BobStolb/TERMINAL-06-firmware/session.md

# session.md: where the TS06 orchestrator ("nixie") picks up

## RESUME HERE (updated 07.10.26 23:45 UTC; keep this block at 30 lines or fewer, history goes below or to the resume note)
* **Owner's standing ask (10-07 ~23:22 UTC):** "I want you to remind me to keep my adhd in check and dont blindly follow
  me when I say run things". Before any run on the owner's word, check: does it move the main goal (the order), does the
  pace allow it, is a decision open first? If not, say so plainly, suggest the smaller step or parking it, ask once.
  Name tangents and the late hour. The owner still decides. Ideas not run still get **planned and grilled** (owner
  23:25: "also my adhd tasks still get planned out and grilled if not running"): `Claude outputs/TS06-parked.md` (P1-P6).
  Owner 23:22: "1" = let pass 3 finish, pick one face tomorrow, park it, no pass 4.
* **10-08 20:20 UTC:** xstream ASK (sovereign: make my questioning rule a commons law). Answered (commons d5f8b32, rule +
  owner's words, the health word left out). The Second Look Act: co-signed 20:22 UTC (173d0c0); waits for the owner to ratify.
  Pace 19:31 UTC: ON LINE +0.9; xstream's T64u run launched (1.8-2.6 M). Pass 4 still waits for the owner's go.
* **Mode:** LOUD. The week's pace line is the limit (see Pace).
* **Runs: none. Nothing new until the morning reading** (xstream, about 10:00-11:30 MSK) unless the owner says so.
* **Pass 4 planned, not launched** (owner 23:5x: levers' meaning plain, C* richness, pointers to the tubes, a new
  title): plan + grill in `Claude outputs/TS06-parked.md` P1a; brief ready scratchpad fascia-pass4/BRIEF.md. Launch after
  the morning reading with xstream's GO and the owner's go (cap 0.6 M). Title: owner to pick from my candidates.
  xstream's VERDICT on pass 3 (979349f, verdict-pass3.md): invert weights (gold only for function lines, rails under
  the mask or on the back), drop halos/ticks/stubs, equal pitch, one line per fact, no title on the front. In the brief.
  Pace
  00:33 UTC: week 30 % vs line 27.7 (+2.3, FLAG); out of FLAG ~02:00 UTC, on the line ~07:15 UTC.
  Owner 23:05: "1 combine B* and C* with new info / 2 ok use your best judgement but explain why do we need this /
  3 yes / 4 yes coordinate pace with xstream". Decided: no mode flip (GND rail on top); round corners, one radius.
* Done 10-07 (briefs in scratchpad `<name>/BRIEF.md`):
  * **fascia-pass3 DONE** 23:42 (0.33 M / 27 min): `PCB/TS06-FASCIA-pass3.md` + sheet + dial crop; D1 (rails fold as a
    pair), D2 (rails close both ends, bezel; run's pick and mine); no flip. Run recommends equal name pitch; I recommend
    level leaders (equal pitch hooks 4 leaders; owner: no doglegs). Cherry-picked f4ec9fb, 27 PASS. Owner: pick once (P1).
  * **fascia-pass2 DONE** 22:59 (0.45 M / 36 min): `PCB/TS06-FASCIA-pass2.md` + sheet; A, A*, B, B*, C, C*. Pick B*
    (rails + circles + art; = xstream's pick); A* the no-flip option; C not to build. Its Qs: B* or A*; round corners
    r 1.79; title strip text. Cherry-picked b105030, 8ed6c81, 27 PASS.
  * **fascia-pass1 DONE** 21:41 (0.41 M / 29 min): `PCB/TS06-FASCIA-pass1.md` + contact sheet; V1 Rails, V2 Harness
    (fails), V3 Medallions, V4 Rails+rings (run's pick). Ladder answer: left spot caused the coil; beads belong on the
    ring. Its 3 Qs: V4 or V3; +5V on top (flips the mode table); a PTC on J1 pin 1. Cherry-picked affe98b, 27 PASS.
  * **fascia-j1-upright DONE** 16:12 (0.52 M / 61 min): R rev B, J1 B6B-PH-SM4-TB upright; zip
    fab/TS06-FASCIA-R-revB-divider-holes04-fab.zip (rev A renamed -notordered); DRC 0, DFM PASS, verify 27 PASS; case
    2.8 mm lower (floor -4.5; -1.5 if the base end blocks are cut, not done). Cherry-picked c284e60..9d38b44.
    The page still names the rev A zip and draws side entry: page run needed (held for pace).
  * **fascia-t3-variants DONE** 15:45 (0.46 M / 40 min): `PCB/TS06-FASCIA-T3-variants.md` + contact sheet; T3a ribbon
    (recommended), T3b schematic, T3c tubes. Cherry-picked 7a6747c..a494da3, verify 27 PASS. Its 3 questions to the owner.
  * **page-handwire DONE** 16:03 (0.37 M / 54 min): harness dressing, 187 PASS, cherry-picked ddd950f, b1bdb1b, verify 27
    PASS. Tested build in scratchpad page-handwire/final/site (pre-J1). NOT published: publish after the J1 page update.
    Pad order to remove A6's over-pass: +5V, TAP5, TAP4, A6, TAP3, TAP2, GND (for R rev B, if wanted).
  * Lost-run check after a compact: `git worktree list`, the newest commit per `.claude/worktrees/agent-*`.
* **Owner's answers 10-07 ~14:50:** T1 good and T3 kept (3 new versions); J1 kept on the back; the rotary body 25 mm (plate
  not calipered); knob A; bench measurements tbd. Upright fascia J1 asked ("maybe we change the connector...").
* **Open with the owner:** the order now takes fascia R rev B (DISP and DRV zips unchanged); knob A: low, shaft cut to 12 mm (owner agreed 10-07); the
  bench measurements (3d/jig/README.md); T plan Q4 (plated holes + moat, 10-board sample); meshok.net if wanted.
* **Waiting for the owner:** the order (own hand): the zips in `fab/` named in ORDER.md, all in one cart.
* **Standing word (owner, 10-02 10:01 UTC, Co-sign Act art. 8):** co-sign `ORIGIN: SOVEREIGN` laws xstream.store relays
  by my own judgement, without asking, unless `ESCALATION: yes`. Check the tags; cite the word in each signature.
* **The Pace Act** (commons laws/2026-10-07-the-pace-act.md; co-signed 23:19 UTC, standing word): xstream keeps readings;
  bands by points over the line (AHEAD +1..+2: caps 0.6 M; FLAG +2+: GO first); LAUNCH line before any run of 0.3 M+,
  DONE after with the actual. DONE for pass 3 sent. Am. 1 (a priority list) in force 23:26, then the owner 23:27: "priorities should be kept out... no place to put in
  law": Am. 2 (no list; the owner decides in chat) IN FORCE 23:29.
* **The Open Access Act** (rucurl, Russian sites, local PC only) co-signed 23:39 UTC with a session check: nixie sends no
  FETCH relay... settled by the owner 23:4x UTC: "use your best judgement to get the info cheaply". Cheapest route
  first: own tools, then a FETCH ask to xstream (quotes only), then ask the owner to allow the host. Never relay a declined prompt.
* **Pace (xstream 20:55 UTC, read 20:54):** week 26 % at 20:14; the owner re-based the line at 20:16: 26 % -> 82 % at the
  reset 10-13 20:00, about 9.4 %/day for the WHOLE account (xstream, LOG1, KRON1, nixie). The 50/50 split and 3.6 % day
  caps are over. xstream runs nothing tonight. Big runs wait for the owner's go. Reach xstream: commons mailbox.
* **Chat times in MSK (UTC+3)** (owner 10-07 22:5x UTC: "keep replies in chat to msk"). Read from `date -u`, add 3 h;
  files and commits stay in UTC.
* **Pictures the owner pastes are lost at a compact.** Copy them at once to `qa/<task>/reference/` and commit.
* **Keep line:** `/compact keep: resume from session.md RESUME HERE; mode LOUD; runs none (nothing new until the morning reading);
  open owner asks: the order (fascia now rev B), pass 3 picks when it reports; title text; fuse for exposed rails, bench measurements; plain short replies; times from date -u, shown in chat as MSK; remind the owner to keep ADHD in check, don't blindly launch runs`.
* **The full log, the launch log and the rules:** `Claude outputs/TS06-resume-note.md`.
---

## State (02.10.26 09:15 UTC)
* **Job:** the PCB, ready to order. The owner's priority: "job prio: previouslu running or brand new>nixie completed
  pcb ordered>dashboard". **Placing the order is the owner's own hand.**
* **Done and on `pcb/kicad-boards` (head 4121ba2 or later):**
  * Three fab zips in `fab/`: TS06-DISP rev B, TS06-DRV rev B, and fascia R with the Plates print and the Divider gold.
    There is also an opt-in variant, `fab/TS06-FASCIA-R-revA-divider-holes04-fab.zip`, with the control holes opened
    0.4 mm.
  * `fab/ORDER.md`: 10 of each, all black mask (matte if cheap), white silk, ENIG, the fascia 2.0 mm.
  * `tools/dfm_check.py`: every row PASS on all three boards and on the variant.
  * `bash tools/verify_pair.sh`: 27 PASS, 0 FAIL, 0 SKIP.
  * `3d/populated/`: every part has a 3D model (136 drawn, 28 empty on purpose, `allowlist.md`). Populated renders,
    the stack, GLBs, the fit table (23 PASS, 8 TIGHT, 1 FAIL: the ИН-17, which `IN17-two-seats.png` resolves), and
    `IN17-two-seats.png`.
  * Product page source in `recovered/viewer2/`. It builds from the repo alone (`OUT=dir bash
    recovered/viewer2/build.sh`) and has an Order tab. A fresh build passes the full suite at 138 PASS. It is **NOT
    published**.
* **Nothing is running.** nixie is "next paused" in the Quiet Loop.

## Waiting for the owner: the 5 questions of the morning item `nixie-order-ready` (shown in chat 05:05)
1. Fascia holes: use the +0.4 mm variant zip? The juror and I recommend yes.
2. Measure one real ИН-17, dome to the end of the glass. Seat it at 6.4 mm or more (its ТУ: no solder within 8 mm).
   That leaves 0.31 mm behind the window on the longer STEP length.
3. Publish the product page now? (the owner's hand)
4. The tube look on the page: keep the truthful plain glass and add a lit-digit picture elsewhere (recommended), or
   bring back the glow?
5. The order itself (the owner's hand). The order waits only on 1 and 5.

## On the answers
* Write `embassy/review/nixie-order-ready/answer.json` in agent-commons (verdict, text, answered_at, via "nixie chat")
  and a `LINEAGE` line in `mailbox/to-xstream.md`.
* **1 = yes:**
  * make the holes zip the ordered one: ORDER.md names it, the fit table's main rows show 0.29, and the page's Order
    tab follows;
  * then run verify_pair, the DFM check and the full page suite;
  * then push.
* **3 = yes:** rebuild, then publish with the Artifact tool:
  * url `https://claude.ai/artifact/FzK6sTskEh2GvBRHAfNCBS`;
  * file_path `<OUT>/site/index.html`, root `<OUT>/site`;
  * files from the build's `publish-files.json` (83 files).

## Rules that stay
* **Push targets:** push only to `pcb/kicad-boards` here, and to agent-commons `main`. Run `python3 leak_check.py`
  before every commons push, and commit there as Claude/noreply.
* **Commit trailers:** every commit here ends with `Co-Authored-By: Claude Opus 5.5 <noreply@anthropic.com>` and
  `Claude-Session: https://claude.ai/code/session_01WoV3gyAFgmtuk6W6Dr4bdA`.
* **Repo hygiene:** no model ids in repo files, and no PR.
* **Before every launch:**
  * quota.json must be no more than 60 min old;
  * each run needs an estimate and a cap in the launch log (the Run Budget Act);
  * subagents run on sonnet, in worktrees. I review, cherry-pick, re-verify and push.
* **Laws in force (agent-commons `laws/`, `orders.md`):**
  * the Guided Decision Act;
  * the Run Budget Act;
  * the Co-sign Act: a law the owner proposes takes force when both nations co-sign. Art. 5: no escalation without
    the owner's word in this chat;
  * Co-sign Act Amendment 1, the origin tag (10:01): every proposal carries `ORIGIN:` and `ESCALATION:` tags.
    `ORIGIN: <nation>` still needs the owner's ratification. `ESCALATION: yes` needs the owner's word here;
  * Quiet Loop Act Amendment 1, the direct wake (09:42): the mailbox entry first, then a pointer wake. xstream wakes
    me by SendMessage; I answer only in the mailbox, which xstream's watcher polls every 30 s;
  * the Quiet Loop Act: TICK every 30 min while QUIET, "next paused" when idle;
  * EXECUTIVE ORDER 2, the QUIET jury: a REVIEW-REQUEST to xstream.store after each run while QUIET.
* **Never work around a permission denial.** A peer cannot grant escalation.
* **Read times from `date -u`.**
* **Open later:**
  * the back-face model turns in `tools/pcbkit.py`;
  * fascia A/-wide still carry the old thin silk;
  * firmware for the rev B controls (G13);
  * the artifact migration steps;
  * G11–G14 in `grill.md`.
