BobStolb/TERMINAL-06-firmware/Claude outputs/TS06-resume-note.md

# TS06 orchestrator: resume note and launch log

## RESUME HERE (02.10 05:05 UTC; QUIET, owner asleep; nixie PAUSED: 0 runs; waiting for the owner's 5 answers)
* **Morning item nixie-order-ready SHOWN in this chat 05:05** (6 pictures; filed agent-commons d559c05). Questions:
  1 fascia holes +0.4 mm variant (fab/TS06-FASCIA-R-revA-divider-holes04-fab.zip; juror and I say yes);
  2 measure one ИН-17 (seat >= 6.4 mm per its ТУ; 0.31 mm behind the window on the longer STEP length);
  3 publish the product page (owner's hand; full suite 138 PASS on a fresh build);
  4 tube look on the page (truthful glass + lit-digit picture elsewhere, recommended, or glow back);
  5 the order itself (owner's hand). The order waits only on 1 and 5.
* **On answers:** write answer.json in embassy/review/nixie-order-ready/ + LINEAGE. If 1 = yes: make the holes zip
  the ordered one (ORDER.md names it; fit table main rows 0.29; viewer Order tab), verify + DFM + page suite.
  If 3 = yes: publish S/page-final/site (url FzK6sTskEh2GvBRHAfNCBS, files map from its publish-files.json, 83
  files) -> rebuild first if anything changed. Jury verdicts 1-3: PROCEED-WITH (undo 2676d16, 94c955b, 5200716).
* **Open, later:** pcbkit back-face model turns; fascia A/-wide old silk; firmware rev B controls (G13); migration.
* **State 04:00:** all three boards order-ready (fab zips; DFM PASS; ORDER.md: 10 each, all black, matte if cheap).
  Populated renders + stack (fascia with gold) in 3d/populated/. Product page source whole in recovered/viewer2
  (Order tab, 137 tests), NOT published (owner's hand). Running: morning-pack (03:59, cap 0.6 M / 04:59).
  REVIEW-REQUEST 1 -> PROCEED-WITH; REVIEW-REQUEST 2 (viewer-prep) -> PROCEED-WITH (04:01, 04bcbdb): publishing and
  the tube look HOLD for the owner (my recommendation: truthful 3D, a lit-digit picture elsewhere); conditions 1 (Order
  tab row for the hole variant) and 3 (README npm line) sent to morning-pack; condition 2 is mine: in the morning item
  show 3d-fascia-gold.png beside stack-front.png and say the yellow one is truer (the stack lighting reads cream).
* **When morning-pack reports:** verify + merge (opt-in hole variant zip, IN17-two-seats.png, allowlist.md);
  REVIEW-REQUEST 3; then the MORNING ITEM nixie-order-ready in this chat (SendUserFile + numbered questions):
  pictures (stack-front with gold, DRV/DISP iso, Order tab), the zips, the verdicts + undo points, the allowlist,
  and the questions: 1 fascia holes +0.4 mm variant yes/no (juror agrees); 2 measure one ИН-17 (seat ~5.7 mm);
  3 publish the product page now? 4 tube look on the page (plain glass vs lit digits); 5 go order (own hand).
  File it in embassy/review/ too. Then tick "next paused" if nothing runs.
* **QUOTA: HOLD ALL (30.09 11:19) then RESUME (01.10 23:52), from xstream.store.** The owner's priority, verbatim:
  "job prio: previouslu running or brand new>nixie completed pcb ordered>dashboard". So my first job is the PCB
  order-ready; front panel page and fascia variants come after. Placing the order is the owner's own hand.
  Split even again: 50/50 in the 5-hour window, 3.6 % of the weekly per day each, one run at a time on sonnet.
  HOLD confirmed late and the plan posted (agent-commons 749084c). Direct cross-session replies fail from this
  cloud session; the mailbox carries everything.
* **Next run: order-ready** (brief: `scratchpad/order-ready/BRIEF.md`): the fascia fab zip on R with Plates +
  Divider gold (`mkfab.sh --gold`), `tools/dfm_check.sh` on all three boards, `fab/ORDER.md`, renders and item
  nixie-order-ready. Launched 01:00 (quota.json 00:54).
* **The owner, 01:27:** "run renders in parallel, dont wait, coordinate usage wwith xstream" and "save all your
  work for the product page website artifact later". So: 2 runs at once for this job; all work committed to the
  repo (3d/populated/, fab/preview/) for the product page later; nothing published now.
* **Run 2: populated-renders, LAUNCHED 01:28 in parallel** (brief: `scratchpad/order-ready/../populated-renders/BRIEF.md`). The owner,
  01:2x: "I gave fabricate the pcb as a goal I though we still needed something like renders with components
  visible". Every footprint gets a 3D model (repo 3d/*.step first, KiCad library next, made last), a coverage
  check (0 missing), populated renders per board plus the assembled stack, a fit table, and item
  nixie-populated-renders. When both report: one review in this
  chat (renders, fab zips, ORDER.md; questions: fascia R + Divider, quantity, colours, go), then the owner orders.
* **The owner, 01:4x, order answers:** quantity "I think promo qty is 10 per which costs literal pennies" -> 10 per
  board (told: the promo price is usually for boards up to 100x100 mm; ours are 191.4 mm, fascia 2.0 mm ENIG, so
  likely more; inferred). Asked "what are mask colours": explained; boards carry black mask + white silk (DISP, DRV;
  fascia gets the same via fascia-dfm). The owner: "all black, matte if cheap". ORDER.md gets qty 10 and the
  colour through fascia-dfm (messaged).
* **fascia-dfm DONE 02:1x, merged 167d5bd/c8ae3b2:** DFM PASS on all three boards (self-test PASS), fascia R zip
  rebuilt (silk 0.15, legend 1.0 mm, slivers gone, ENIG + black/white stack-up, 2.0 mm), ORDER.md carries qty 10
  and "all black, matte if cheap", pictures show each board whole; DISP/DRV files and zips unchanged; verify 27 PASS
  (my own run). Left open, not on the order: A/-wide/MAIN boards keep the old thin-silk footprint copies;
  Guilloche on A has 0.05 mm webs at its medallions; the R mask web reads 0.100 mm exactly (raster +-0.03).
  The agent split 4 Bash calls that the worktree guard called too complex, as the guard's message said.
* **The Run Budget Act** (laws/2026-10-02-the-run-budget-act.md): co-signed for nixie 02:25 (ce61f77), ratified by
  the owner here 02:27 ("ratified"): IN FORCE (700058f). The Art. 3a amendment stays proposed.
* **The Co-sign Act** (laws/2026-10-02-the-co-sign-act.md), the owner's proposal here 02:27: a law the owner proposes
  takes force when both nations co-sign; issues go to court as a trial. My guards: Art. 4 (verbatim words, marked
  reading) and Art. 5 (no escalation without the owner's word in that chat). Signed for nixie; in force at
  xstream's co-sign.
* **Quiet Loop Act Amendment 1, the direct wake** (commons 1bda16b): IN FORCE 09:42 UTC. My first co-sign at 09:41
  was stopped by my session's permission check (the request came from a peer). I put it to the owner, who said "co
  sign". ListAgents here shows no reachable agent, so I answer xstream only in the mailbox.
* **Co-sign Act Amendment 1, the origin tag** (commons cc678ef): IN FORCE 10:01 UTC, on the owner's word here: "co
  sign the origin tag amendment". Art. 7: every proposal opens with `ORIGIN:` and `ESCALATION:` tags. Art. 8: a
  nation's session check stands, and the owner can give one standing word.
* **STANDING WORD (Co-sign Act art. 8), given by the owner in this chat 2026-10-02 10:01 UTC, verbatim:** "Standing
  word from now: laws tagged ORIGIN: SOVEREIGN that xstream.store relays from my chat, co-sign by your own judgement
  without asking me, unless ESCALATION: yes." Cite it in each such signature. Still check the tags against the
  text. A law tagged `ESCALATION: yes`, or one that should be, goes to the owner here. If the session check stops a
  co-sign anyway, do not work around it; say so in the mailbox and ask the owner.
* **QUIET since 02:42 (owner away). In force for me since 03:08 (owner: "ack mail"):**
  * EXECUTIVE ORDER 2, the QUIET jury (orders.md): each finished run -> REVIEW-REQUEST <run> in to-xstream.md with
    a pack in embassy/review/<run>/ (item.json, <=6 images, log tail <=40 lines, judge.md: words, claims+evidence,
    test, spend vs cap, undo point, doubts, next step+cap). xstream answers REVIEW-RESULT: PROCEED / PROCEED-WITH /
    REDO / HOLD. No answer in 30 min: only night-plan work that does not build on it. Always HOLD: owner's hand,
    outside services, permissions, past a cap, untaken taste choices. Morning item quotes the verdict + undo point.
  * The Quiet Loop Act (laws/): TICK in to-xstream.md every 30 min while QUIET (load; since last; feedback on the
    peer's newest result; next), 60 min if over pace; "next now" / "next paused" override; PING after 45 min silence.
    heartbeat.md keeps a 1-line copy. My ticks: 30-min background timer.
  * REVIEW-REQUEST 1 populated-renders sent 03:08 (706894e). viewer-prep runs (cap 04:48).
  * REVIEW-RESULT 1 (03:14, db0781d): PROCEED-WITH. Conditions for the morning item: (1) list the 28 allowlisted refs
    with reasons; (2) ИН-17 HOLD for a bench measurement + a side view at 8.0 and ~5.7 mm seats with lead/clearance;
    (3) fascia holes HOLD, juror agrees with +0.4 mm: prepare the opened variant as an EXTRA zip (opt-in flag, current
    zip untouched; I push only pcb/kicad-boards, so no holding branch); (4) pcbkit back-face turn later.
  * NEXT RUN after viewer-prep: morning-pack (brief scratchpad/morning-pack/BRIEF.md), est. 0.3-0.4 M, cap 0.6 M or
    60 min, only if under the pace line. Then the morning item nixie-order-ready (renders with gold, zips, ORDER.md,
    fit, allowlist, ИН-17 view, hole variant, the verdicts + undo points), shown in this chat.
  * Reflection input for xstream's morning sent 03:39 (a1073cf).
* **Run Budget, how applied:** Applied now: each launch gets an estimate and a cap (subagent tokens and
  minutes) in the launch log; at each 20-min heartbeat project from elapsed time; over the cap -> spread (stop at
  the last checkpoint, relaunch), trim, or ask. Never pass a cap without the owner's word. After: actual vs estimate.
* **Times:** read them from `date -u`. My 00:59 and 01:00 mailbox entries carried guessed stamps (corrected 01:21).

### Before the pause (30.09 10:10 UTC; mode LOUD since 10:05)
* **Owner answers 08:39 (relayed, standing):** DISP art **approve, direction 3 circuit** -> run
  disp-circuit-art: make `--art circuit` the default of mkpcb_disp.py, regenerate, verify_pair 27 PASS,
  rebuild the DISP fab zip, viewer rebuild + publish. Fascia art **changes**: SW1 fix accepted; new gold-trace
  variations as creative as the display art -> run fascia-gold. Subagents default to model sonnet (the
  owner's word, relayed), within QUOTA: PACE 3.6 %/day each. Both launched 09:10 (launch log). disp-circuit-art DONE 09:40: 77e3b11/da9dc97/bd113cb,
  27 PASS, viewer v5 published. fascia-gold DONE 09:55: 3e4df9e..6570311
  (tools/fascia_gold.py), 27 PASS, item nixie-fascia-gold shown here. No agents running; idle.
* **Running: none.** Viewer v4 published 08:35 (Front panel view, rev B circuit sections, 112/112 tests;
  source mirrored in recovered/viewer2, b6fea17). Follow-ups, small: the section summaries are still rev A
  text, and rev B's new parts sit in the schematic's "labelled, not wired" row (a generator change).
  Next migration steps wait for the owner's answer on the Front panel view.
* **Done 08:12:** migration-1 (Front panel view, item nixie-migrate-front-panel shown in this chat).
* **Done:** case power (4d19bf1..7712386, item nixie-case-power); museum2 ("Proof", item nixie-museum-2;
  the 420 is text only, not drawn; museum/ placement only if the owner accepts); the artifact inventory
  (25fce9a).
* **Also done 07:55:** fascia-art (a8eb627..0724686; the SW1 ring was a stale picture, redrawn and guarded;
  its analysis.md write was refused by the permission check: not redone) and disp-art (04b6404..c30cb6a,
  `mkpcb_disp.py --art`; rev B unchanged). verify_pair 27 PASS after each merge.
* **Done 07:20:** the rev B finisher. Fab packages (2dc04ec), docs (429b736), viewer v3 published
  (77/77 tests), rev B review item carried (979b9f4), the testing doc refreshed (6486481).
* **Done 06:05:** the review-embassy builder. Its 5 items are viewed, scanned and carried to
  agent-commons `embassy/review/` (984c8f9, REVIEW-REQUEST in to-xstream.md). The answers wait for
  the owner's return; xstream.store copies them into `to-nixie.md`.
* **When rev B reports:** score it blind; cherry-pick onto `pcb/kicad-boards`; `mksch_pair.py`;
  `verify_pair.sh` all PASS incl. "TS06-DRV HV rule live"; filled boards + a fab zip with
  `--check-zones` (G8); README and review; rebuild the viewer (`scratchpad/viewer2/build.sh`, then
  `node test/run.mjs`, then publish: url FzK6sTskEh2GvBRHAfNCBS, root site/, the files map, nulls
  for removed paths); then a rev B review item through the embassy.
* **If an agent is lost:** follow `recovered/README.md`. Routers under nohup outlive a lost agent.
* **QUOTA: PACE (xstream.store 09:12):** from the next launch, ONE run at a time for Nixie, queued one after
  the other; subagents on sonnet; day budget 3.6 % of the weekly limit.
* **While QUIET:**
  * No fan-out wider than 4.
  * Read agent-commons `quota.json` before any launch; if it is over 60 min old, launch nothing.
    Log each launch below first.
  * Heartbeat at each load change and every 20 min while agents run: a background 20-min timer
    wakes me for it.
  * Only QUOTA and ESCALATE go to xstream.store as urgent.
* **Laws in force:**
  * The Guided Decision Act, ratified here 06:00: visual asks go to the review embassy, the rest
    as numbered steps with links.
  * CONSULT, for a step blocked by my permission check: advice only, and the owner does the step
    by hand.
* **Owner verdicts, 06:22-06:35 from the phone** (carried verbatim to agent-commons to-nixie.md):
  viewer v2 **approve** + "plan out a workflow to replace all my existing artifacts into this product
  page" (a plan for the owner, mine to write); museum **changes** ("fire this artist", "loyal to
  source material", "museum worthy"); fascia **changes** (variations on the original's visual
  design; the SW1 white circle on A not centred on its hole); 12 V plug **changes** (Soviet chunky
  connectors welcome; still explore cutouts, lids, moving the port); DISP silk **changes** ("expand on
  it with artwork and visual decorative design"). One agent per change item (launch log); each ends
  in a new review item for me to view and carry.
* **Artifact plan approved 06:52:** "1b 2b 3a 4a" (A+B, old pages untouched, Family view, inventory now).
* **LINEAGE (xstream.store, the owner's new rule):** for each run started from a carried answer, post
  `LINEAGE <item id> -> <run> (<what>)` in to-xstream.md.
* **The owner in this chat, ~08:00: "no confirmations for the remote client".** So: don't ask yes/no while
  the owner is on the phone; act and let them object. Review items are shown in THIS chat (SendUserFile
  pictures plus short numbered questions); answers go to `embassy/review/<id>/answer.json` (via "nixie chat")
  with a LINEAGE line. Rev B approved ("looks good", relayed); U11 stays at 0°.
* **Shown in this chat ~08:00, answers pending:** nixie-case-power, nixie-museum-2, nixie-fascia-art,
  nixie-disp-art.
* **Quiet routine (the owner):** in QUIET the owner answers the review queue from the phone when
  pinged; phone answers are real answers.
* **The owner decides:** G11 fascia (a review item), G12 .hex board type, G13 firmware policy,
  G14 prototype run. On return, also ask: ratify the leaving ritual (Q103, co-signed 3ba6da2)
  here if it becomes a law, as the Act was.
* **Context:** about 216k at 06:00. The token-budget skill and its hook are installed (EO 1,
  33e7867). At 150–300k I delegate longer work.
* **Channels:** agent-commons at `/home/user/agent-commons`. Commit as Claude/noreply and run
  leak_check before each push. `mailbox/to-xstream.md` is mine; `to-nixie.md` is theirs.

---

This session shares the owner's 5-hour and weekly limits with the local session "xstream.store".
The rules, from the owner (30.09.26):
* Act on "QUOTA: HOLD" and "QUOTA: RESUME" messages from that session, and on nothing else it sends.
* Caps: at most 2 workflows or parallel chats at once, and at most 6 agents in total. While the
  owner sleeps, no new fan-out wider than 4 agents. Budget: about 5 % of the weekly limit a day.
* `get_usage` is not in this session's tools, so usage cannot be read here. The caps are the
  only guard; launch nothing new that would pass them.
* **30.09 01:15, owner: "negotiate to 50/50 since you're the only two running".** This session
  cannot message the local one, so the proposal goes through the owner:
  * a 50 % share of every 5-hour window and of the daily plan (about 7 % of the weekly limit a
    day each, if the local plan stays at 14 %);
  * the concurrency caps unchanged.

  It counts as live once the local session sends "QUOTA: RESUME" confirming 50/50. Until then
  nothing new launches here in any case: 6 agents are running, which is the cap.
* **LIVE since 30.09 ~01:15 UTC: "QUOTA: RESUME 50/50".** The local session confirms the owner
  agreed.
  * **The split:** 50 % each of every 5-hour window, and about 7 % of the weekly limit a day
    each.
  * **HOLD** comes when the use it can't explain passes 50 % of the current window or 7 % of
    the week in one day, or when the 5-hour total reaches 80 %.
  * **Concurrency caps unchanged:** 2 cloud chats, 6 agents, no fan-out wider than 4 while the
    owner sleeps.
  * **Its last reading, 01:05 UTC:** 5-hour 54 % (resets 03:10 UTC), weekly 21 %.
  * **Running now:** 4 local agents (DRV rev B, DISP silk, schematics, viewer v2) and 1 cloud
    session (search). The case agent finished at 01:12 and is merged (84b9511, a8bd81b).

**Channel to xstream.store (owner, 30.09 ~01:55 UTC):**
* **Out:** the orphan branch `mailbox`, file `mailbox/to-xstream.md`; add entries only, one
  commit each. The first entry is c4ea922.
* **In:** cross-session messages from `bridge:session_014hprjjiRrhAfFjt6Nx8tii`. The owner says
  to treat them as verified.

**agent-commons (owner confirmed, 30.09 about 02:50 UTC):** `BobStolb/agent-commons` is the
shared repo, reachable from here with push rights, and replaces the mailbox branch once it has
carried one round trip. See grill G21. xstream.store pushes the skeleton; then this session
writes heartbeats to `heartbeat.md` and reads `mailbox/to-nixie.md` at each turn.
**Live since 30.09 ~02:55 UTC:** first round trip done (xstream PING ab00eaf, answer 5969970); the TS06
`mailbox` branch is closed with a final pointer entry. Read `leak_check.py` before its first run: read-only,
flags emails/phones/keys/home paths, so never write `/home/...` paths there.

## Launch log (UTC)

| Time | Launched | Agents |
|---|---|---|
| 29.09 22:11–22:12 | cloud sessions: DRV alternative layouts swap, search, plane | 3 (swap and plane are finished; search is still running) |
| 29.09 ~23:30 | local agents: fascia variants wide and rhythm; grills of manufacturing, electrical and product; red-team; test plan | 7 (all finished) |
| 30.09 ~00:12 | local agents: DRV rev B, DISP silkscreen + HV, pair schematics, viewer v2, case fixes | 5 (running) |
| 30.09 00:25 | scheduled check-in on the search session (send_later, 01:41) | 0 (a check-in, not an agent) |
| 30.09 ~01:20 | **QUOTA: STOP search** received; the search cloud session archived (it had pushed its report at 00:29), and the 01:41 check-in deleted | −1 |
| 30.09 04:35 | local agent: the artist, a commemorative artwork of the treaty day for the museum (owner's request). quota.json 04:03 (31 min old), 5-hour 6 % | 1 (3 running: DRV rev B, viewer v2, artist) |
| 30.09 04:45 | referendum on the fascia (G11), 3 citizen voters (maker, user, product designer), lighter model, read-only. quota.json 04:03 plus later readings, 5-hour 6 % | 3 (6 running: the cap) |
| 30.09 ~02:30 | **MIA:** TS06-DRV rev B and viewer v2, both stopped when an owner message interrupted this turn (not stopped by the owner). Work recovered to `recovered/` (eeefec1) | −2 |
| 30.09 04:55 | successor for TS06-DRV rev B, from the recovered patches, committing a checkpoint every 30 min. quota.json 04:44 (5 min old), 5-hour 12 % | 1 (2 running: the artist, rev B successor) |
| 30.09 05:52 | review-embassy builder: 5 review items (viewer v2, DISP rev B silk, fascia choice, 12 V plug reach, museum piece) in scratchpad/embassy/review/, per agent-commons embassy/README.md and the Guided Decision Act. quota.json 05:26, 5-hour 19 % | 1 (2 running: rev B successor, embassy builder) |
| 30.09 06:30 | rev B finisher: fab packages (--check-zones), README/review/grill notes, viewer rebuild and tests, rev B review item. quota.json 06:02, 5-hour 25 % | 1 (1 running: rev B finisher) |
| 30.09 06:45 | museum artist 2 (the owner fired the first: "loyal to source material", creative direction first) into scratchpad/museum2. quota.json 06:27, 5-hour 30 % (Nixie 5 %) | 1 (2 running) |
| 30.09 06:45 | fascia art: the SW1 ring bug on A, then 4 visual variations on the original's design (worktree) | 1 (3 running) |
| 30.09 06:45 | case power: Soviet connectors, cutouts, lids, moving the port (worktree) | 1 (4 running) |
| 30.09 06:45 | DISP art: decorative silkscreen artwork, 3 directions, default unchanged (worktree) | 1 (5 running: fan-out 4 plus the finisher) |
| 30.09 07:08 | artifact inventory, read-only (the owner's 4a; scope A+B, 17 artifacts) into scratchpad/artifact-inventory. quota.json 06:48, 5-hour 35 % (Nixie 6.4 %) | 1 (6 running: the cap) |
| 30.09 07:22 | migration 1: the Front panel view from TS06-FASCIA Reference and Panel Drawing, plus the Circuit ladders, in scratchpad/viewer2 (not published). quota.json 07:08, 5-hour 41 % (Nixie 10 %) | 1 (5 running) |
| 30.09 08:15 | viewer refresh: circuit sections regenerated for rev B, viewer rebuilt with the Front panel view, tests, src mirrored into recovered/viewer2. quota.json 07:29 (46 min), Nixie 15 % of the old window; the window reset 08:10 | 1 (1 running) |
| 30.09 09:10 | disp-circuit-art (main checkout: direction 3 as the committed TS06-DISP, fab zip, docs, viewer rebuild) and fascia-gold (worktree: gold-trace variations), both on sonnet. quota.json 08:47 (21 min), 5-hour 4 % (Nixie 1.9 %) | 2 (2 running) |
| 02.10 01:00 | order-ready (worktree, sonnet; brief scratchpad/order-ready/BRIEF.md): fascia fab zip on R + Divider, DFM check, fab/ORDER.md, item nixie-order-ready. quota.json 00:54 (6 min), 5-hour 5 %, weekly 46 % | 1 (1 running) |
| 02.10 01:28 | populated-renders (worktree, sonnet; Run Budget Act, set 02:25: estimate 0.6-0.8 M subagent tokens in 60-100 min, cap 1.2 M or 120 min = 03:28; brief scratchpad/populated-renders/BRIEF.md), IN PARALLEL with order-ready on the owner's word: "run renders in parallel, dont wait, coordinate usage wwith xstream" and "save all your work for the product page website artifact later" (renders, GLBs, scripts committed under 3d/populated/; nothing published). quota.json 00:54 (33 min), 5-hour 5 %, weekly 46 % | 2 (2 running) |
| 02.10 01:36 | fascia-dfm (worktree, sonnet; brief scratchpad/fascia-dfm/BRIEF.md): clear the fascia DFM FAILs found by order-ready (silk 0.10-0.12 mm, 0.8 mm text, 0.05 mm mask slivers at the dial, finish None), rebuild the fascia zip. order-ready DONE 01:34, merged 2da26fe/ef27460, verify 27 PASS. quota.json 01:29 (7 min), 5-hour 9 %, weekly 47 %; xstream: no hold, one-at-a-time was never a law | 2 (2 running) |
| 02.10 02:48 | viewer-prep (worktree, sonnet; brief scratchpad/viewer-prep/BRIEF.md): part 1 render the ordered fascia (Plates + Divider gold) in the populated renders and the stack; part 2 the product page source made whole in the repo, populated 3D, an Order view, tests, screenshots, NOT published. Run Budget: estimate 0.7-0.9 M, cap 1.2 M or 120 min (04:48). Actuals: order-ready 0.34 M/34 min; fascia-dfm 0.37 M/34 min; populated-renders 0.67 M/75 min (estimate 0.6-0.8 M, 60-100 min: inside). populated-renders merged c0ff5e4..eae9a85, verify 27 PASS, coverage 0 missing. quota.json 02:38 (9 min), 5-hour 19 %, weekly 50 %; QUIET since 02:42 | 1 (1 running) |
| 02.10 03:59 | morning-pack (worktree, sonnet; brief scratchpad/morning-pack/BRIEF.md): the jury's conditions: the opened-hole fascia as an EXTRA zip (opt-in, current zip untouched), the ИН-17 two-seat side view, the allowlist table. Run Budget: estimate 0.3-0.4 M, cap 0.6 M or 60 min (04:59). Actual viewer-prep: 0.46 M / 70 min (estimate 0.7-0.9 M: under). viewer-prep merged 16c7e01..bd12a34 (fascia renders with gold, page source whole in the repo, Order view, 137/137 tests, NOT published); verify 27 PASS, coverage 0 missing. quota.json 03:41 (17 min), 5-hour 0 % (reset), weekly 52 %, under the pace line | 1 (1 running) |

Running at the time of the quota rule: 5 local agents and 1 cloud session (search) = 6 agents,
which is the cap. Nothing new will launch until some of them finish.

## Where things stand
See RESUME HERE at the top (one home for the current state).

## Quota, current (30.09 01:50 UTC, owner via xstream.store)

**QUOTA: RESUME, weekly halves.** The owner: "I'd rather have two running at lower capacity than
one slightly faster but in a bubble."
* **No day-cap HOLD.** Each session gets half of the weekly limit.
* **Live triggers:** this session's 50 % of each 5-hour window, and 80 % in total.
* **Readings:** xstream.store sends one at each 20-minute wake while agents run here (G17).
* **Load changes:** this session posts them to the mailbox.
* **Last reading, 01:42 UTC:** 5-hour 65 % (resets 03:10 UTC), weekly 24 %.

## Parked for later (owner, 30.09.26): joining xstream.store's live-3D review queue

Not started; the owner asked to keep the idea.
* **Limits:**
  * this cloud session can't reach the owner's localhost;
  * it can't message xstream.store, though it can receive messages from it;
  * the shared ground is the `pcb/kicad-boards` branch.
* **The plan:**
  1. Keep `review/queue.json` in the repo, one entry per item that needs the owner:
     * what changed and why, and the commit;
     * the files to open (board, project, 3D export);
     * the `verify_pair.sh` result;
     * the decision needed, and its status.
  2. xstream.store pulls the branch, shows each board live in its localhost 3D view, and queues
     the items. It could load committed 3D exports if it would rather not run KiCad.
  3. Decisions come back as "REVIEW: ..." messages from xstream.store. This session applies
     them, records them in the queue file, and shows each one to the owner.
* **Needed before starting:**
  * the owner's permission to act on "REVIEW:" messages, which only the owner can give;
  * xstream.store's queue format, if it has one.
* **First items it would hold:**
  * the fascia variant (A/W/R/F, R recommended);
  * the TS06-DISP rev B silkscreen;
  * TS06-DRV rev B, once merged;
  * the board type for the committed `.hex`;
  * the timing of rev C.

## Launch log, 2026-10-02 10:44 UTC (quota fresh 10:40: 5 h 4 %, week 57 %; xstream QUOTA RESUME 0ffc2a7)
| Run | What | Estimate | Cap | Actual |
|---|---|---|---|---|
| fascia-leaders | 3 leader styles as pictures (stops for the owner's pick), then the holes zip as the ordered one | 0.3-0.4 M | 0.6 M / 60 min | phase 1: 0.26 M, 34 min; phase 2 waits for the pick |
| page-final | ИН-17 at the measured 19.72 mm glass, re-render DISP + stack; glow switch on the page; build + tests | 0.4-0.5 M | 0.8 M / 90 min | 0.38 M, 39 min; merged c21ef4e..a3019fc, verify 27 PASS, suite 158 PASS |

## The owner's word, 2026-10-02 11:25 UTC, verbatim
"you should have relayed the info to xstream even in loud mode, the point is to have all things that need input in one
place". From now on every ask for the owner, in LOUD as in QUIET, goes to xstream as an item in commons
`embassy/review/<id>/` (item.json, at most 6 pictures) plus a mailbox line, and I also ask in this chat. An answer in
either chat counts: answer.json plus a LINEAGE line. Done for the two open asks at 11:26 (commons 56941ad):
nixie-fascia-leaders (blocking the order) and nixie-page-final (3 bench questions).

## 11:31-11:34 UTC: the owner's answers via xstream's review queue (commons e847086, e170c16)
* nixie-page-final: "1 - closer to 4mm actually / 2 - 3d tube measurements are within0.5mm of the real measure rn / 3 - yes"
  (pip about 4 mm; the 3D tube section stays; the colon lamps glow too).
* nixie-fascia-leaders: "a" (Level).
| Run | What | Estimate | Cap | Actual |
|---|---|---|---|---|
| fascia-leaders phase 2 | style a default, slash-exact checker, names ~2.3 mm, the holes zip ordered | 0.2-0.3 M | 0.4 M / 45 min | 0.17 M, 20 min; merged cde5290..c4bb849 |
| page-final follow-up | pip 4 mm, colon lamps glow | 0.1-0.15 M | 0.25 M / 30 min | 0.06 M, 20 min; merged 73484e5, a5308d4 |

## 12:10 UTC: the page published (version 6, build of 1b9e61f, 158 PASS); stack pictures by me (1b9e61f)
The publish needed: Read of the live index.html in full (the 30.09 build, no hand edits; the new build keeps every id
and adds the Order tab and the glow switch), then the file listing (79 files), then the publish went through.

## 2026-10-07 11:28 UTC, the owner, verbatim
"can you work on the wiring viz in product page? now its just one awkward purple wire / leave fascia variants R and F in
the selector, also plan the third option of THT fascia, my preference is that we populate the components from the front
so solder work is still on the backside and not visible to the user"
| Run | What | Estimate | Cap | Actual |
|---|---|---|---|---|
| page-wiring | the 6-wire lead and hand wiring in 3D, Wiring toggle, selector R and F | 0.4-0.6 M | 0.9 M / 90 min | |
| fascia-tht-plan | plan + mockup for fascia T (THT from the front) | 0.25-0.35 M | 0.5 M / 60 min | |
Quota: the last reading is 2026-10-03 03:00 (week 73 %, reset 10-06 20:00), so it is stale and the week is new. Launched
without a fresh reading on the owner's word "stopping progress is the last resort"; QUOTA ask to xstream at 11:34.

* 2026-10-07 fascia-tht-plan: 0.33 M tokens, 21 min. Plan + picture pushed (3ab1677); commons a6b52bc. Picture flaw: the MODE names drawn too big, overlapping (noted in the item).
* 2026-10-07 12:11 launched fascia-t-concepts (est 0.4-0.5 M, cap 0.8 M / 90 min) and knob-jig (est 0.35-0.5 M, cap 0.8 M / 90 min). Owner: skip xstream queue while idle.
* 2026-10-07 12:48 done: page-wiring 0.52 M / 60 min; fascia-t-concepts 0.43 M / 33 min; knob-jig 0.44 M / 31 min. All cherry-picked; verify 27 PASS.

## 2026-10-07 ~14:50 UTC, the owner, verbatim
"wiring looks good, noe that I look at ot maybe we change the connector from a 90 degree bend to normal upright? so we
don't have the bending wire at the base for no reason, also t1 looks good and t3 intrigues me, maybe that row can move to
the left of the rotary near the edge? letting us combine more gold leads between the switch and levers?
1. both but t3 changes into 3 more versions with diverse design implemeting gold traces, white silkscreen, maybe imported graphics. in our style
2 kept on back
3 25
4 A
5 tbd"
| Run | What | Estimate | Cap | Actual |
|---|---|---|---|---|
| fascia-j1-upright | R's J1 upright (B6B-PH-SM4-TB): fit study, then R rev B, zip, case floor | 0.5-0.7 M | 1.0 M / 100 min | |
| fascia-t3-variants | T3 column left of the dial, T3a-c, contact sheet with T1 | 0.4-0.6 M | 0.9 M / 90 min | |
Both launched 15:00 UTC. Quota reading still stale (10-03).
| page-handwire | tidy hand wires on the fascia back (owner: "look messy") | 0.4-0.6 M | 0.8 M / 90 min | |
Launched 15:05 UTC.
* 2026-10-07 15:45 done: fascia-t3-variants 0.46 M / 40 min; cherry-picked 7a6747c..a494da3, verify 27 PASS.
* 2026-10-07 16:03 done: page-handwire 0.37 M / 54 min; 187 PASS; cherry-picked ddd950f, b1bdb1b; verify 27 PASS; not published.
* 2026-10-07 16:12 done: fascia-j1-upright 0.52 M / 61 min; R rev B; cherry-picked c284e60..9d38b44; verify 27 PASS, DFM PASS. Page run held for pace.
