BobStolb/TERMINAL-06-firmware/Claude outputs/TS06-pair-review.md

# TS06-DISP + TS06-DRV: design review, and what it means for the case

A critical pass over the through-hole pair: what it gets right, what is weak, what was fixed
on the way, and what is still open before an order. The last part turns the stack's geometry
into suggestions for the case, which has not been started.

## Verdict

The pair meets the brief electrically:
* through-hole only;
* no vias on either board;
* a display board that carries nothing but the tubes;
* two boards that plug together with no harness.

Both boards pass KiCad 10's DRC with nothing unconnected. TS06-DRV has no errors; TS06-DISP
has two, the accepted overlap of the colon lamps' courtyards with the M10 tube, which waits on
a test fit (see `PCB/README.md`, "Checked"). An independent audit traced every anode and every
digit through both boards and the firmware.

**The pair now has schematics** (`PCB/TS06-*/TS06-*.kicad_sch`, from `tools/mksch_pair.py`), one sheet per section. They are checked against the boards net for net, and KiCad's ERC, run on this pair for the first time, reports 0 violations. Its first run found two real errors, both undriven power inputs. PWR_FLAGs now mark where 12 V and GND really arrive.

`tools/verify_pair.sh` runs every check in one command, including two that read the written
files with KiCad's own geometry: the mate of all 63 strip pins and 4 standoffs, and the pours
as KiCad fills them. **The committed boards store no zone fill:** refill before plotting Gerbers
(press B, or `kicad-cli pcb export gerbers --check-zones`). The display's LED return, BL_K,
exists only as a pour, so a Gerber plotted unfilled leaves all nine LEDs open.

**One finding blocked an order, and it was mechanical:** the two ИН-17 were placed 13 mm apart,
where their Ø20 stems need 20.5. It came from the tube coordinates every board so far had used.
**It is fixed.** The owner chose to widen the boards to 191.4 mm and keep the Gyver pitch.
Both boards were then re-placed, re-routed and re-verified (next section).

A second round of four independent reviews (30.09.26, next section) found no blocker for the
boards, and several things that DO need new copper on the driver board:
* an independent over-voltage clamp for the 185 V rail (E1);
* 0.8 mm between bare 185 V pads and other copper, per IPC-2221B (E3);
* footprints for the 0.5 W resistors actually on sale (F4);
* a real inductor, and a few protection parts.

These make up **TS06-DRV rev B**, which is now routed and merged (30.09.26, next section). The
display board needed only its silkscreen and a few clearances. The mechanical points from the
first round still stand:
* the stack height;
* the order in which the strips are soldered;
* a few tall parts;
* the case openings for the two connectors.

## TS06-DRV rev B, 30.09.26

Rev B puts the second grill's driver-board items into copper (rev A is 78105d6). The full list,
part by part, is in `PCB/README.md`, "TS06-DRV rev B: what changed":
* the independent over-voltage clamp (E1): VD5-VD7, R75, R76 and VT2 on PWM_G;
* 0.8 mm from every bare 185 V pad to all other copper, as a KiCad rule (E3);
* the USB back-feed diode VD3 (E5) and the input TVS VD4 (E8);
* the fascia inputs' 1 M pull-down on A6 and 1 k + 10 nF on D7 and D8, placed by hand between
  the strips and J1 (E11);
* 0.5 mm at the cathode pads, with oval-pad decoder sockets (E10);
* МЛТ-0,5 footprints (M4), a real L1 (M2), U13 on a male PLS-5 with its legend (M1), larger
  VT21 and J1 holes (M7);
* copper keep-outs round the standoff holes (M12, R1), silkscreen at the fab's floor (M8), the
  DNP attribute (R13);
* a route that reproduces: a fresh `--route` rebuilds the saved one byte for byte (R6).

**Where it stands:**
* `tools/verify_pair.sh`: **27 PASS, 0 FAIL, 0 SKIP**. That includes KiCad's DRC on TS06-DRV
  (0 errors, 0 unconnected), the live HV rule, ERC, the mate from the written files and the case
  model.
* The case model reads the new parts' heights: the case is **81.6 mm deep** (rev A 83.6).
* The fab packages are built from the committed boards, pours filled (`fab/`, `tools/mkfab.sh`).
  Nothing is ordered.

| Scored from the board files | Rev A | Rev B |
|---|---|---|
| Segments / vias | 1097 / **0** | 1164 / **0** |
| Signal copper / its floor | 5936 / 4479 mm = 1.33 | 5918 / 4533 mm = **1.31** |
| Straight (0°/90°) share | **86.1 %** | 83.3 % |
| DIP orientations | 3 | 4 |

**One change is not on the list: U11 now stands at 0°,** a fourth DIP orientation (finding 5).
It came with the placement recovered after the layout agent was lost. Everything passes with it.
Whether to turn it back to 180° is the owner's choice; that would mean routing the board again.

**What no check can show:** the clamp's trip voltage (225-270 V) is computed from the parts'
tolerances. It is measured only on the bench (`PCB/README.md`, "Open before fabrication").

## TS06-DISP silkscreen, 30.09.26

The display board's silk now carries art: **the circuit as ornament**, the owner's choice of
30.09.26 from three directions ("the best for display pcb is circuit as ornament"). It is the
board's own circuit drawn in white silk: the ИН-12 bus strands and the cathode order on the
front where the clock shows the board, every socket's pinout on the back. The copper did not
change. `tools/verify_pair.sh` still gives 27 PASS (77e3b11), KiCad's DRC still shows only the
two accepted colon courtyard errors, and the fab package is rebuilt (`fab/`, da9dc97).
`--art none` on `tools/mkpcb_disp.py` writes plain rev B.

## What holds up

* **A wrong cathode order at the bench is a firmware fix, not a new board.** Every cathode on
  both boards is driven by a К155ИД1 whose input code the firmware chooses: the ИН-12 bus and
  the ИН-17 pair through U2 and U17 on A0–A3, the two ИН-15 through U15 and U16 on the
  expander's port A. If gate 3 (ИН-17 lead order) or gate 4 (ИН-15 pinouts) comes back
  different from the maps the boards were drawn with, the fix is a lookup table. Only three
  things are physical: which pin of each tube is its anode, the RTC module's pin order
  (gate 6), and the ИН-17 pip (gate 5). The ИН-12's hole-to-function map is already closed
  from the inherited board's copper. Gate 2 (sustaining voltages) only sets the anode
  resistor values, which are through-hole parts and can be changed at any time.
* **High voltage stays in its own lanes.** Every 185 V net is its own net class (0.6 mm
  clearance, which KiCad's DRC enforces from the project file). Bare high-voltage pads are
  0.8 mm from every other pad (IPC-2221B A6). `checkcopper.py --hv` is clean on TS06-DISP.
* **The display board is drawn by hand, every line.** The ИН-12 bus is ten parallel zig-zags
  threaded through the sockets on the back face, the way Gyver's tube half does it. The
  ИН-17 and ИН-15 bundles wrap their tubes from above. Anodes and LEDs drop straight to the
  bottom strips. There is nothing there for a router to have made ugly.
* **Every change of face happens in a part that is in the circuit anyway.** A through-hole pad
  is the only place a net may change face, so the driver board is placed around its series
  resistors:
  * the four lines that share the corridor beside the Nano (the converter's PWM, the colon,
    the "m" LED, the S1 opto) end in four standing resistors at its exit;
  * the opto resistors of the minutes and S10 (the 470 R in series with each opto's LED)
    stand under the Nano;
  * the I²C pull-ups and the fascia's ladder filters stand in one column beside the hours'
    optos. A7, A6, SCL and SDA reach the column on the front face, threaded between the
    optos' pin rows, and leave it on the back face.

  No wire links and no zero-ohm jumpers.
* **On the driver board, the long buses are drawn too.** Port A of the expander runs up the
  left edge as one eight-line bus. The LED ribbon runs in lanes under the bottom strips. The
  U17 branch of A0–A3 drops down a corridor beside the Nano and enters U17 between its rows,
  the one approach that lands every line on its own pin without a crossing. The Nano's
  fan-out is drawn as well: every pin below the module except D7, D8 and D11, which are
  drawn only as far as the gap beside U2. The router fills in the rest: those three lines
  onwards, the I²C pair past its pull-ups, the rails and the wiring inside each cell.

## Findings, most serious first

### Fixed: the two ИН-17 did not fit 13 mm apart

TS06-DISP puts S10 and S1 at x 104.605 and 117.605: 13.0 mm between centres. It carried that
from TS06-MAIN, which took it from the FreeCAD assembly. The ИН-17's own record says it cannot
work: `knowledge/TERMINAL-06-measurements-IN17.md` Rev 5, closed from a factory outline drawing
on 09.09.26.
* The ИН-17 is a round **Ø20 stem** flattening to a 14 mm face.
* Concept Rev F spaced the pair **20.5** apart for exactly this reason: "a 3 mm face gap puts
  the stems 17 apart and they touch".

At 13.0:
* the two stems overlap by 7 mm;
* S10's stem overlaps M1's glass;
* S1's stem overlaps ИН-15Б's glass.

The case model's check (`3d/case-pair/checks.md`, row 9) found it; the repo's tube record
confirms it. No courtyard check could see it, because the ИН-17 footprint has no lead circle
yet (gate 5) and its courtyard is only the leads.

**What fixing it costs.** Spacing the seconds pair at 20.5 needs about 13 mm more of the row
between M1 and ИН-15Б. There are two ways to find it:

| | Keep the 176 mm boards | Widen the boards (Rev F's face is 204 mm) |
|---|---|---|
| How | Close the ИН-12 pairs from 23.4 to ~21 mm; close the ИН-15 pair to 20.5; use most of the right margin | Keep every other pitch; move the ИН-15 pair ~13 mm right; boards and case ~13 mm wider |
| Look | the tubes nearly touch; not Gyver's pitch | as drawn, with a wider clock |
| Work | both boards re-placed along x | both boards re-placed; the fascia is not tied to the tubes |

Either way, the display board's copper and XP12 move, and so do the driver board's XS12 and
the decoder rows under it, which means a re-route. The layout method here makes that
routine, but the look is a design decision, so it is left to the owner.

**Fixed on 29.09.26: the owner chose to widen the boards and keep the Gyver pitch.**
* **The display:** S10 and S1 now stand 20.5 apart, each stem 2.2 mm from the glass beside
  it. The ИН-15 pair moved 15.4 mm right, and both boards are 191.4 mm wide.
* **XP12:** still one strip, now 31 pins. Three spares take up the 7.62 mm the ИН-15 group
  moved beyond the ИН-17 group.
* **The driver board:** re-placed by blocks and re-routed. Round 15 had 0 nets sharing, and it
  has 0 vias and 0 DRC errors.
* **The case:** its check now reads 0.5 mm stem to stem, the margin Rev F chose, and the case
  is 204.4 mm wide, Rev F's face.

Gate 5, a real ИН-17 on calipers, should still confirm the Ø20 stem: one caliper reading gave
19.30 mm.

### 1. The 11 mm stack is a sum of two catalogue numbers: check it against the parts in hand

The boards are 11 mm apart because a standard PBS socket is 8.5 mm tall and a PLS header's
plastic body is 2.5 mm. Both vary between makers (PBS runs 7.0–8.5 mm). An 11 mm M3 standoff
exists but is uncommon: a 10 mm standoff plus a 1 mm washer does the same job.
**Before ordering, measure one PBS and one PLS from the batch you will buy, and set the
standoffs from that.** If they disagree with 11 mm, the strips either do not seat or they
bend the display board over its four standoffs.

The standoffs share that gap with the strips' plastic, and no courtyard check sees it: the
hole's footprint is on the front, the strip's on the back. The independent check found the
top-right standoff (display H4) with a hex spacer's corner 0.5 mm from XP12's end and a
7 mm washer 0.2 mm from it. **Fixed:** H4 moved 2 mm down on both boards, to display
(172.5, 7.5), now (187.9, 7.5) on the widened board. A 5.5 mm hex spacer clears the strip by 1.9 mm and a 7 mm washer by 1.6 mm.

### 2. Solder the strips while they are plugged together

Seven strip pairs carry 60 contacts across two boards. If each board's strips are
soldered on their own, a tenth of a millimetre of tilt on each makes the stack hard to mate
and puts the tube pins under load. The fix costs nothing and belongs in the assembly
instructions:

1. Fit all seven PLS strips into their PBS sockets.
2. Drop the sockets into TS06-DRV and the headers into TS06-DISP.
3. Screw the four standoffs in.
4. Solder both boards with the stack assembled.

The same order also sets the stack height from the real parts (finding 1).

### 3. Some solder joints show on the display's front face

The headers sit on TS06-DISP's back face, so their joints are on the front, among the
tubes. The bottom strips (XP21–XP25) are hidden if the fascia, or the case lip above it,
rises to world Y ≈ 38. **XP12 across the top and XP11 down the left edge are not hidden by anything but
the case.** The brow has to cover the top 4 mm of the display board, and the trench wall
the left 3 mm. The four standoff screws land on that face too. Three are in corners; only
H3, at the top of the colon column, is between tubes. Use black countersunk or low-head
screws.

### 4. 185 V is on the driver board's rear-facing side, and C7 stays charged

TS06-DRV's component face looks at the back of the case. It carries C7 (4.7 µF at 185 V,
about 0.08 J and 0.9 mC, above the usual touch-safe limits), the switch's TO-220 tab (the SW
node, up to about 190 V), the six optos, and every anode and ballast resistor. The bleeder
(R60 + R61, 940 kΩ) and the feedback divider (1.52 MΩ) take C7 down with a time constant of
about 2.7 s, so it is safe after about 15 s, not immediately.

**The rear of the case must be a closed panel held by screws.** Its vent slots should be
no wider than 2.5 mm, and it needs a high-voltage mark. The service note should read:
"unplug, wait 15 s".

### 5. Three chip orientations on one board (four in rev B)

On TS06-DRV, U15, U16, U17 and RN1 have pin 1 to the left. U3 and the six optos (U5–U10)
have it to the right. U2, U11 and U12 have it at the bottom. **Rev B stands U11 at 0°**, a
fourth orientation. It came from the recovered placement and is not on rev B's change list;
the owner decides whether to turn it back. Each orientation is what made the zero-via
routing possible, but at an assembly bench it is the most likely mistake: a DIP socket
soldered backwards is caught only when a chip is fitted, and a chip fitted backwards may
be destroyed.

**Mitigation:**

* Every socket's notch is on the silkscreen.
* The assembly sheet should list each socket's notch direction.
* Fit the sockets first and check them against the sheet before fitting any chip.

### 6. The tallest parts set the case's depth

| Part | Height above TS06-DRV | Can it lie down? |
|---|---|---|
| U13, DS3231 mini standing in a 5-way PBS | ≈ 21–22 mm | yes, with a right-angle header (≈ 12 mm) |
| VT21, IRF840 in TO-220, vertical | ≈ 19 mm | only if the board beside it is kept clear: the tab is the 185 V switch node and would need an insulating pad |
| C7, 4.7 µF 400 V, Ø10 radial | ≈ 16–20 mm | yes: lay it on its side (≈ 11 mm) |
| U1, Nano on PBS-15 sockets | ≈ 16.6 mm | no, it stays removable |
| L1, radial 220 µH | ≈ 16 mm (its footprint's height) | no |

The case model measures each part against the rear panel: U13 has 5.0 mm, C7 7.0, VT21
8.0, the Nano 10.4 and L1 11.0. U13 sets the depth. Laying down U13, C7 and VT21 makes the
case 78.2 mm deep instead of 83.6. After that, the Nano and L1 set it.

**Rev B:** U13 sits on a male PLS-5 (15 mm) and L1 is the axial Bourns part, lying (12 mm). The
case model reads their heights from the footprints: C7 now sets the depth with 5.0 mm, then
VT21 6.0, the Nano 8.4, U13 10.0 and L1 13.0. The case is **81.6 mm deep**. Laying down U13, C7
and VT21 still gives 78.2.
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
