BobStolb/TERMINAL-06-firmware/3d/case-pair/out/exploded.png

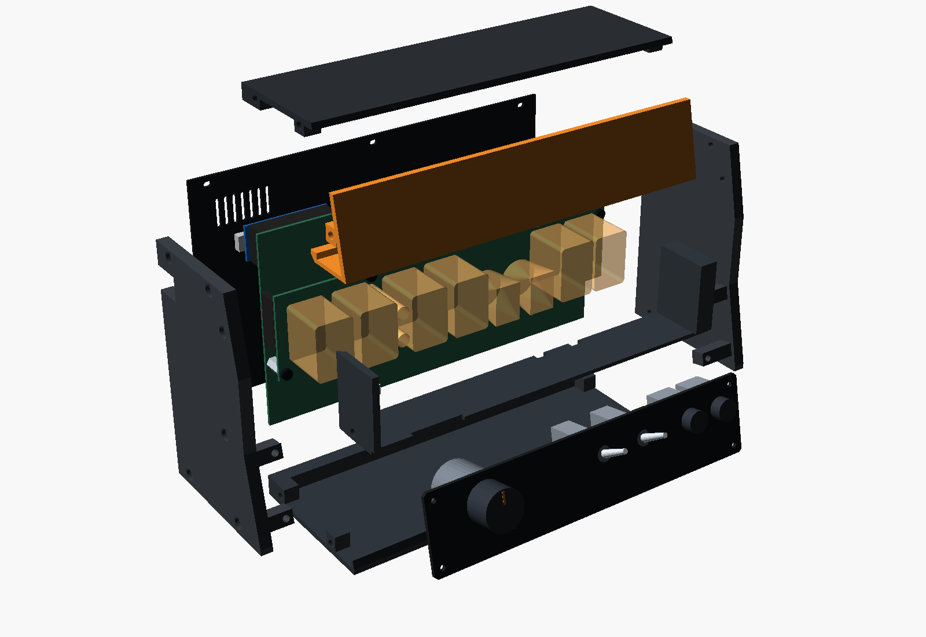
3d/case-pair/out/exploded.png
