BobStolb/TERMINAL-06-firmware/3d/case-pair/out/front.png

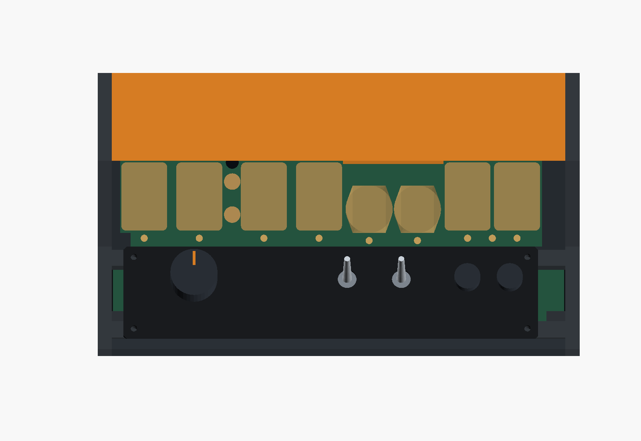
3d/case-pair/out/front.png
