BobStolb/TERMINAL-06-firmware/3d/case-pair/out/iso_rear.png

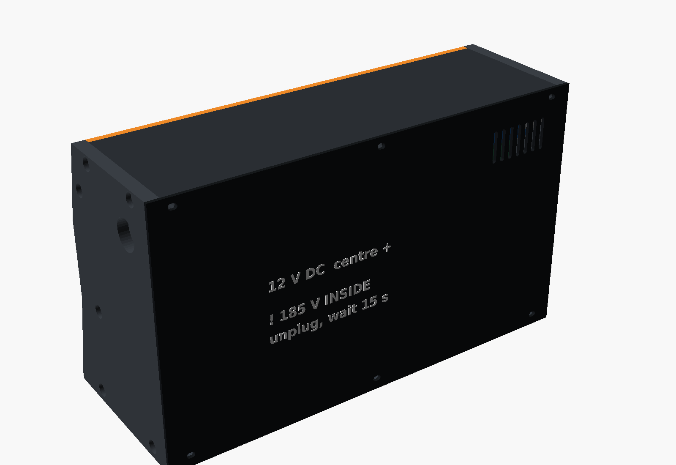
3d/case-pair/out/iso_rear.png
