BobStolb/TERMINAL-06-firmware/3d/case-pair/out/module.png

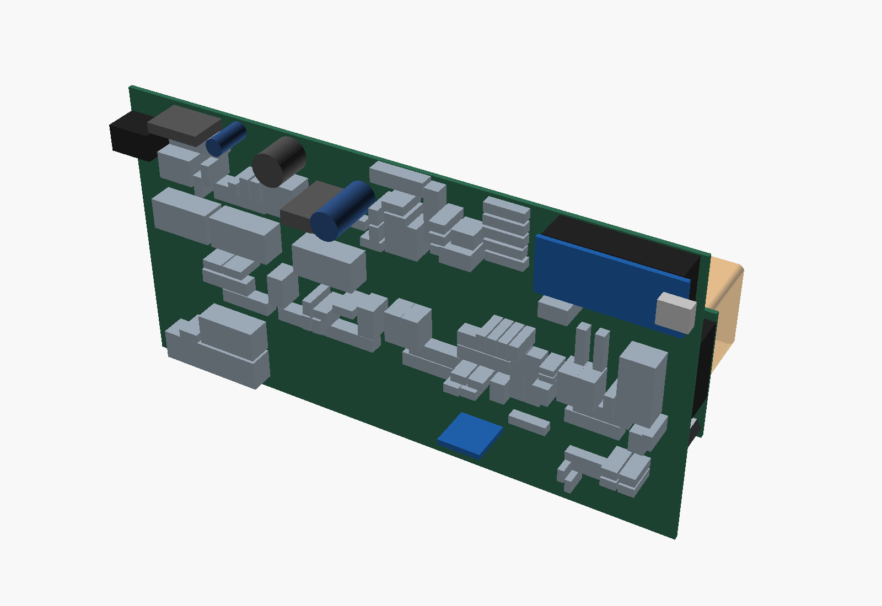
3d/case-pair/out/module.png
