BobStolb/TERMINAL-06-firmware/3d/case-pair/power-options/cheek-cutouts-section.png

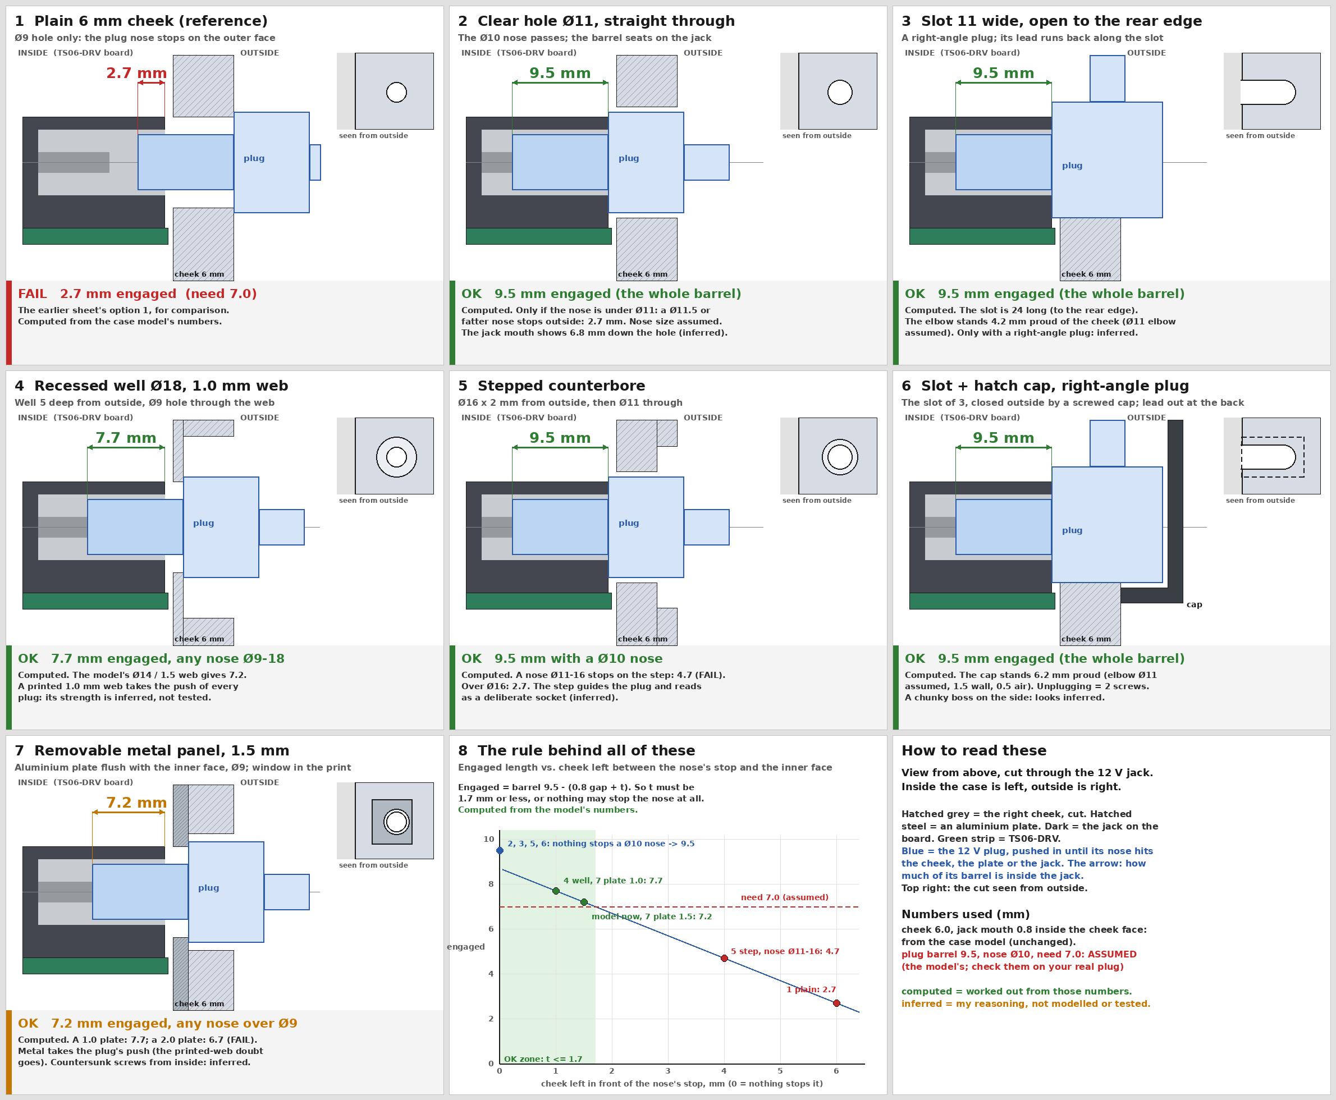
3d/case-pair/power-options/cheek-cutouts-section.png
