BobStolb/TERMINAL-06-firmware/3d/case-pair/power-options/drv-jack-corner.png

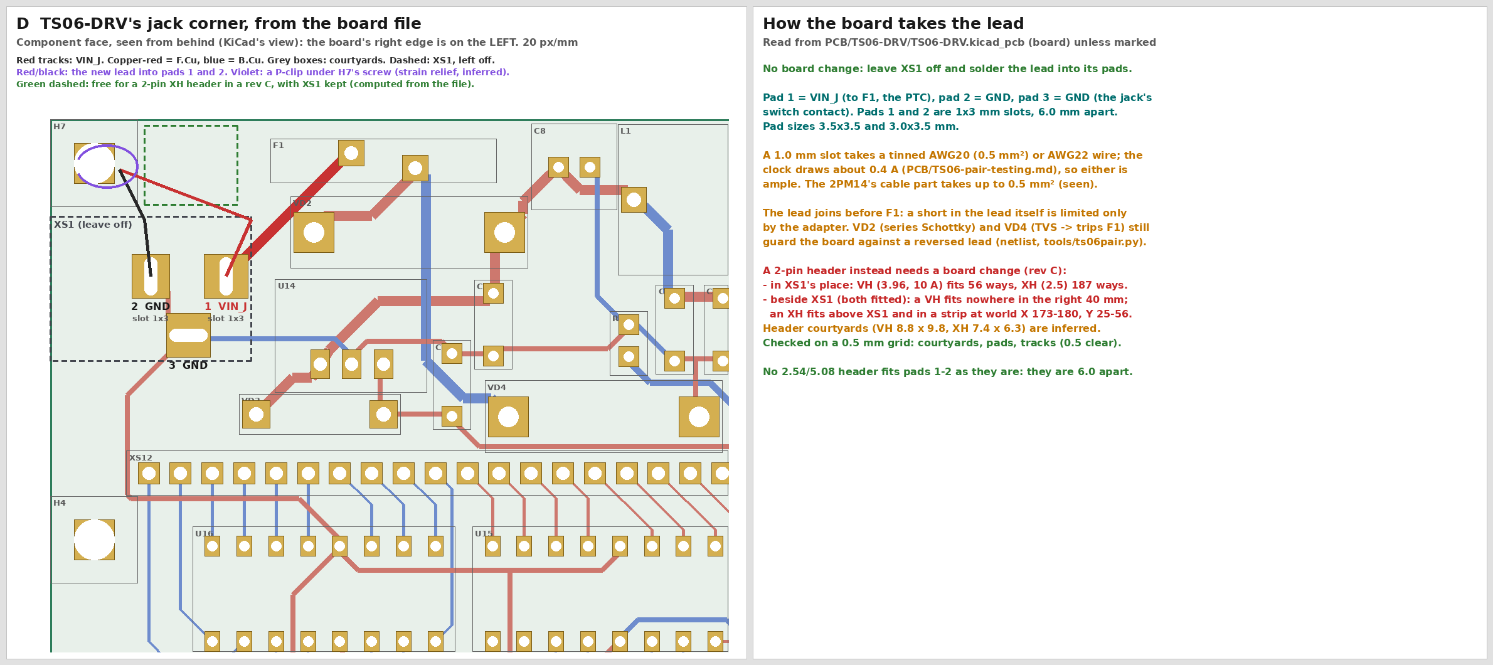
3d/case-pair/power-options/drv-jack-corner.png
