BobStolb/TERMINAL-06-firmware/3d/case-pair/power-options/move-port-rear.png

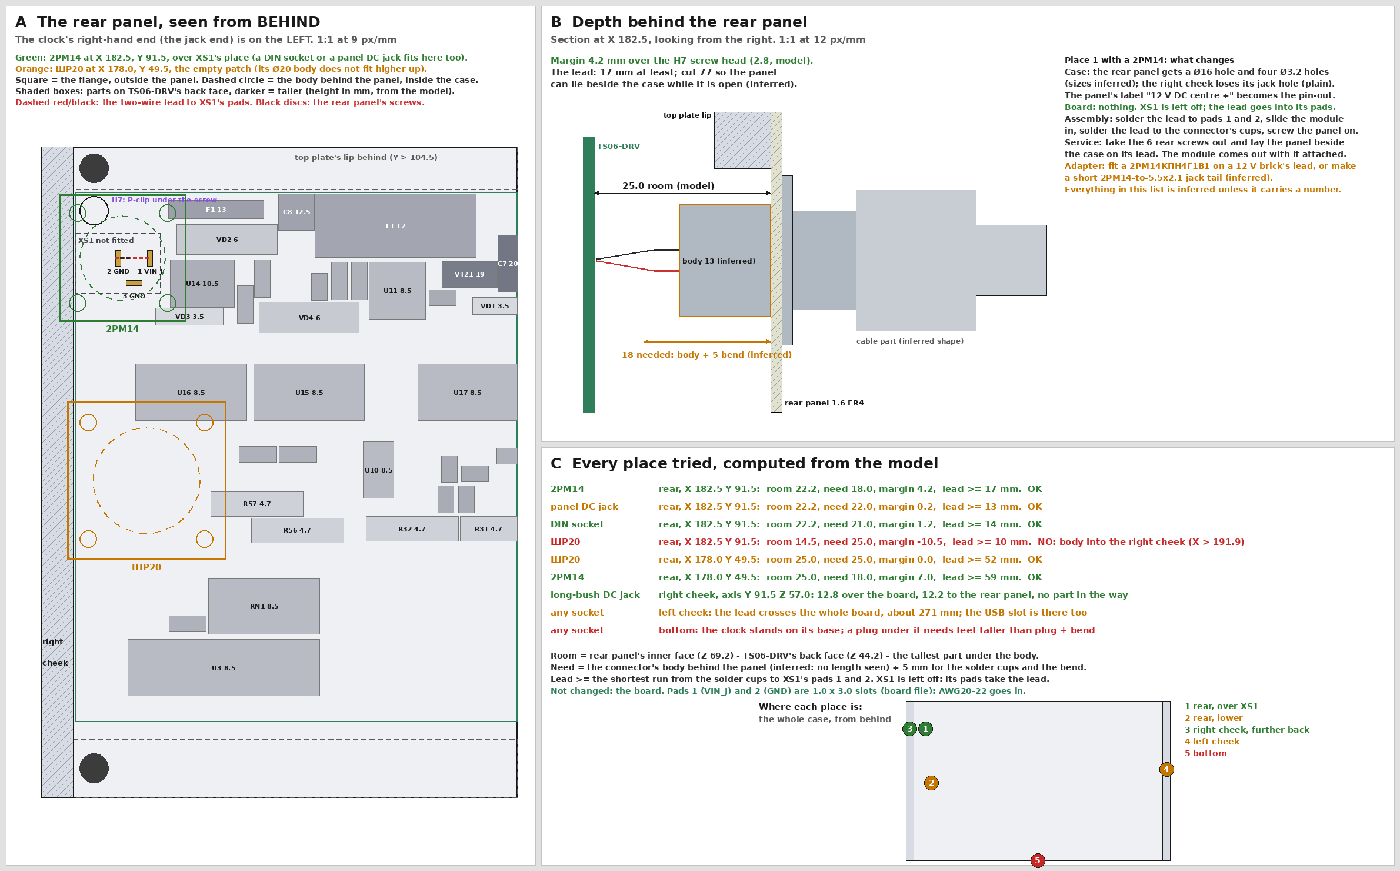
3d/case-pair/power-options/move-port-rear.png
