BobStolb/TERMINAL-06-firmware/3d/case-pair/power-options/render-2rm14-rear.png

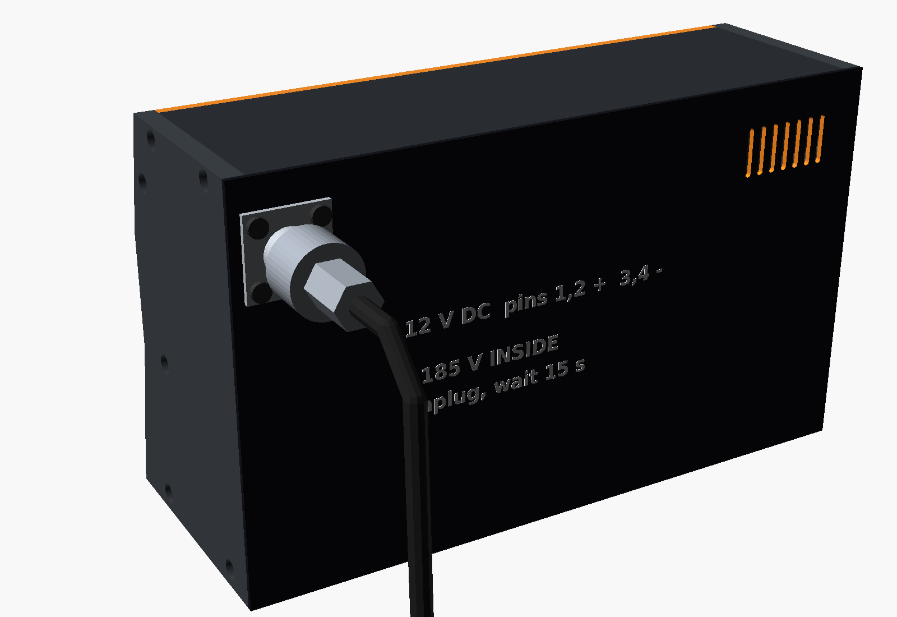
3d/case-pair/power-options/render-2rm14-rear.png
