BobStolb/TERMINAL-06-firmware/3d/case-pair/power-options/render-cheek-jack.png

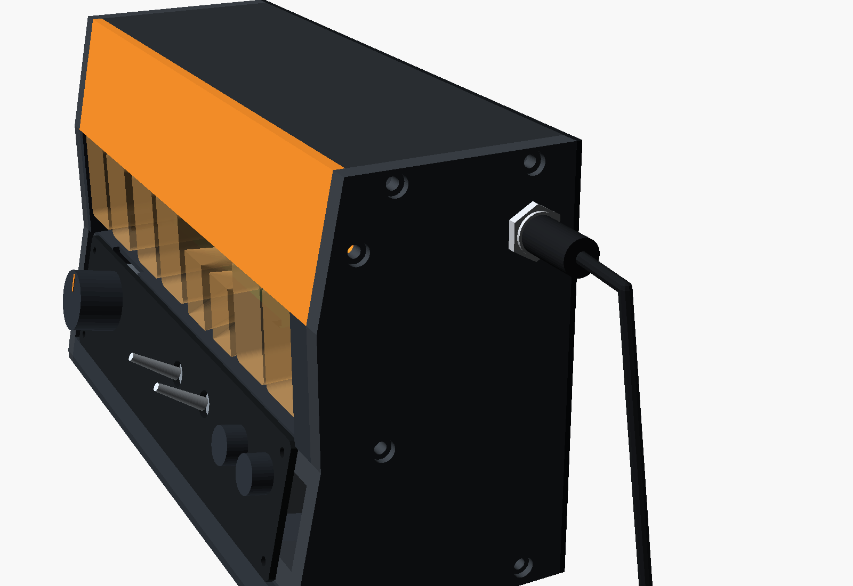
3d/case-pair/power-options/render-cheek-jack.png
