BobStolb/TERMINAL-06-firmware/3d/case-pair/power-options/soviet-connectors.png

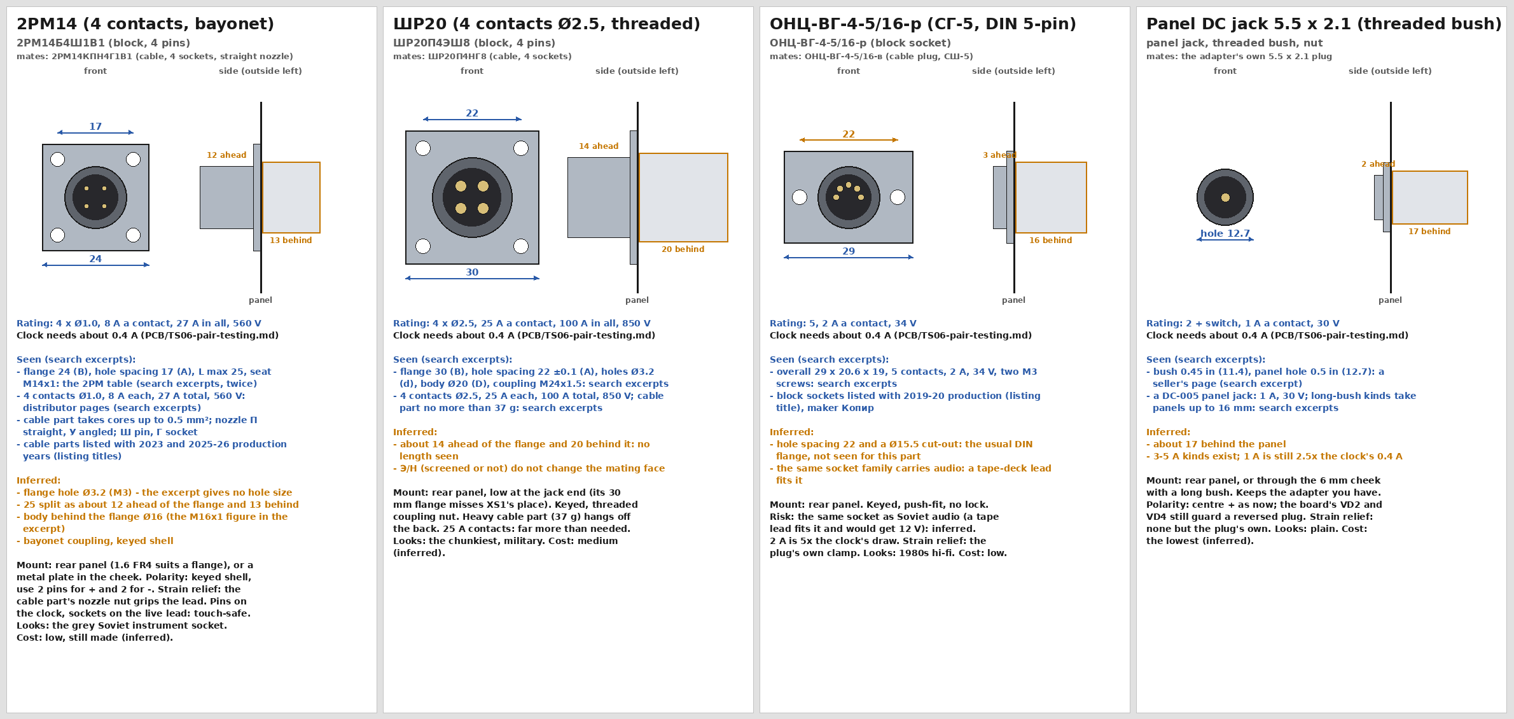
3d/case-pair/power-options/soviet-connectors.png
