BobStolb/TERMINAL-06-firmware/3d/case-pair/variant-D/slot_right_frame.png

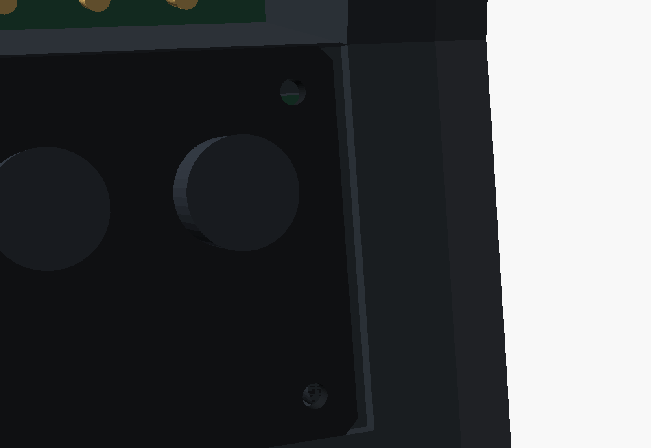
3d/case-pair/variant-D/slot_right_frame.png
