BobStolb/TERMINAL-06-firmware/3d/case-pair/variant-D/slot_right_noframe.png

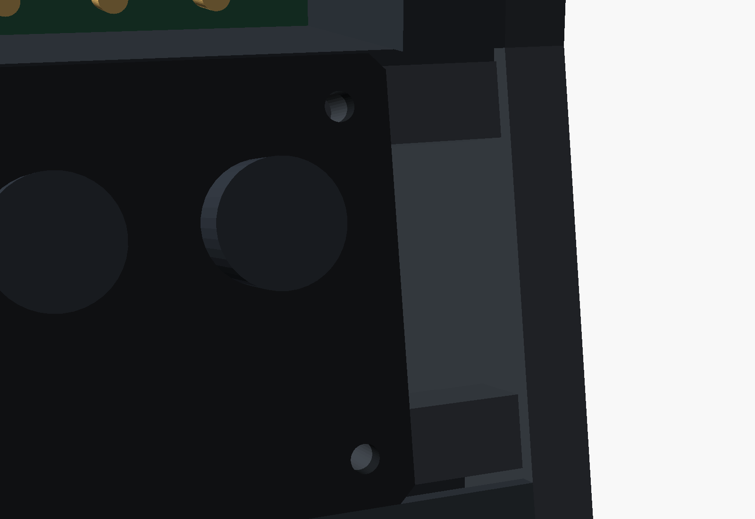
3d/case-pair/variant-D/slot_right_noframe.png
