BobStolb/TERMINAL-06-firmware/3d/knob/face_A-six-positions.png

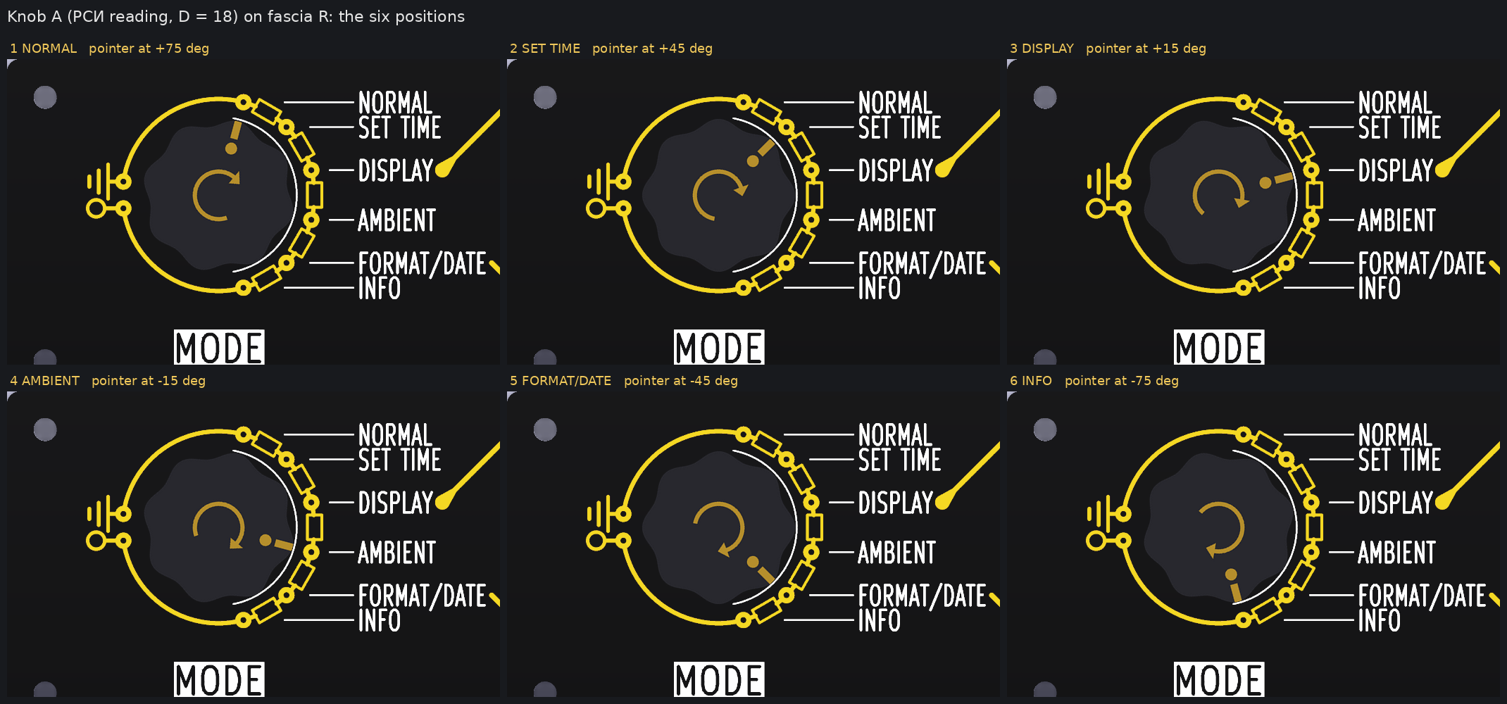
3d/knob/face_A-six-positions.png
