BobStolb/TERMINAL-06-firmware/3d/populated/before/TS06-DRV-iso.png

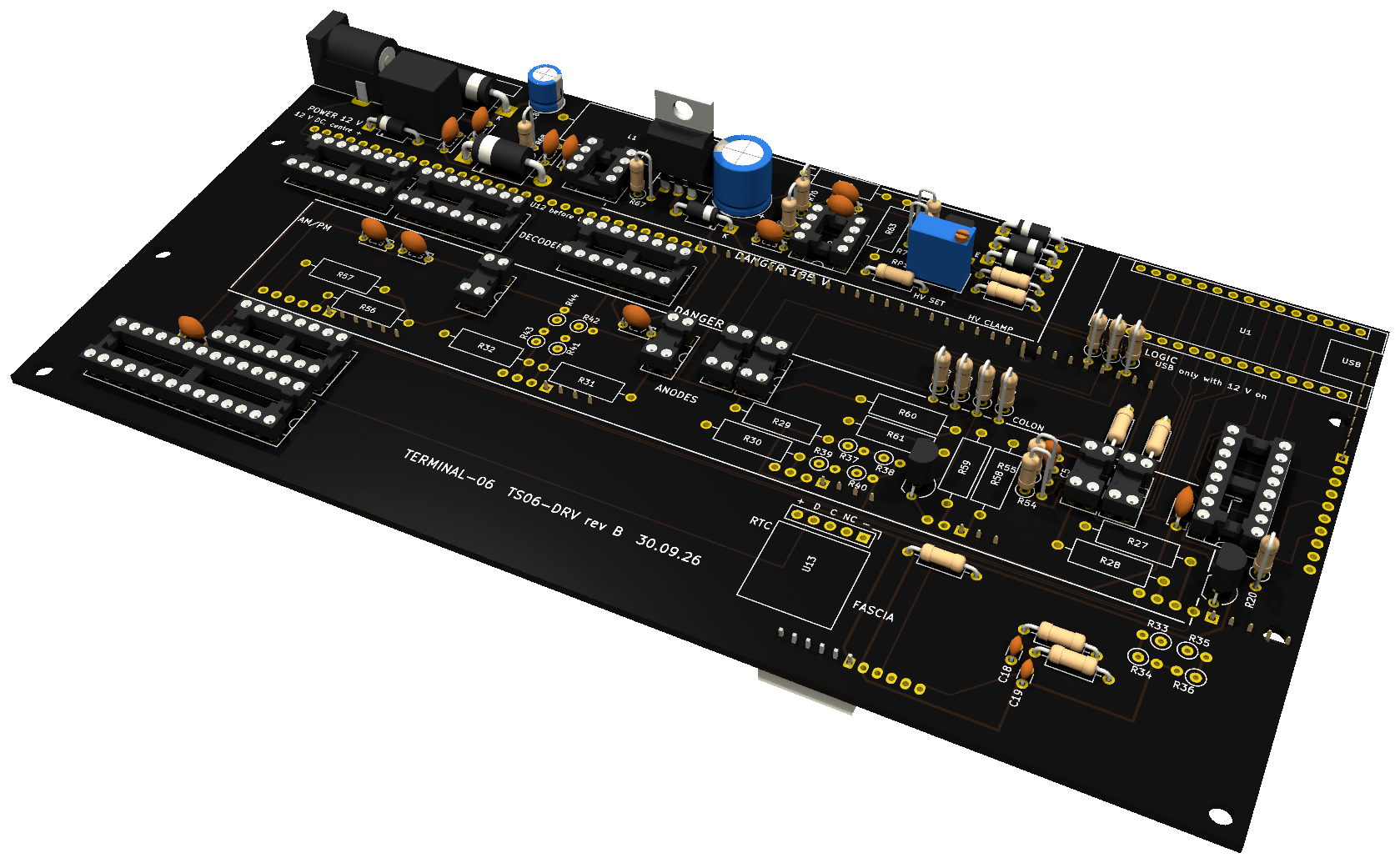
3d/populated/before/TS06-DRV-iso.png
