BobStolb/TERMINAL-06-firmware/3d/populated/before/TS06-FASCIA-rhythm-iso.png

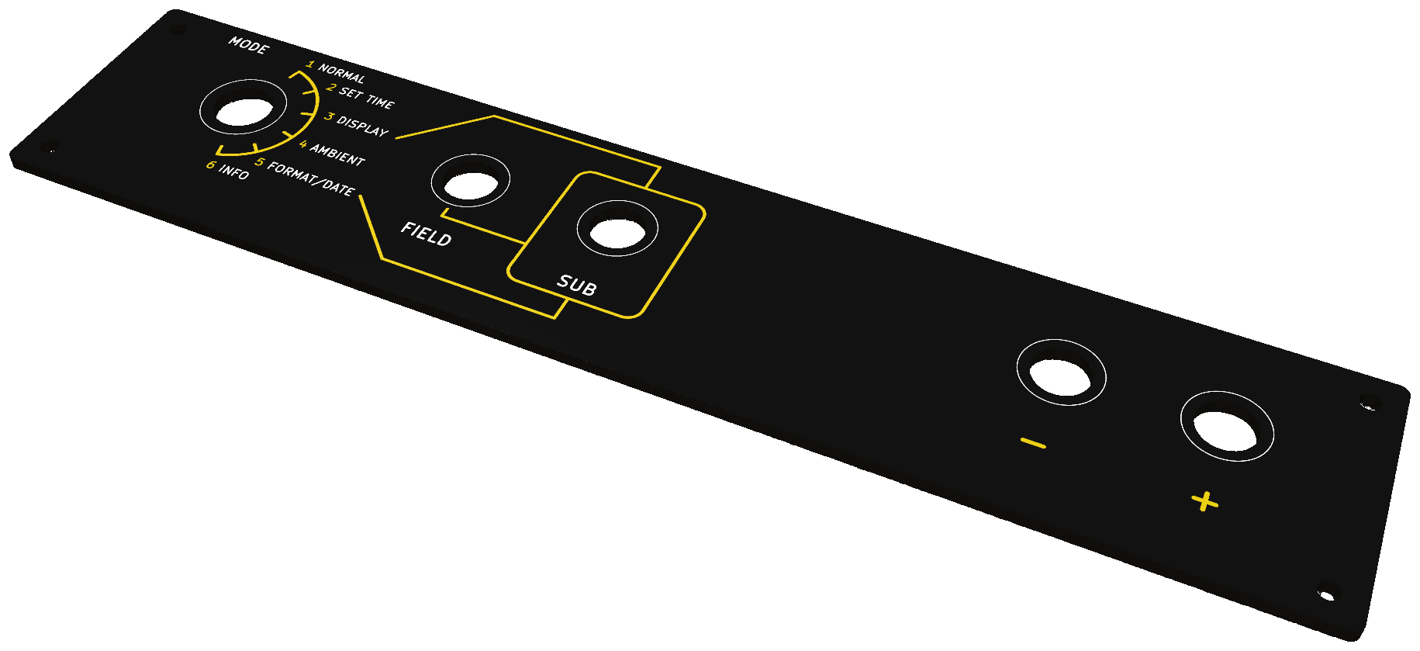
3d/populated/before/TS06-FASCIA-rhythm-iso.png
