BobStolb/TERMINAL-06-firmware/3d/populated/TS06-DISP-iso.png

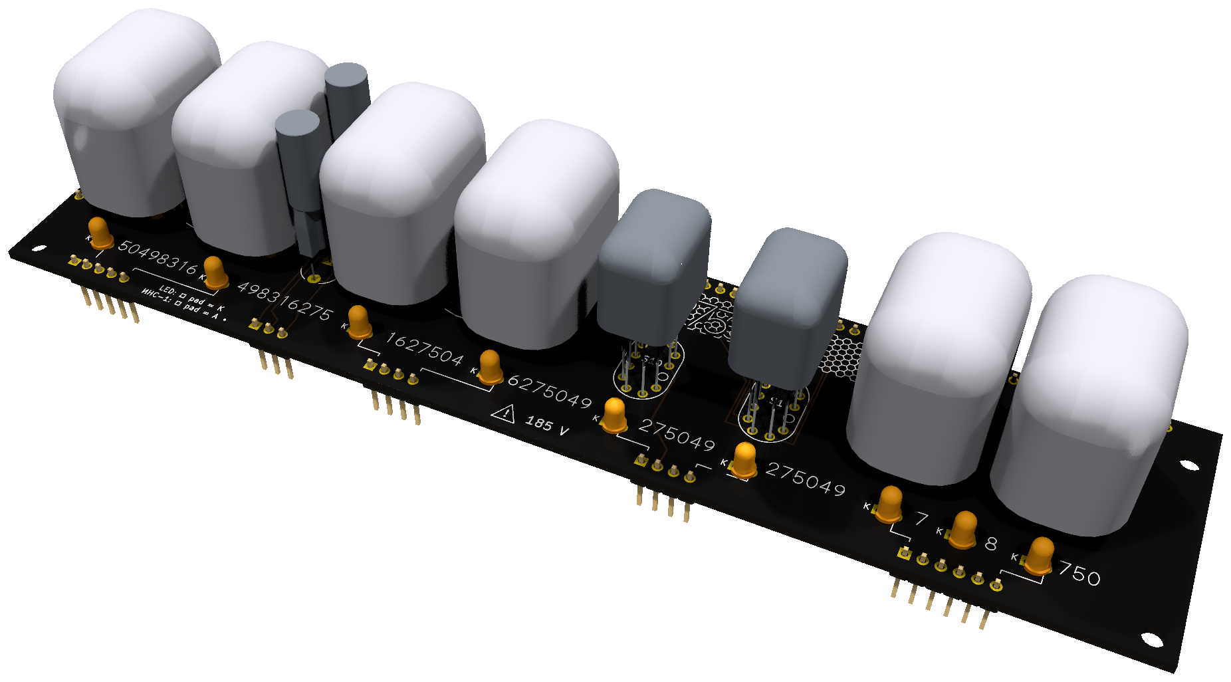
3d/populated/TS06-DISP-iso.png
