BobStolb/TERMINAL-06-firmware/3d/populated/TS06-DISP-top.png

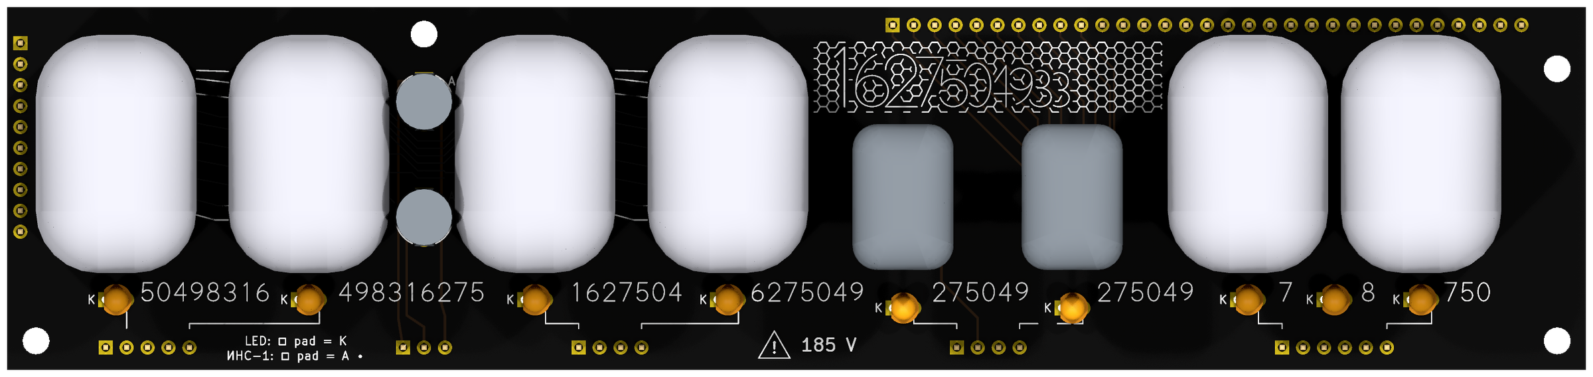
3d/populated/TS06-DISP-top.png
