BobStolb/TERMINAL-06-firmware/3d/populated/TS06-DRV-top.png

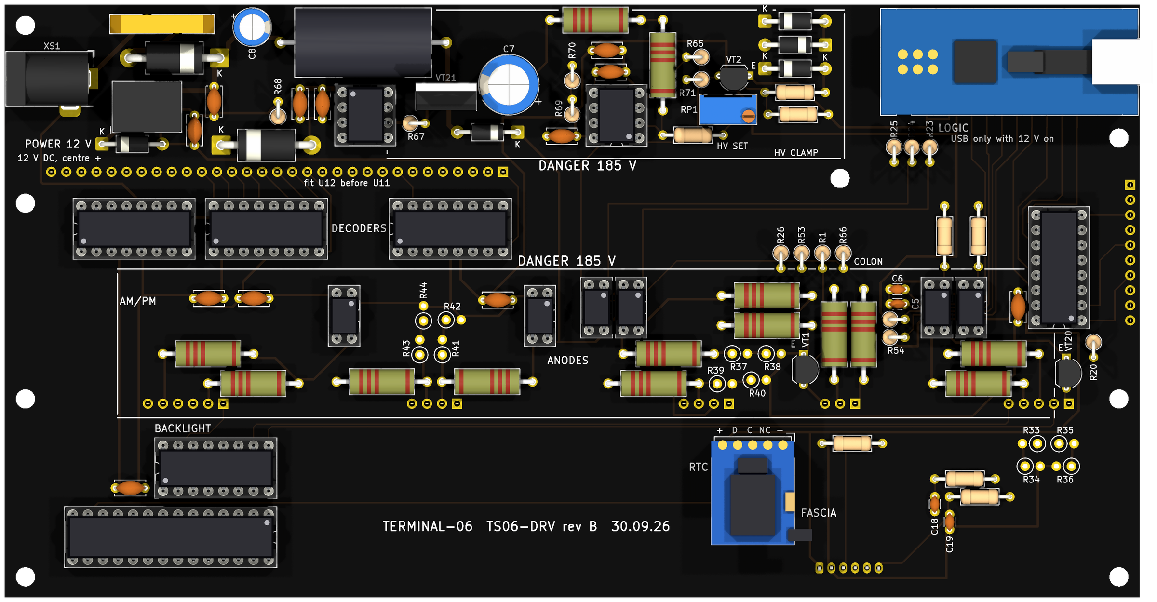
3d/populated/TS06-DRV-top.png
