BobStolb/TERMINAL-06-firmware/3d/populated/TS06-FASCIA-rhythm-top.png

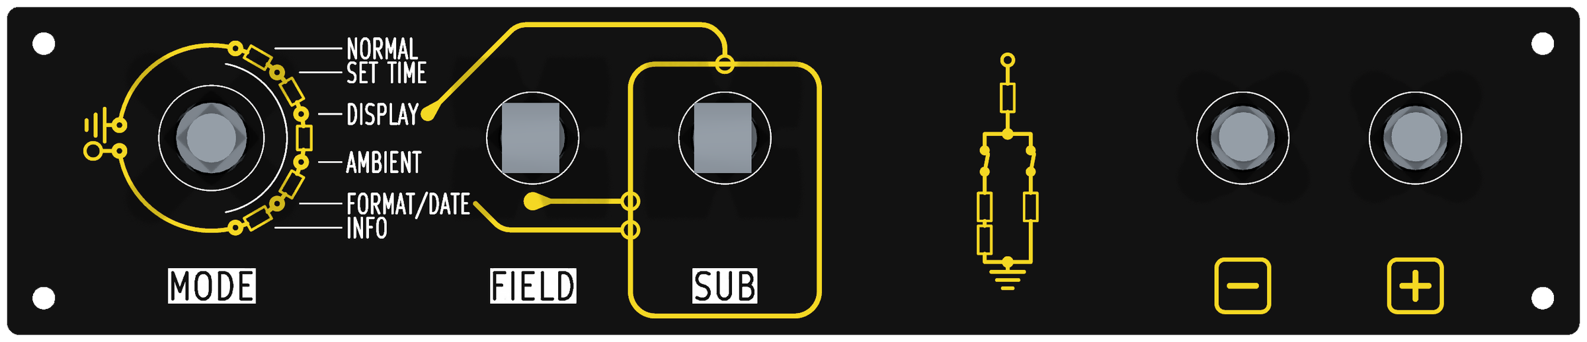
3d/populated/TS06-FASCIA-rhythm-top.png
