BobStolb/TERMINAL-06-firmware/3d/populated/TS06-stack-front.png

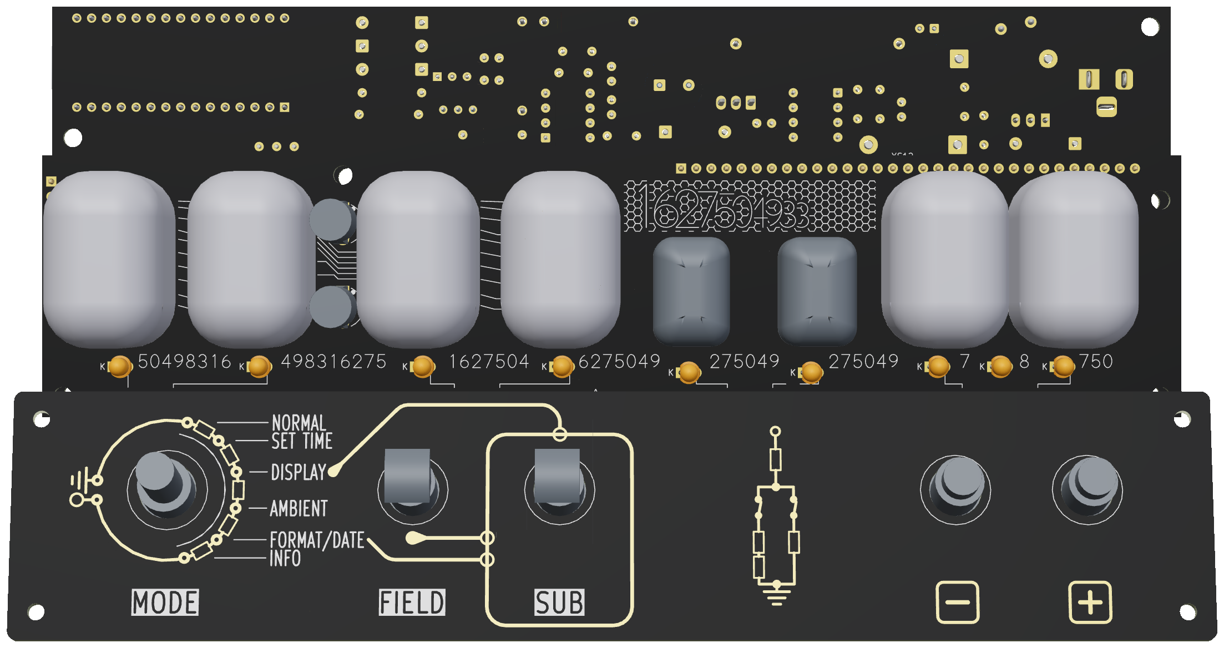
3d/populated/TS06-stack-front.png
