BobStolb/TERMINAL-06-firmware/Claude outputs/b-sill-34.png

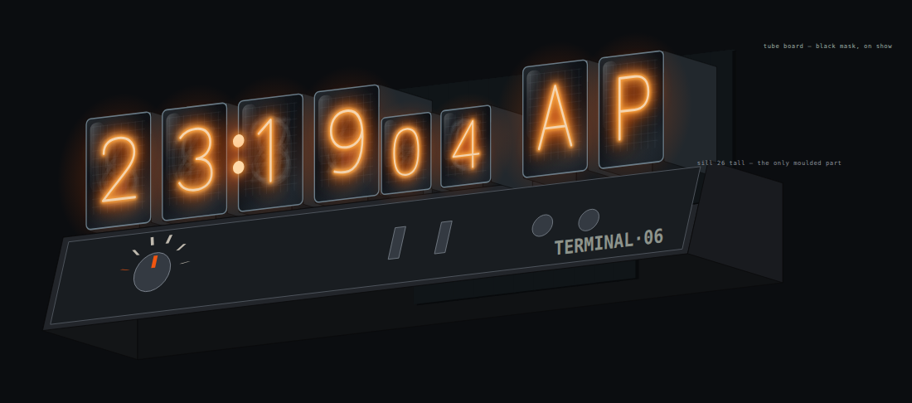
Claude outputs/b-sill-34.png
