BobStolb/TERMINAL-06-firmware/Claude outputs/b-sill-front.png

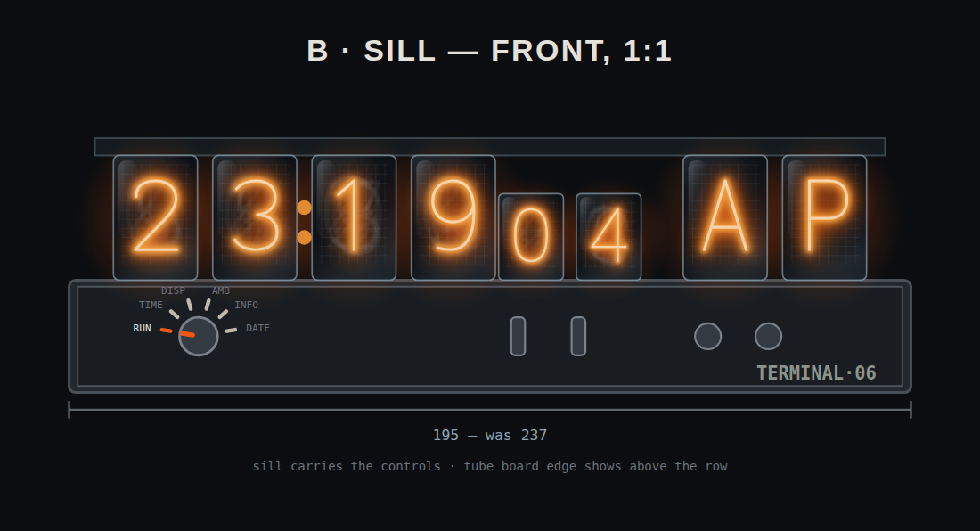
Claude outputs/b-sill-front.png
