BobStolb/TERMINAL-06-firmware/Claude outputs/c-cheek-34.png

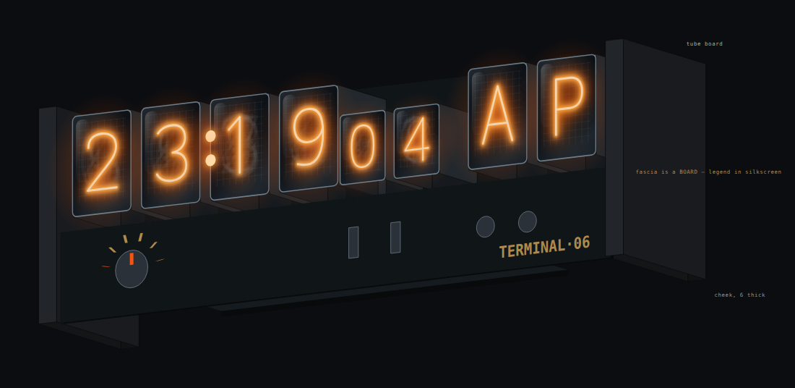
Claude outputs/c-cheek-34.png
