BobStolb/TERMINAL-06-firmware/Claude outputs/c-cheek-front.png

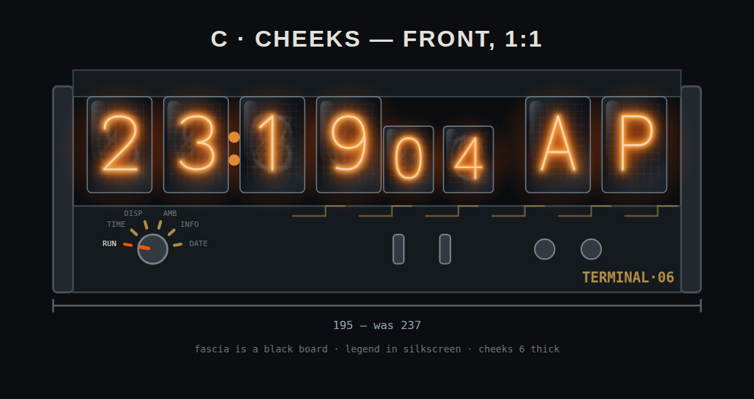
Claude outputs/c-cheek-front.png
