BobStolb/TERMINAL-06-firmware/Claude outputs/f-cheek.png

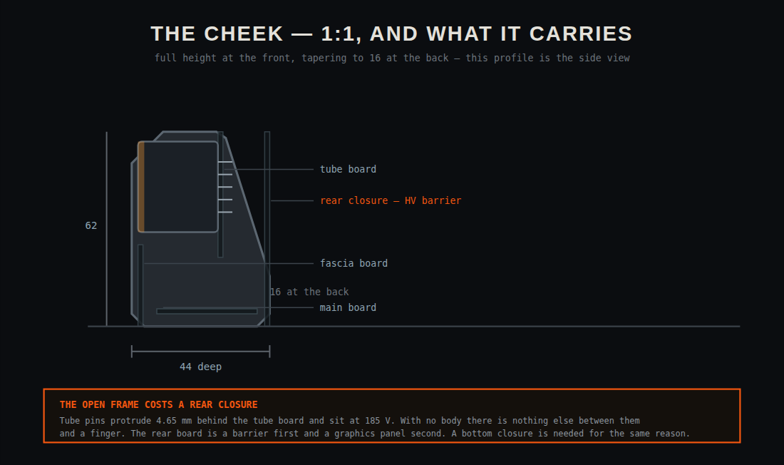
Claude outputs/f-cheek.png
