BobStolb/TERMINAL-06-firmware/Claude outputs/f-exploded.png

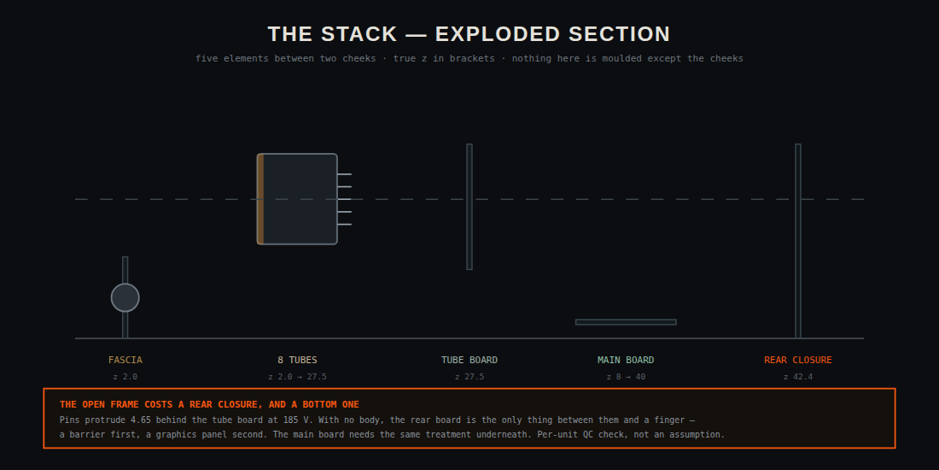
Claude outputs/f-exploded.png
