BobStolb/TERMINAL-06-firmware/Claude outputs/f-hero.png

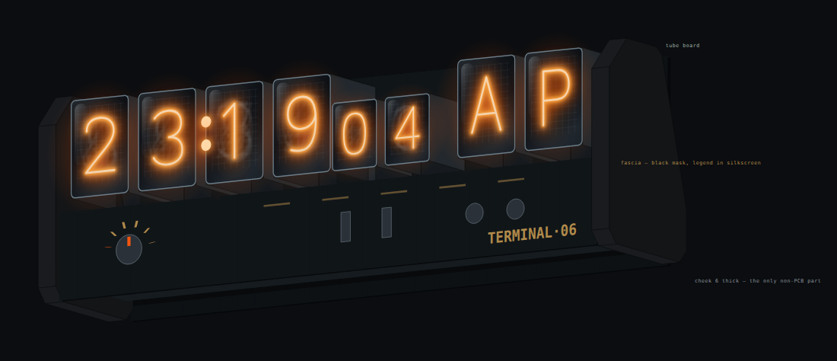
Claude outputs/f-hero.png
