BobStolb/TERMINAL-06-firmware/Claude outputs/m-massing.png

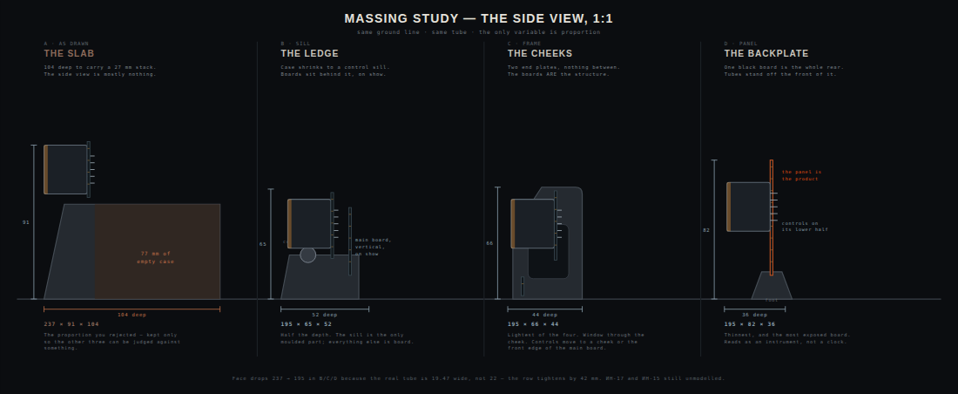
Claude outputs/m-massing.png
