BobStolb/TERMINAL-06-firmware/Claude outputs/n-mimi-night.png

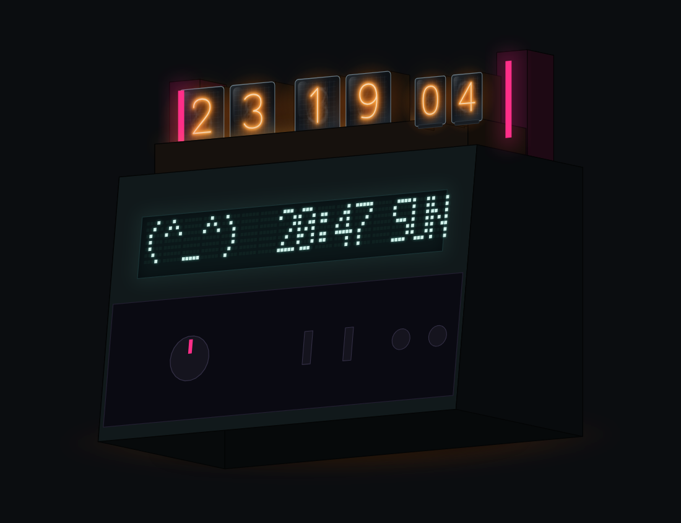
Claude outputs/n-mimi-night.png
