BobStolb/TERMINAL-06-firmware/Claude outputs/n-quadrant-night.png

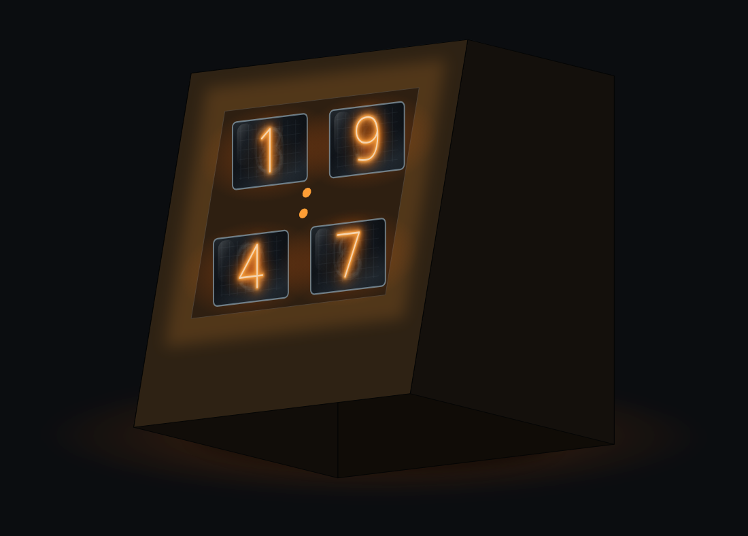
Claude outputs/n-quadrant-night.png
