BobStolb/TERMINAL-06-firmware/Claude outputs/n-scaler-night.png

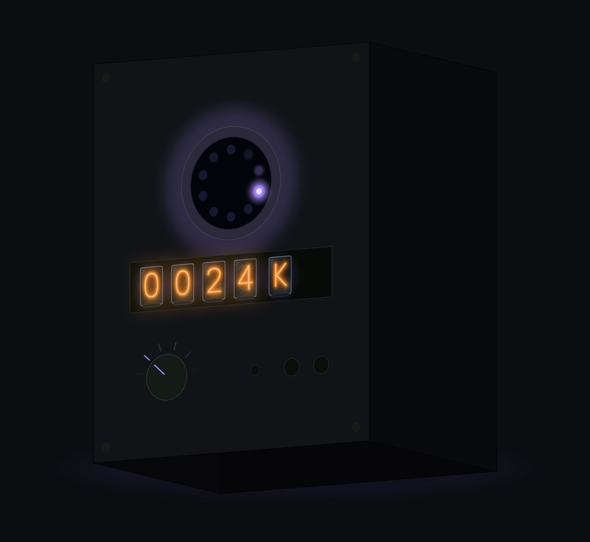
Claude outputs/n-scaler-night.png
