BobStolb/TERMINAL-06-firmware/Claude outputs/n-terminal-exploded.png

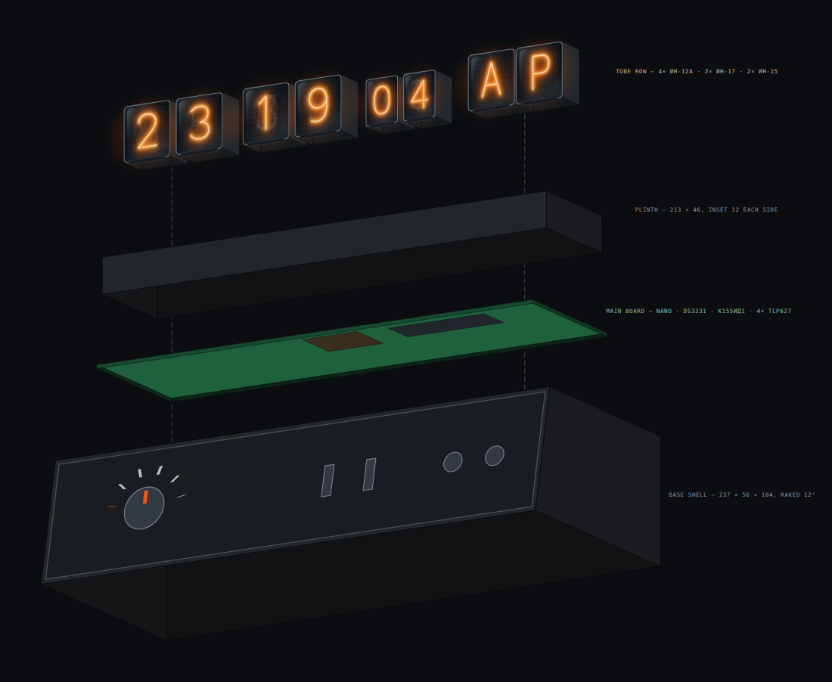
Claude outputs/n-terminal-exploded.png
