BobStolb/TERMINAL-06-firmware/Claude outputs/n-terminal-fascia.png

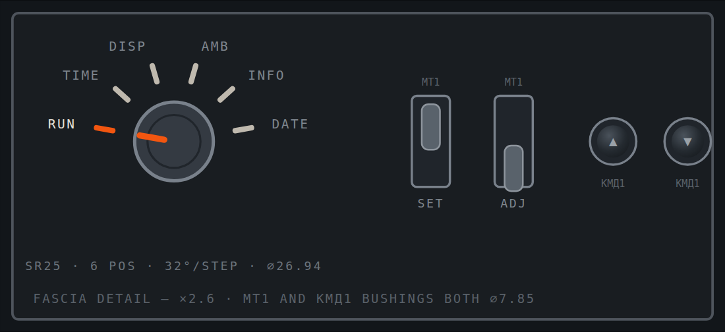
Claude outputs/n-terminal-fascia.png
