BobStolb/TERMINAL-06-firmware/Claude outputs/n-terminal-left.png

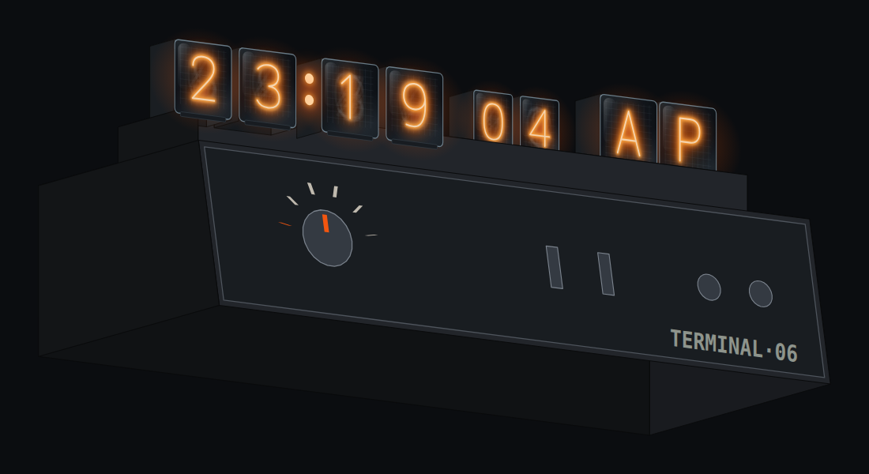
Claude outputs/n-terminal-left.png
