BobStolb/TERMINAL-06-firmware/Claude outputs/n-terminal-night.png

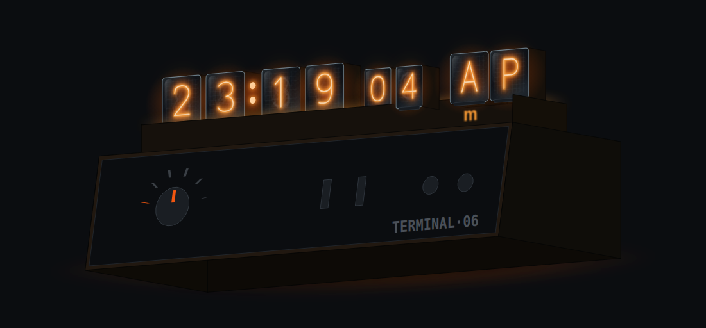
Claude outputs/n-terminal-night.png
