BobStolb/TERMINAL-06-firmware/Claude outputs/n-terminal-plan.png

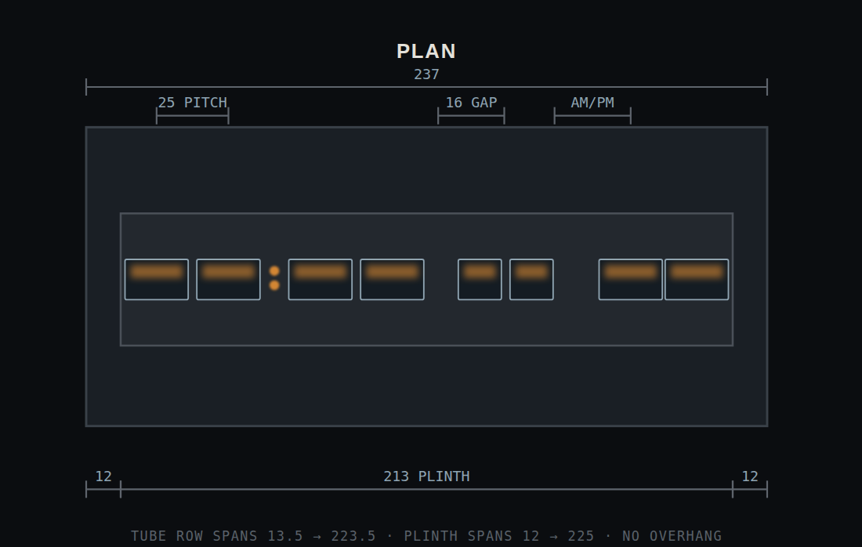
Claude outputs/n-terminal-plan.png
