BobStolb/TERMINAL-06-firmware/Claude outputs/n-terminal-profile.png

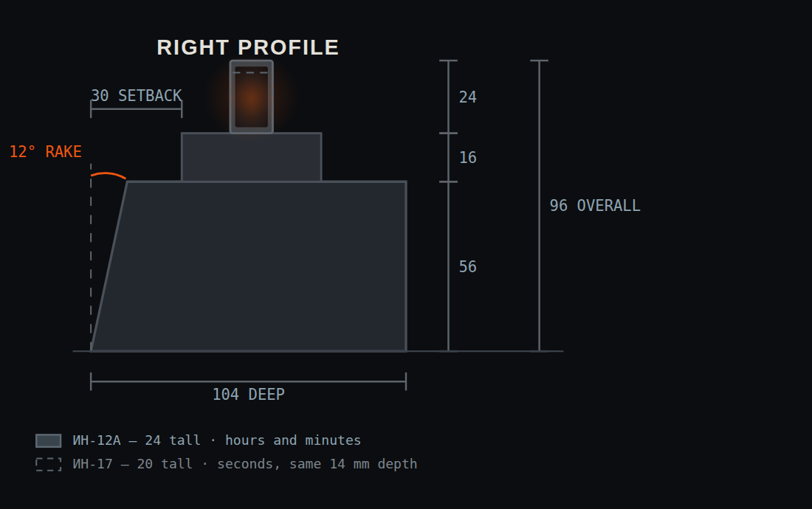
Claude outputs/n-terminal-profile.png
