BobStolb/TERMINAL-06-firmware/Claude outputs/n-terminal-rear34.png

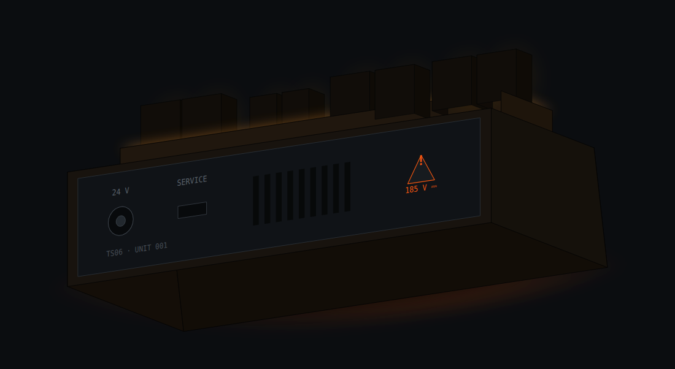
Claude outputs/n-terminal-rear34.png
