BobStolb/TERMINAL-06-firmware/Claude outputs/n-terminal-scale.png

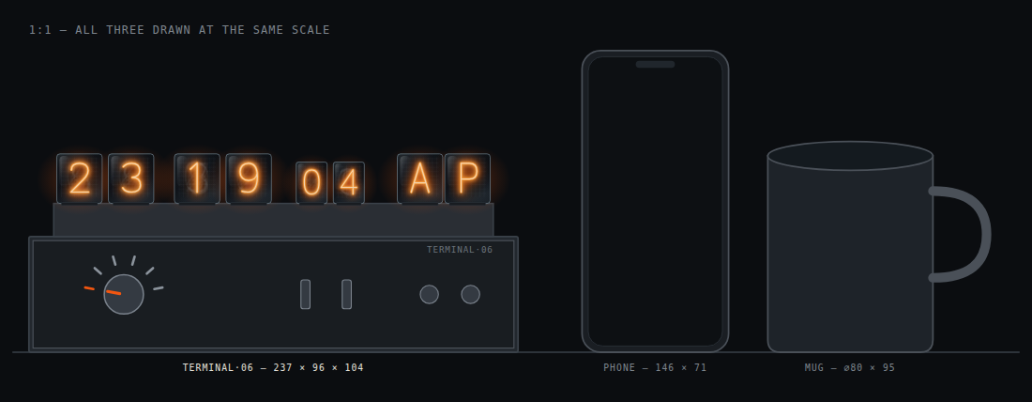
Claude outputs/n-terminal-scale.png
