BobStolb/TERMINAL-06-firmware/Claude outputs/r-in12-mounting.png

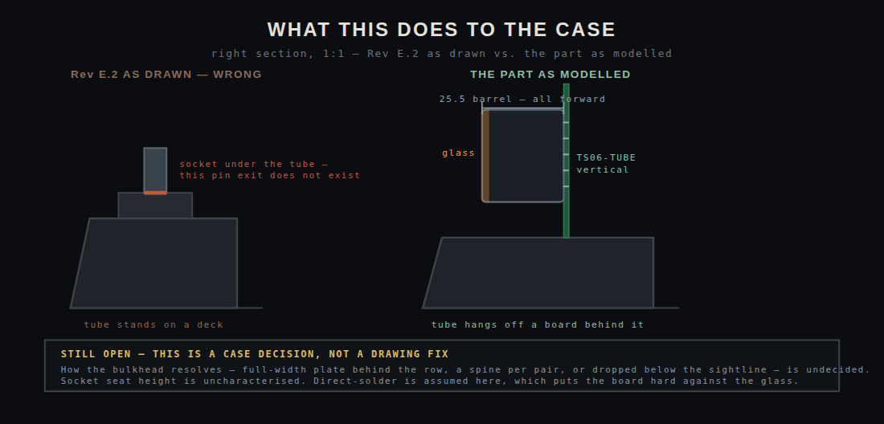
Claude outputs/r-in12-mounting.png
