BobStolb/TERMINAL-06-firmware/Claude outputs/routing-baseline/TS06-MAIN-vc1500.png

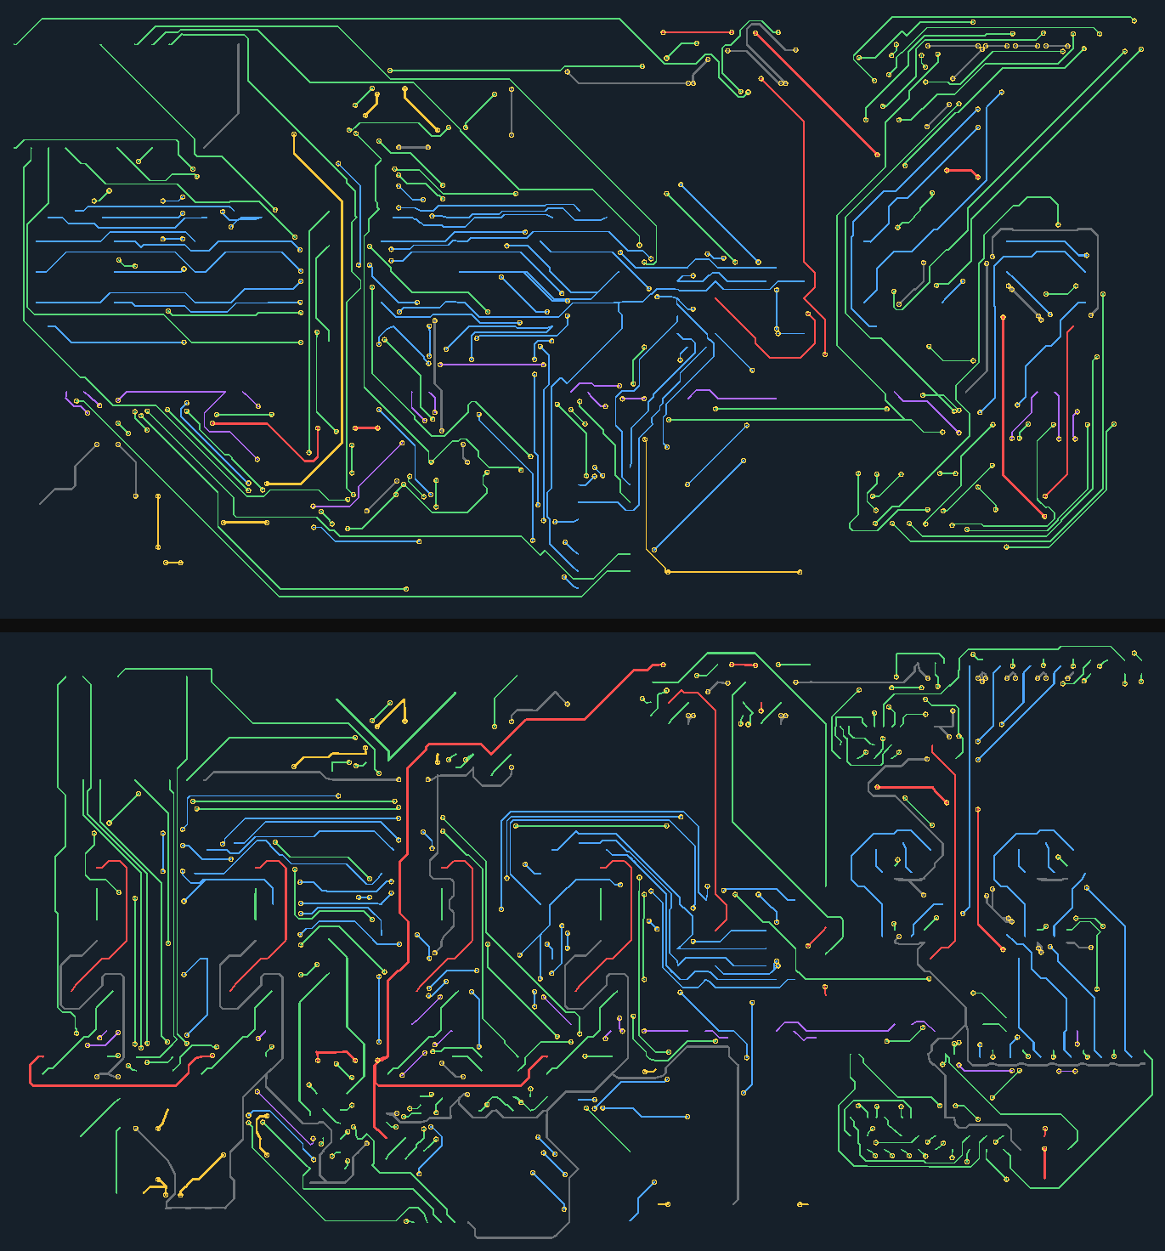
Claude outputs/routing-baseline/TS06-MAIN-vc1500.png
