BobStolb/TERMINAL-06-firmware/Claude outputs/v-rail.png

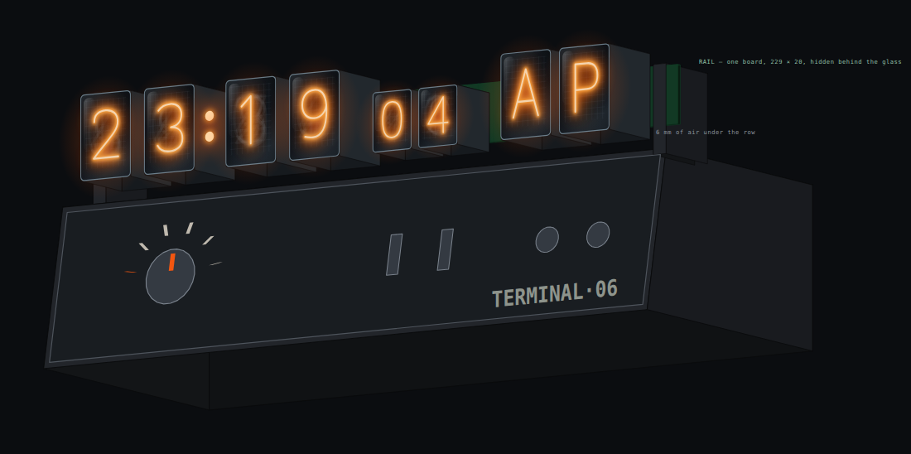
Claude outputs/v-rail.png
