BobStolb/TERMINAL-06-firmware/Claude outputs/v-section.png

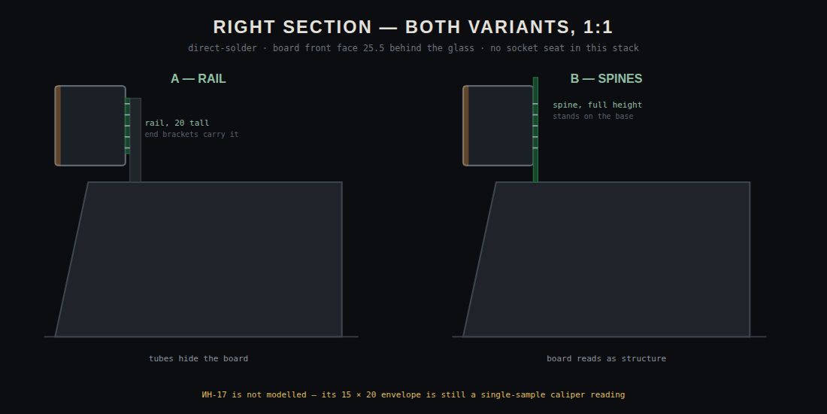
Claude outputs/v-section.png
