BobStolb/TERMINAL-06-firmware/Claude outputs/v-spines.png

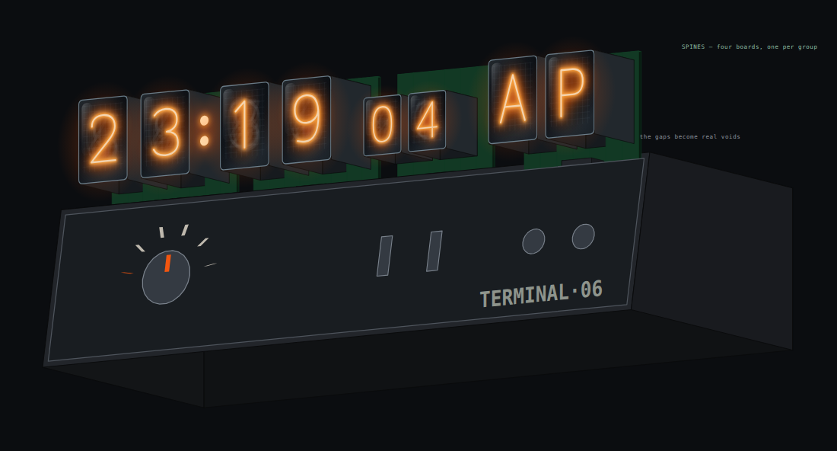
Claude outputs/v-spines.png
