BobStolb/TERMINAL-06-firmware/fab/preview/fascia-R-divider-top.png

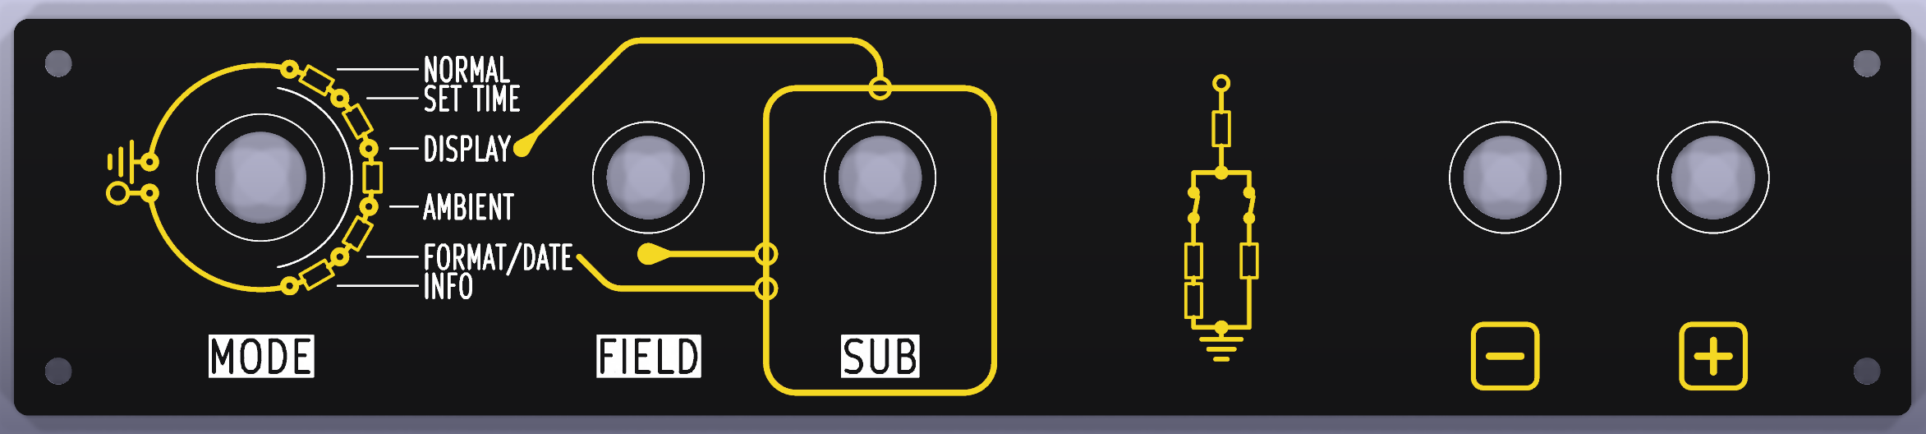
fab/preview/fascia-R-divider-top.png
