BobStolb/TERMINAL-06-firmware/fab/preview/three-boards-top.png

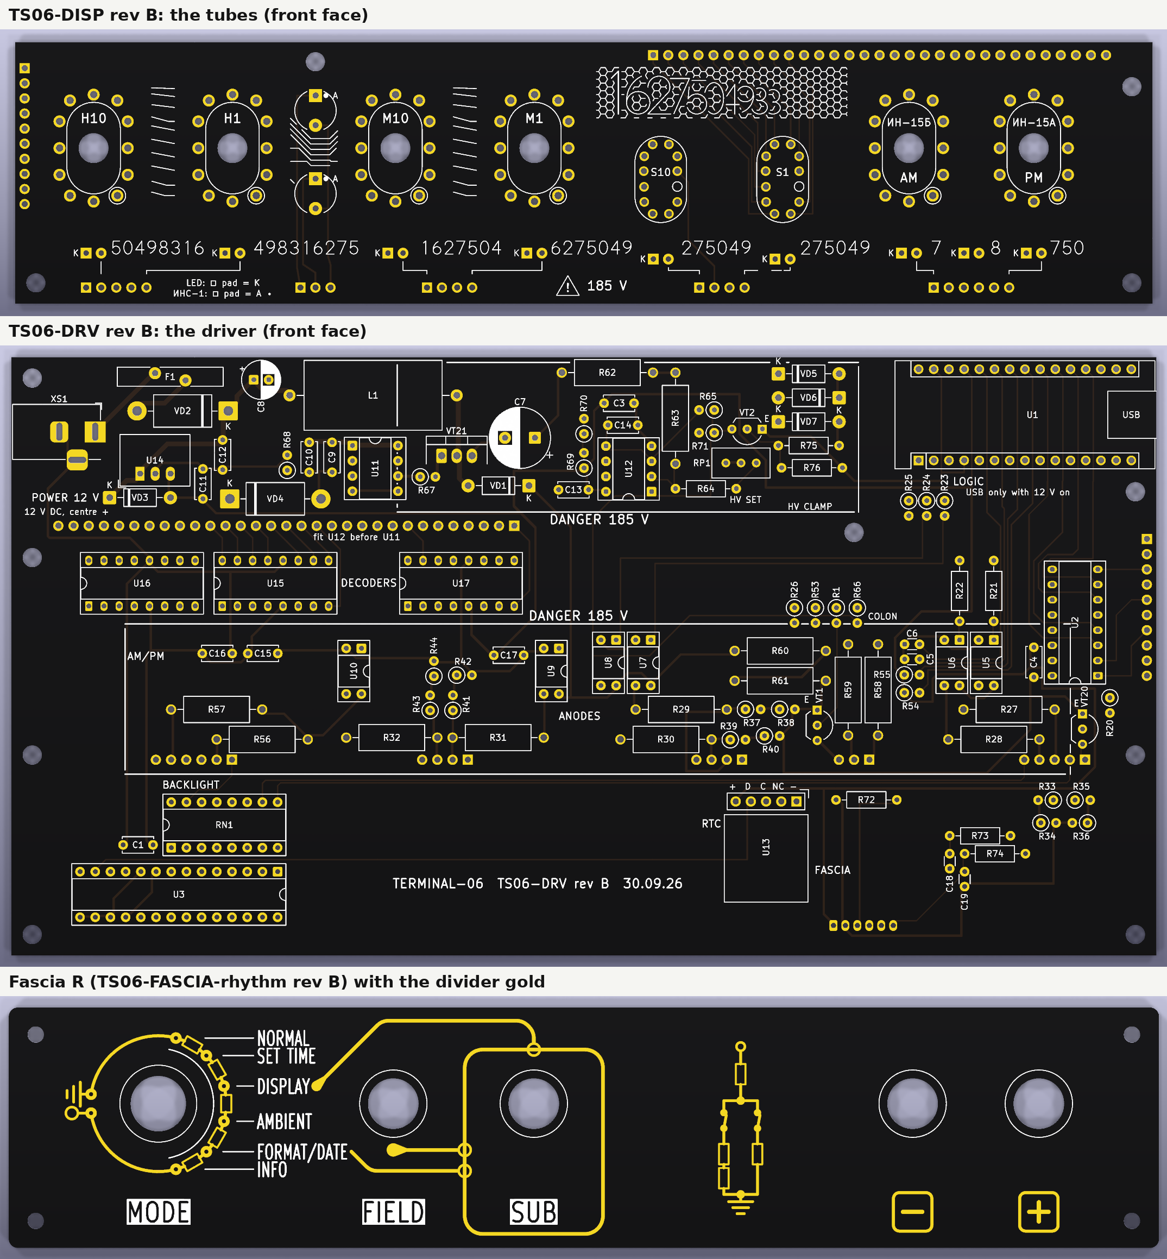
fab/preview/three-boards-top.png
