BobStolb/TERMINAL-06-firmware/knowledge/preview (1).webp

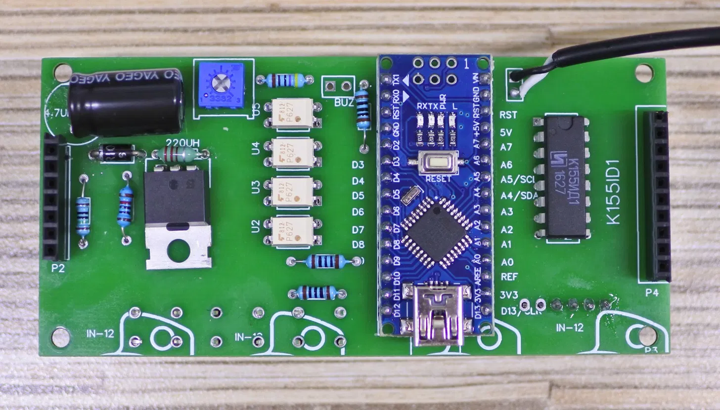
knowledge/preview (1).webp
