BobStolb/TERMINAL-06-firmware/knowledge/preview (2).webp

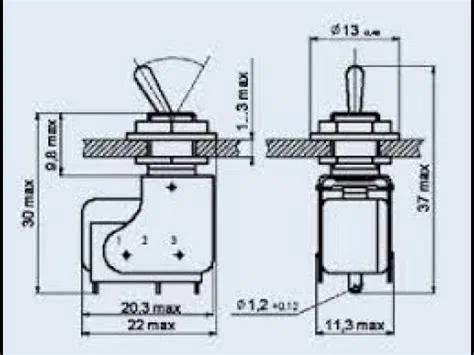
knowledge/preview (2).webp
