BobStolb/TERMINAL-06-firmware/knowledge/preview.webp

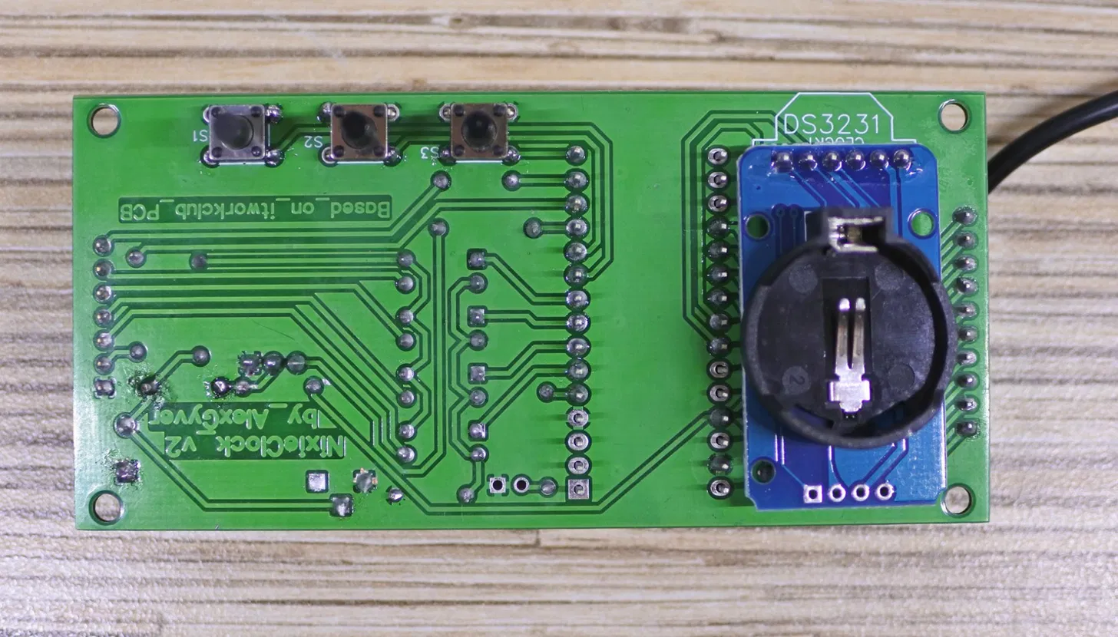
knowledge/preview.webp
