BobStolb/TERMINAL-06-firmware/knowledge/r-in12-reference.png

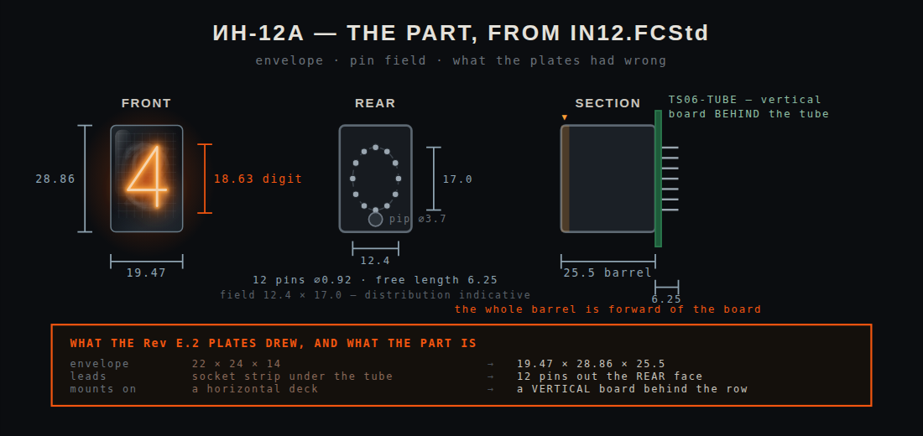
knowledge/r-in12-reference.png
