BobStolb/TERMINAL-06-firmware/knowledge/Без названия.png

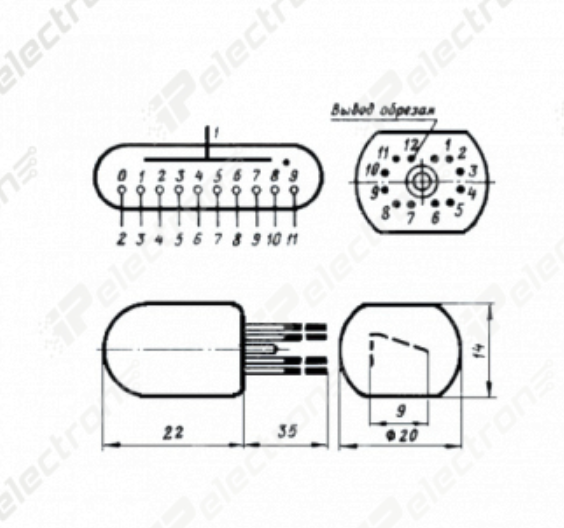
knowledge/Без названия.png
