BobStolb/TERMINAL-06-firmware/PCB/IN-12_norm/gyver_copper.png

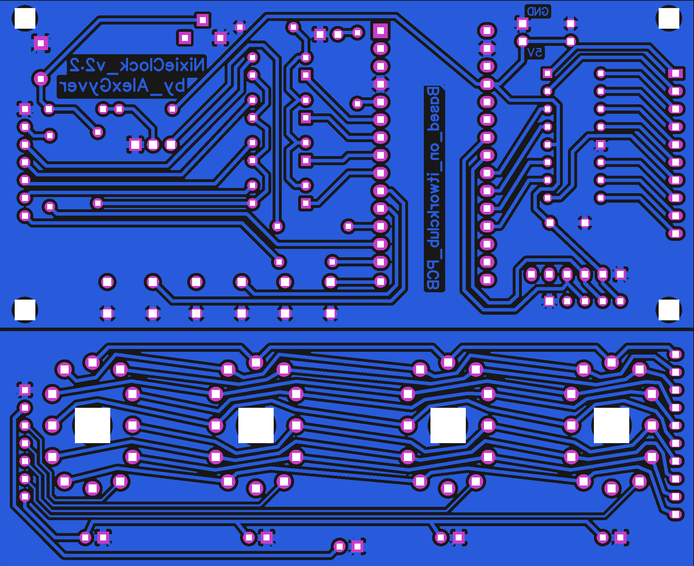
PCB/IN-12_norm/gyver_copper.png
