BobStolb/TERMINAL-06-firmware/PCB/TS06-DISP/copper.png

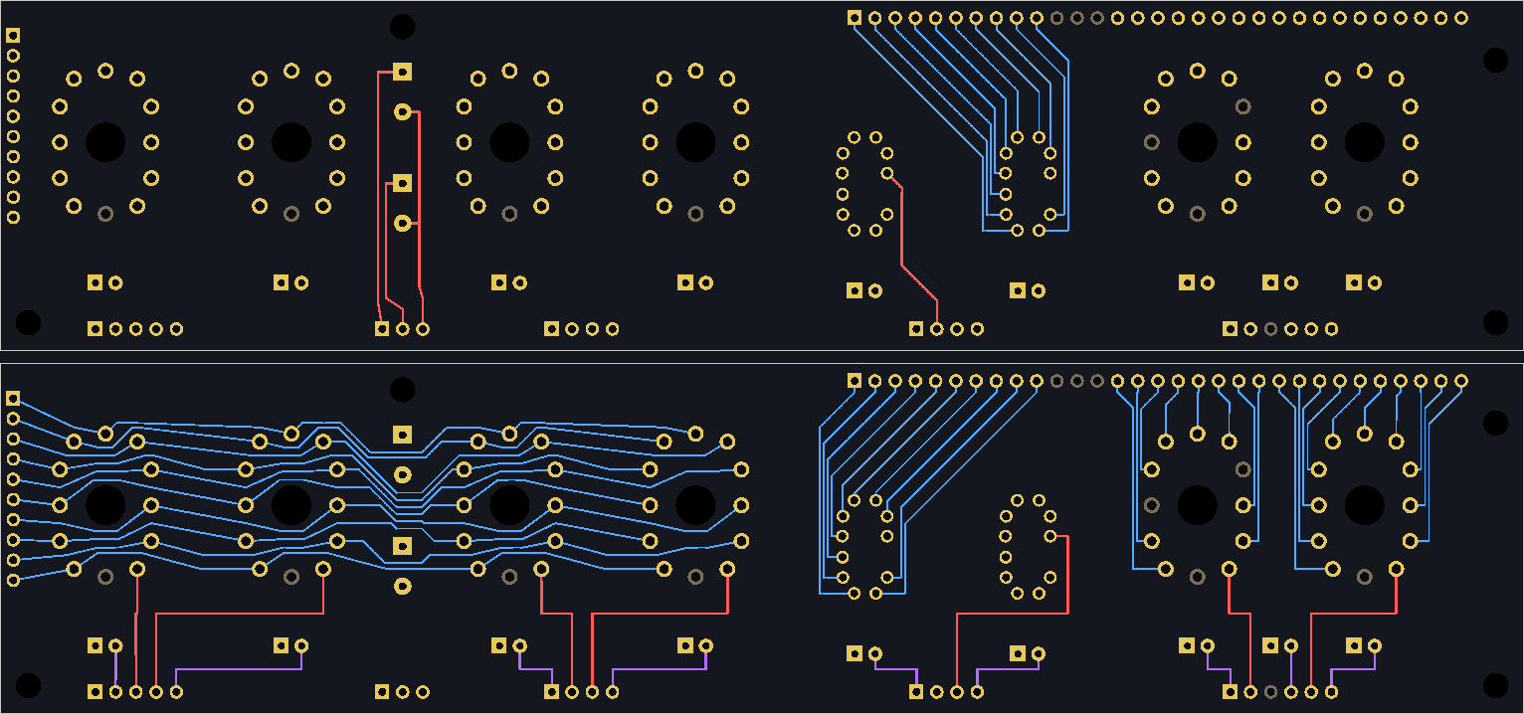
PCB/TS06-DISP/copper.png
