BobStolb/TERMINAL-06-firmware/PCB/TS06-DRV/copper.png

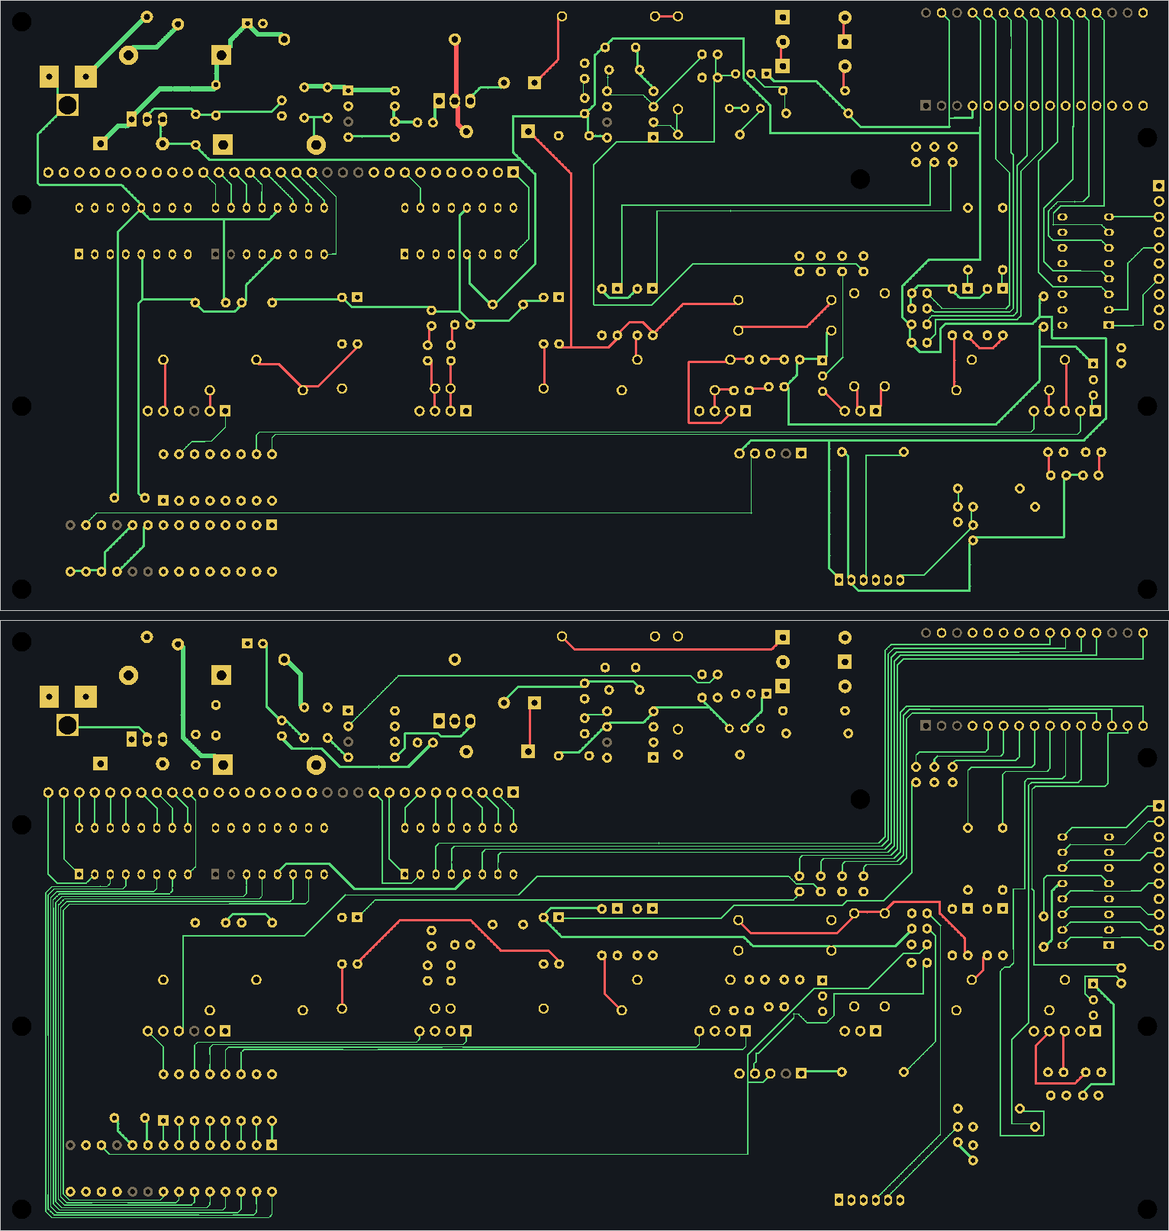
PCB/TS06-DRV/copper.png
