BobStolb/TERMINAL-06-firmware/PCB/TS06-FASCIA-rhythm/composite-0-centred.png

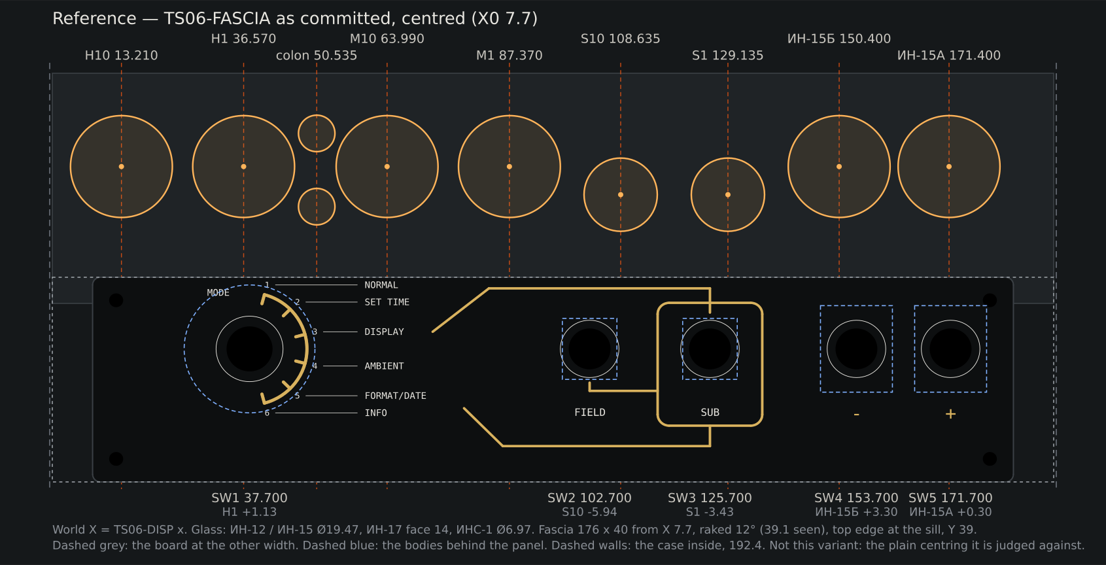
PCB/TS06-FASCIA-rhythm/composite-0-centred.png
