BobStolb/TERMINAL-06-firmware/PCB/TS06-FASCIA-rhythm/composite-A.png

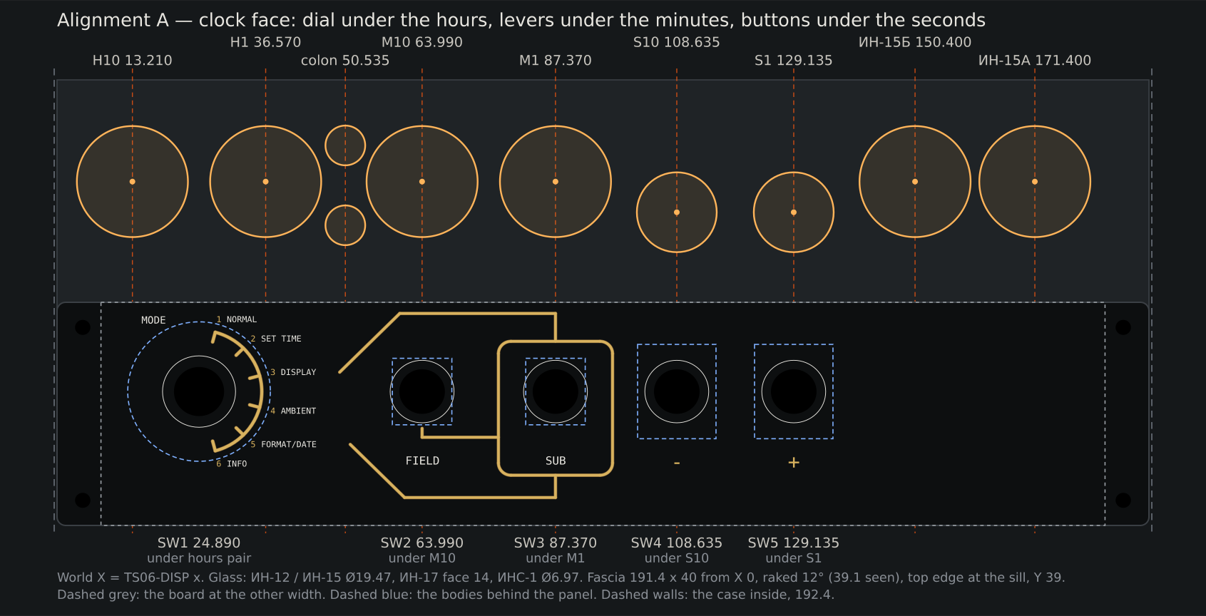
PCB/TS06-FASCIA-rhythm/composite-A.png
