BobStolb/TERMINAL-06-firmware/PCB/TS06-FASCIA-rhythm/composite-B.png

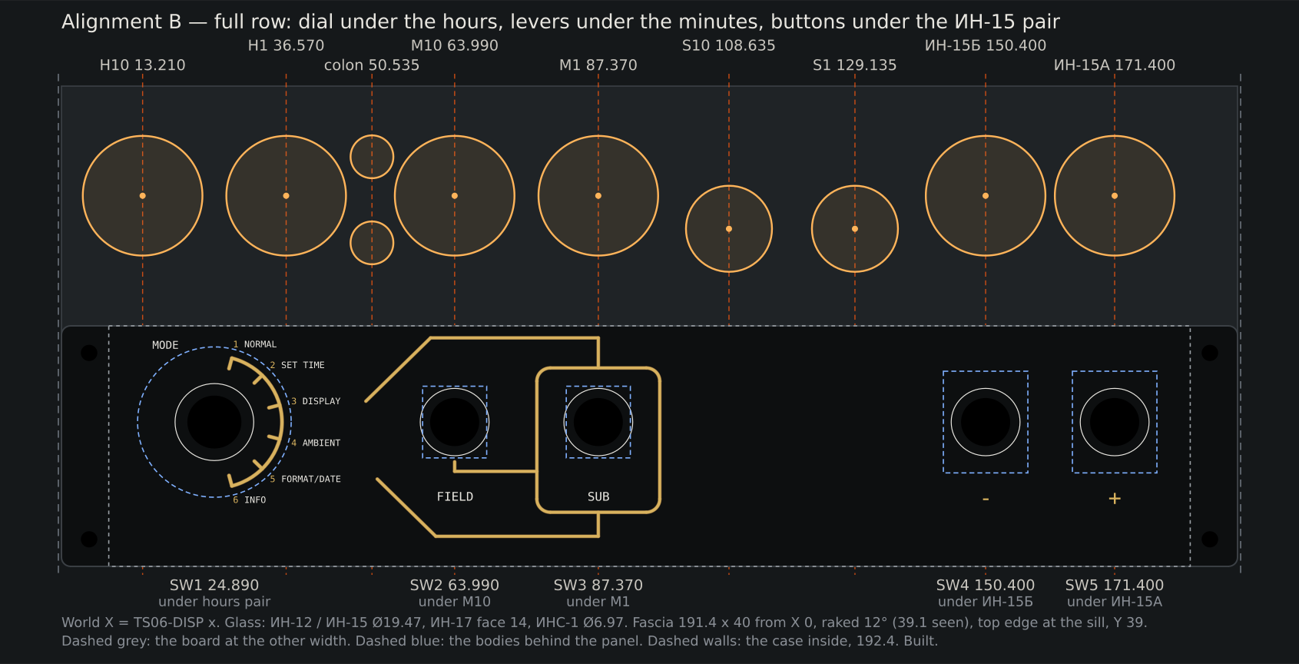
PCB/TS06-FASCIA-rhythm/composite-B.png
