BobStolb/TERMINAL-06-firmware/PCB/TS06-FASCIA-rhythm/composite-C.png

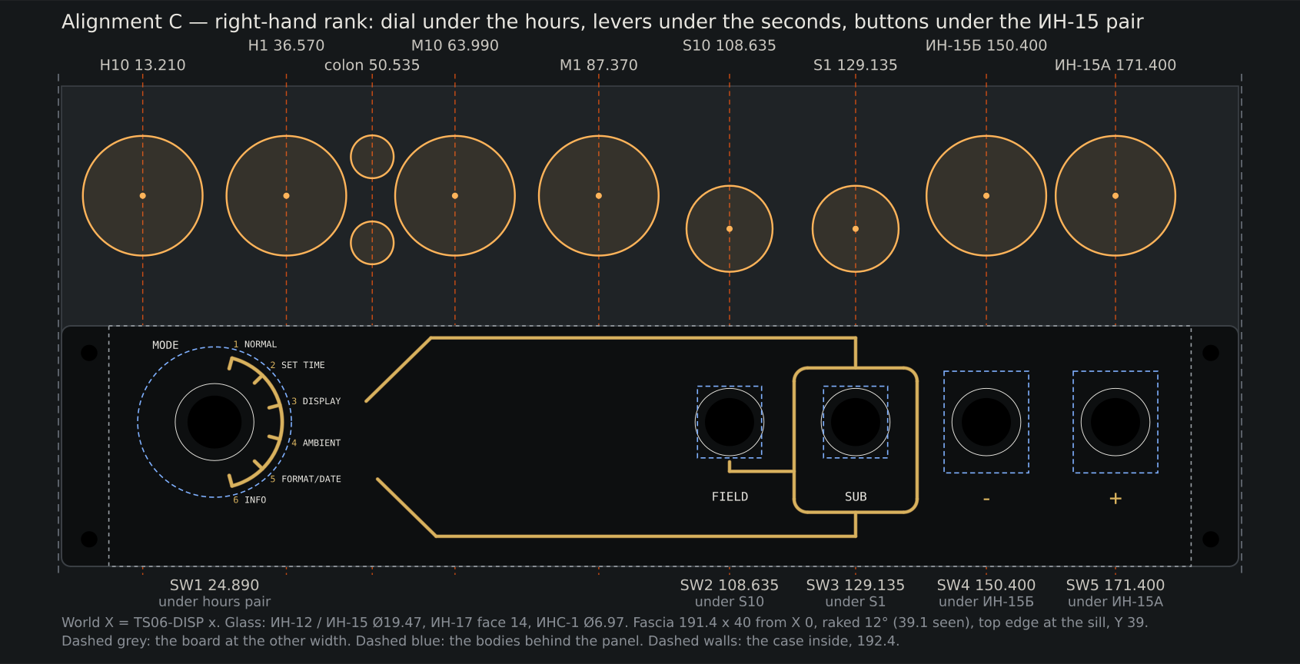
PCB/TS06-FASCIA-rhythm/composite-C.png
