BobStolb/TERMINAL-06-firmware/PCB/TS06-FASCIA-rhythm/preview.png

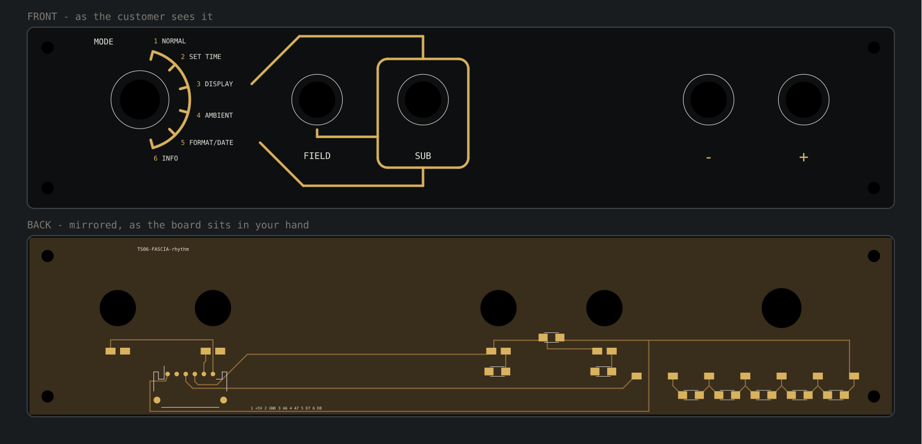
PCB/TS06-FASCIA-rhythm/preview.png
