BobStolb/TERMINAL-06-firmware/PCB/TS06-FASCIA-THT/preview.png

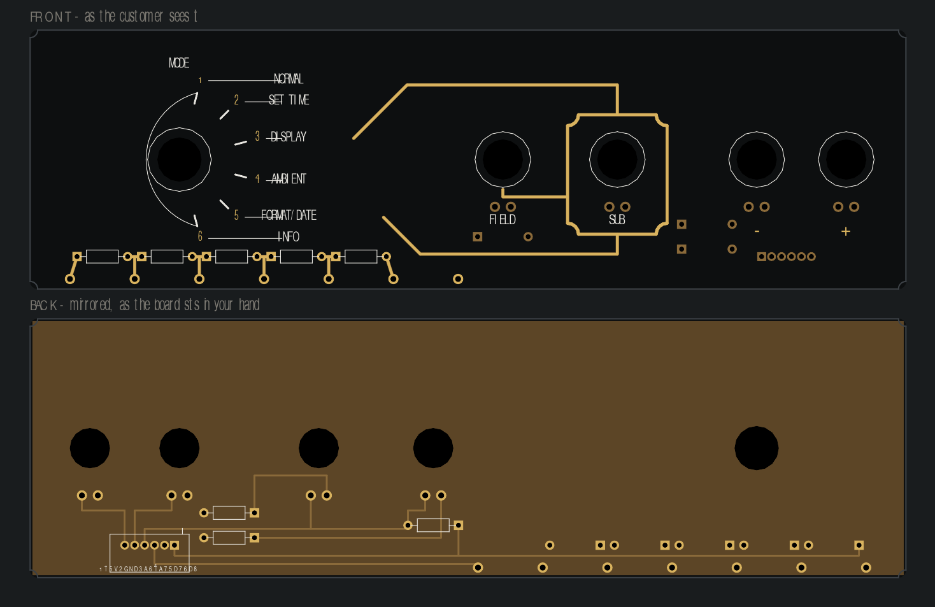
PCB/TS06-FASCIA-THT/preview.png
