BobStolb/TERMINAL-06-firmware/PCB/TS06-FASCIA-wide/case_front_compare.png

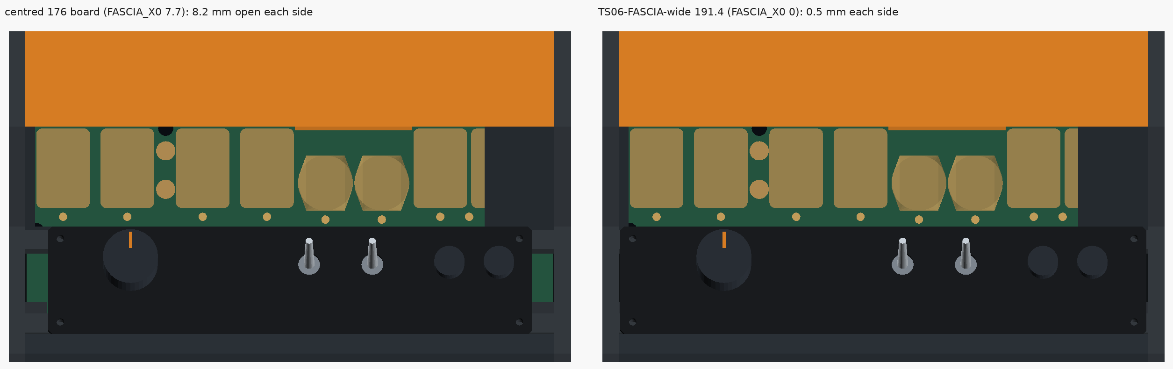
PCB/TS06-FASCIA-wide/case_front_compare.png
