BobStolb/TERMINAL-06-firmware/PCB/TS06-FASCIA-wide/front_composite.png

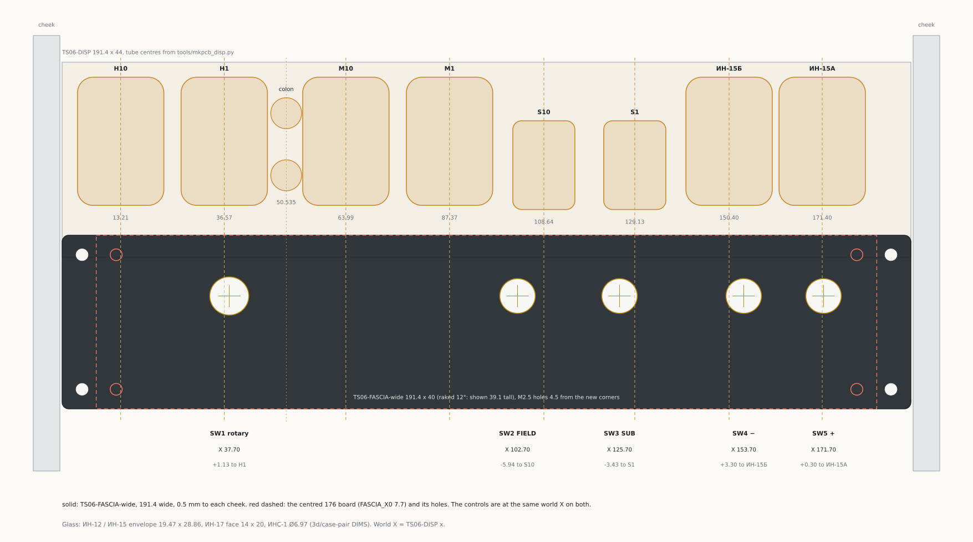
PCB/TS06-FASCIA-wide/front_composite.png
