BobStolb/TERMINAL-06-firmware/PCB/TS06-FASCIA-wide/preview.png

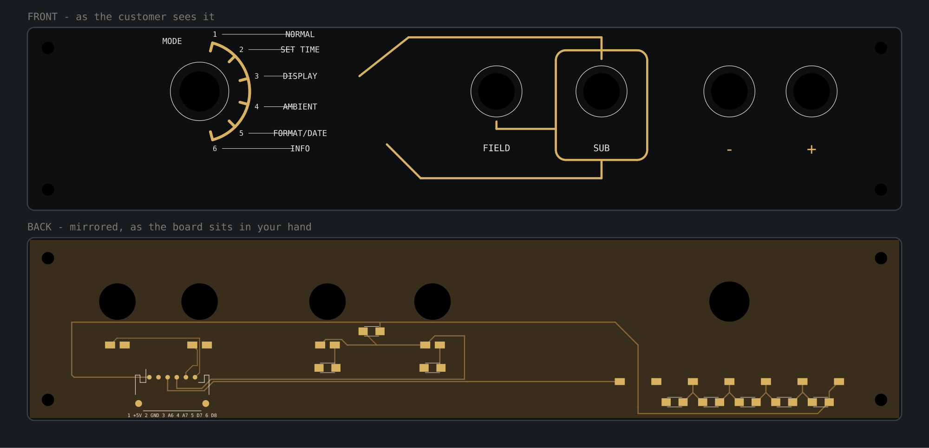
PCB/TS06-FASCIA-wide/preview.png
