BobStolb/TERMINAL-06-firmware/PCB/TS06-MAIN-THT/copper.png

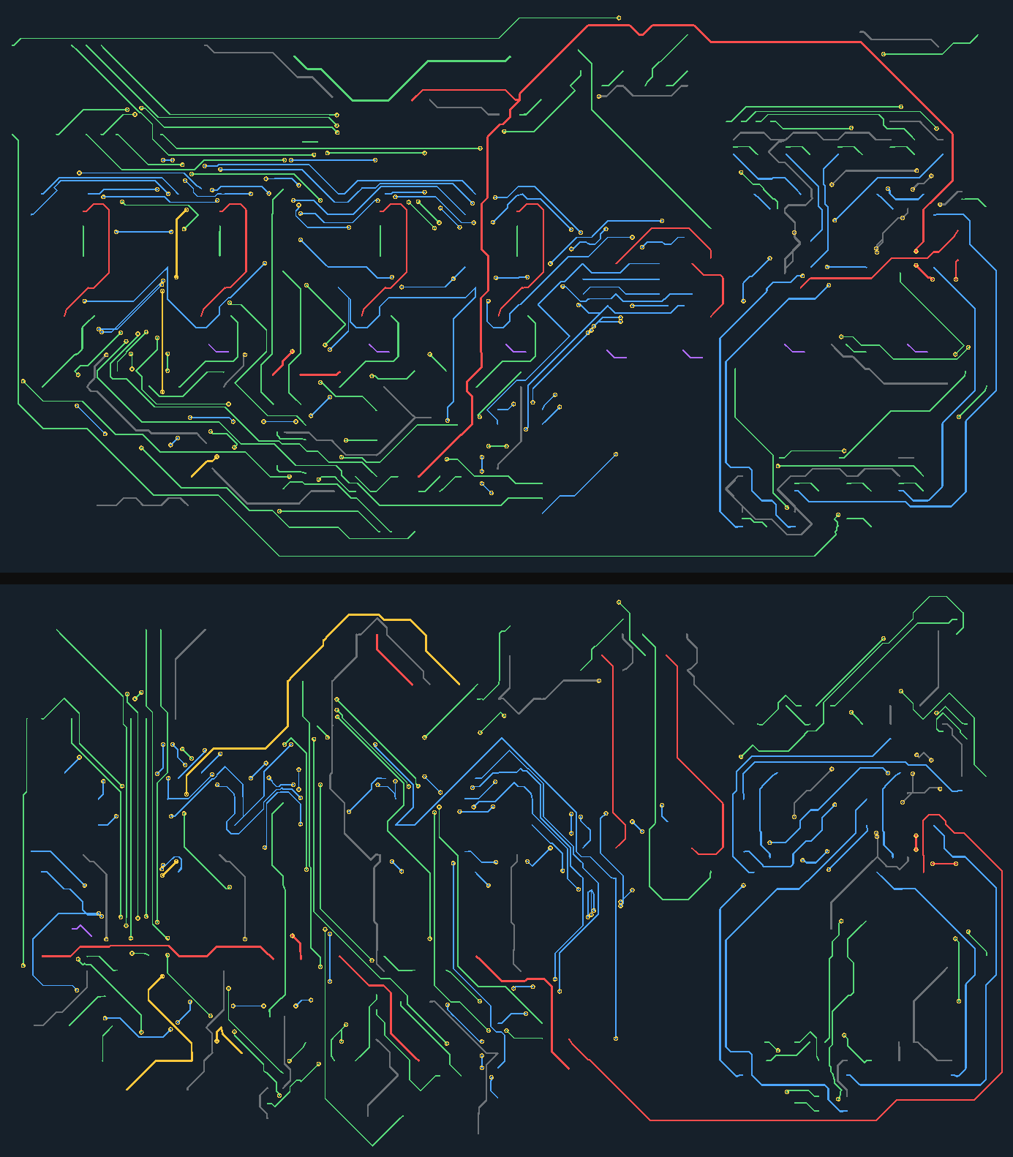
PCB/TS06-MAIN-THT/copper.png
