BobStolb/TERMINAL-06-firmware/PCB/TS06-MAIN/copper.png

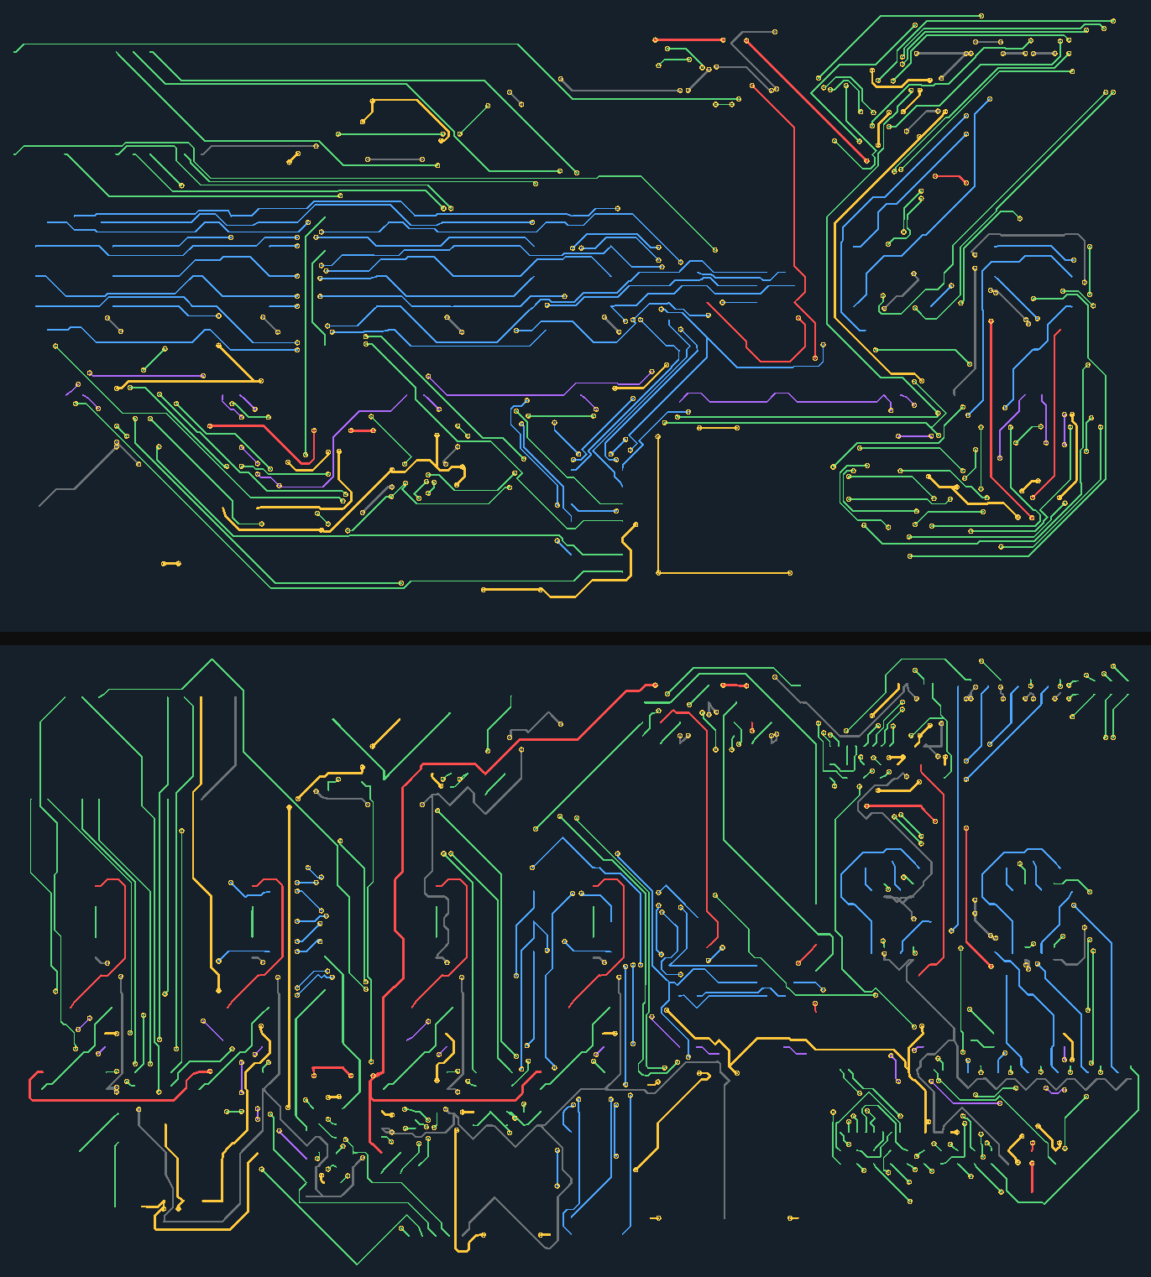
PCB/TS06-MAIN/copper.png
