BobStolb/TERMINAL-06-firmware/PCB/TS06-DRV/bom.md

# TS06-DRV — bill of materials

Generated by `tools/bom_pair.py` from `tools/ts06pair.py`; do not edit by hand.
96 parts fitted, 12 footprints left empty. Every part is through-hole.

| Qty | Part | Value | Footprint | References |
|---|---|---|---|---|
| 1 | 5 V switching regulator | R-78E5.0-1.0 | TS06_R-78E_SIP3 | U14 |
| 1 | Arduino Nano | Arduino Nano | TS06_Arduino_Nano | U1 |
| 2 | Ceramic capacitor | 100n | TS06_C_Disc_P2.50mm | C5, C6 |
| 7 | Ceramic capacitor | 100n | TS06_C_Disc_P5.00mm | C1, C4, C13, C14, C15, C16, C17 |
| 2 | Ceramic capacitor | 10n | TS06_C_Disc_P2.50mm | C18, C19 |
| 2 | Ceramic capacitor | 10u | TS06_C_Disc_P5.00mm | C3, C11 |
| 1 | Ceramic capacitor | 10u 25V | TS06_C_Disc_P5.00mm | C10 |
| 2 | Ceramic capacitor | 1u 50V | TS06_C_Disc_P5.00mm | C9, C12 |
| 1 | Choke, axial, lying: **Bourns 5900-221-RC**, 220 µH ±10 %, Isat 1.8 A (Digi-Key; 1.89 A in another distributor's listing), Irated 1.6 A, DCR 0.162 Ω, Ø11.5 × 22.9 mm, Ø0.8 mm leads. The converter peaks at 1.18-1.44 A; no Ø12 radial of 220 µH reaches that (RLB1314-221KL 0.68 A) | 220u 1.8A 5900-221-RC | TS06_L_Axial_D11.5mm_L22.9mm_P27.94mm | L1 |
| 1 | DC jack | DC 5.5x2.1 | TS06_BarrelJack_Horizontal | XS1 |
| 1 | DS3231 mini module on a 5-way **PLS (male)** header: the module's own socket plugs on. Pad 1 (square) is GND; the module's + goes to pad 5 | DS3231 mini | TS06_PinHeader_1x05_DS3231 | U13 |
| 1 | Dual comparator | LM393 | TS06_DIP-8_W7.62mm_Socket | U12 |
| 1 | Electrolytic capacitor | 100u 25V | TS06_CP_Radial_D6.3mm_P2.50mm | C8 |
| 1 | Electrolytic capacitor | 4u7 400V | TS06_CP_Radial_D10.0mm_P5.00mm | C7 |
| 1 | Fast rectifier | HER106 / UF4007 | TS06_D_DO-41_P10.16mm | VD1 |
| 1 | I2C port expander | MCP23017-E/SP | TS06_DIP-28_W7.62mm_Socket | U3 |
| 1 | JST PH, vertical (top entry) | PH 6 vertical | TS06_JST_PH_B6B-PH-K_Vertical | J1 |
| 1 | MOSFET driver | TC4420 | TS06_DIP-8_W7.62mm_Socket | U11 |
| 1 | N-MOSFET 500 V | IRF840 | TS06_TO-220-3_Vertical_HV | VT21 |
| 2 | NPN 300 V | MPSA42 | TS06_TO-92_Inline_Wide | VT1, VT20 |
| 1 | NPN small-signal, TO-92, **E-B-C** (2N3904; not a BC547, which is C-B-E): the OV clamp | 2N3904 | TS06_TO-92_Inline_Wide | VT2 |
| 4 | Nixie decoder К155ИД1 | K155ID1 | TS06_DIP-16_W7.62mm_Socket_Oval | U2, U15, U16, U17 |
| 6 | Optocoupler, Darlington 300 V (TLP627 is obsolete: TLP627MF, from authorised stock) | TLP627 | TS06_DIP-4_W7.62mm_Socket | U5, U6, U7, U8, U9, U10 |
| 1 | PTC fuse, 1.1 A hold, radial, 5.1 mm leads (e.g. Bourns MF-R110; the footprint is the larger MF-RG1100 outline, which is an 11 A part) | PTC 1.1A | TS06_Fuse_PTC_MF-RG1100 | F1 |
| 1 | Resistor network, isolated, DIP-16 | 8x220R isolated DIP-16 | TS06_DIP-16_W7.62mm_Socket | RN1 |
| 1 | Resistor, 0.25 W | 100k | TS06_R_Axial_DIN0207_P10.16mm | R75 |
| 1 | Resistor, 0.25 W | 10R | TS06_R_Axial_DIN0207_P2.54mm_Vertical | R67 |
| 1 | Resistor, 0.25 W | 10k | TS06_R_Axial_DIN0207_P10.16mm | R76 |
| 3 | Resistor, 0.25 W | 10k | TS06_R_Axial_DIN0207_P2.54mm_Vertical | R1, R68, R71 |
| 2 | Resistor, 0.25 W | 10k 1% | TS06_R_Axial_DIN0207_P2.54mm_Vertical | R69, R70 |
| 1 | Resistor, 0.25 W | 18k 1% | TS06_R_Axial_DIN0207_P10.16mm | R64 |
| 1 | Resistor, 0.25 W | 1M | TS06_R_Axial_DIN0207_P10.16mm | R72 |
| 1 | Resistor, 0.25 W | 1M | TS06_R_Axial_DIN0207_P2.54mm_Vertical | R65 |
| 2 | Resistor, 0.25 W | 1k | TS06_R_Axial_DIN0207_P10.16mm | R73, R74 |
| 1 | Resistor, 0.25 W | 220R | TS06_R_Axial_DIN0207_P2.54mm_Vertical | R53 |
| 1 | Resistor, 0.25 W | 2k2 | TS06_R_Axial_DIN0207_P2.54mm_Vertical | R66 |
| 2 | Resistor, 0.25 W | 470R | TS06_R_Axial_DIN0207_P10.16mm | R21, R22 |
| 5 | Resistor, 0.25 W | 470R | TS06_R_Axial_DIN0207_P2.54mm_Vertical | R20, R23, R24, R25, R26 |
| 2 | Resistor, 0.25 W | 4k7 | TS06_R_Axial_DIN0207_P2.54mm_Vertical | R54, R55 |
| 2 | Resistor, 0.5 W 350 V: МЛТ-0,5 or С2-23-0,5 (body ≤ Ø4.2 × 10.8 mm, leads Ø0.8 mm; 1.1 mm holes at 15.24 mm) | 12k | TS06_R_Axial_MLT-0.5_P15.24mm | R31, R32 |
| 2 | Resistor, 0.5 W 350 V: МЛТ-0,5 or С2-23-0,5 (body ≤ Ø4.2 × 10.8 mm, leads Ø0.8 mm; 1.1 mm holes at 15.24 mm) | 18k | TS06_R_Axial_MLT-0.5_P15.24mm | R56, R57 |
| 2 | Resistor, 0.5 W 350 V: МЛТ-0,5 or С2-23-0,5 (body ≤ Ø4.2 × 10.8 mm, leads Ø0.8 mm; 1.1 mm holes at 15.24 mm) | 220k | TS06_R_Axial_MLT-0.5_P15.24mm | R58, R59 |
| 2 | Resistor, 0.5 W 350 V: МЛТ-0,5 or С2-23-0,5 (body ≤ Ø4.2 × 10.8 mm, leads Ø0.8 mm; 1.1 mm holes at 15.24 mm) | 470k | TS06_R_Axial_MLT-0.5_P15.24mm | R60, R61 |
| 4 | Resistor, 0.5 W 350 V: МЛТ-0,5 or С2-23-0,5 (body ≤ Ø4.2 × 10.8 mm, leads Ø0.8 mm; 1.1 mm holes at 15.24 mm) | 6k8 TBC | TS06_R_Axial_MLT-0.5_P15.24mm | R27, R28, R29, R30 |
| 2 | Resistor, 0.5 W 350 V: МЛТ-0,5 or С2-23-0,5 (body ≤ Ø4.2 × 10.8 mm, leads Ø0.8 mm; 1.1 mm holes at 15.24 mm) | 750k 1% | TS06_R_Axial_MLT-0.5_P15.24mm | R62, R63 |
| 1 | Schottky diode | 1N5822 | TS06_D_DO-201AD_P15.24mm | VD2 |
| 1 | Schottky diode, across U14 (5 V back-feed from USB) | 1N5819 | TS06_D_DO-41_P10.16mm | VD3 |
| 1 | Socket strip, straight (PBS), 8.5 mm | PBS-10 female 2.54 | TS06_PinSocket_1x10 | XS11 |
| 1 | Socket strip, straight (PBS), 8.5 mm | PBS-3 female 2.54 | TS06_PinSocket_1x03 | XS22 |
| 1 | Socket strip, straight (PBS), 8.5 mm | PBS-31 female 2.54 | TS06_PinSocket_1x31 | XS12 |
| 2 | Socket strip, straight (PBS), 8.5 mm | PBS-4 female 2.54 | TS06_PinSocket_1x04 | XS23, XS24 |
| 1 | Socket strip, straight (PBS), 8.5 mm | PBS-5 female 2.54 | TS06_PinSocket_1x05 | XS21 |
| 1 | Socket strip, straight (PBS), 8.5 mm | PBS-6 female 2.54 | TS06_PinSocket_1x06 | XS25 |
| 1 | TVS diode, unidirectional, 1500 W, DO-201 (1.5KE18A: VBR 17.1-18.9 V): trips F1 on a 19-24 V adapter | 1.5KE18A | TS06_D_DO-201AD_P15.24mm | VD4 |
| 1 | Trimmer, multi-turn | 5k | TS06_Trimmer_3296W | RP1 |
| 1 | Zener diode, 1 W, ±5 %, DO-41: the OV clamp's string (82 + 82 + 75 V, clamps 225-270 V) | 1N4761A | TS06_D_DO-41_P10.16mm | VD7 |
| 2 | Zener diode, 1 W, ±5 %, DO-41: the OV clamp's string (82 + 82 + 75 V, clamps 225-270 V) | 1N4762A | TS06_D_DO-41_P10.16mm | VD5, VD6 |

## Not fitted (DNP) unless the bench asks for them

| Qty | Part | Value | Footprint | References |
|---|---|---|---|---|
| 12 | Resistor, 0.25 W | 510k | TS06_R_Axial_DIN0207_P2.54mm_Vertical | R33, R34, R35, R36, R37, R38, R39, R40, R41, R42, R43, R44 |

## Hardware

| Qty | Item | For |
|---|---|---|
| 1 | DIP-28 socket, 300 mil (skinny) | U3 |
| 6 | DIP-4 socket, 300 mil | U5, U6, U7, U8, U9, U10 |
| 2 | DIP-8 socket, 300 mil | U11, U12 |
| 2 | Socket strip PBS-15, 2.54 mm | U1, the Nano stays removable |
| 4 | Mounting screw M3 + **nylon washer**, to the case | H5-H8, two into each cheek (tracks pass 2.2 mm from H5's centre) |
| 1 | Fascia lead, 6-way JST PH, 1:1, 180-200 mm: 2 × PHR-6 housings + 12 × SPH-002T-P0.5S crimps, or a ready-made lead. Pin 1 = +5V at both ends; beep it out before first power | J1 to the fascia's J1 |
