BobStolb/TERMINAL-06-firmware/PCB/TS06-DISP/bom.md

# TS06-DISP — bill of materials

Generated by `tools/bom_pair.py` from `tools/ts06pair.py`; do not edit by hand.
26 parts fitted, 0 footprints left empty. Every part is through-hole.

| Qty | Part | Value | Footprint | References |
|---|---|---|---|---|
| 9 | LED, 3 mm | amber 3mm | TS06_LED_D3.0mm | HL1, HL2, HL3, HL4, HL5, HL6, HL7, HL8, HL9 |
| 2 | Neon lamp | INS-1 | TS06_INS1_Lamp | V7, V8 |
| 4 | Nixie tube | IN-12A | TS06_IN12_Socket | V1, V2, V3, V4 |
| 1 | Nixie tube | IN-15A | TS06_IN12_Socket | V10 |
| 1 | Nixie tube | IN-15B | TS06_IN12_Socket | V9 |
| 2 | Nixie tube | IN-17 | TS06_IN17_Socket | V5, V6 |
| 1 | Pin header, straight (PLS) | PLS-10 male 2.54 | TS06_PinHeader_1x10 | XP11 |
| 1 | Pin header, straight (PLS) | PLS-3 male 2.54 | TS06_PinHeader_1x03 | XP22 |
| 1 | Pin header, straight (PLS) | PLS-31 male 2.54 | TS06_PinHeader_1x31 | XP12 |
| 2 | Pin header, straight (PLS) | PLS-4 male 2.54 | TS06_PinHeader_1x04 | XP23, XP24 |
| 1 | Pin header, straight (PLS) | PLS-5 male 2.54 | TS06_PinHeader_1x05 | XP21 |
| 1 | Pin header, straight (PLS) | PLS-6 male 2.54 | TS06_PinHeader_1x06 | XP25 |

## Hardware

| Qty | Item | For |
|---|---|---|
| 4 | Standoff M3, 11 mm, female-female, **nylon** (or brass with nylon washers at both ends), with 8 M3 × 6 screws | the four holes shared with TS06-DRV (11 mm = 8.5 mm PBS + 2.5 mm PLS body). Tracks pass 2.2-2.4 mm from H3's centre on both boards, under a metal standoff's 2.75-3.2 |
| 72 | Tube socket contact, 12 per tube; its tail must suit the 1.2 mm finished hole (choose the part, then check) | V1–V4 (ИН-12), V9–V10 (ИН-15) |
| 2 | ИН-17 spacer, holds the glass ≥ 6.4 mm off the board (the ТУ's 8 mm soldering rule) | V5, V6 |
