BobStolb/TERMINAL-06-firmware/PCB/TS06-MAIN-THT/bom.md

# TS06-MAIN-THT — bill of materials

Generated by `tools/bom_main.py --tht` from `tools/ts06main.py`; do not edit by hand.
134 parts fitted, 12 footprints left empty.

| Qty | Part | Value | Footprint | References |
|---|---|---|---|---|
| 1 | Arduino Nano | Arduino Nano | TS06_Arduino_Nano_Back | U1 |
| 7 | Capacitor | 100n | TS06_C_Disc_P2.50mm_Back | C1, C2, C4, C5, C6, C13, C14 |
| 1 | Capacitor | 100u 25V | TS06_CP_Radial_D6.3mm_P2.50mm_Back | C8 |
| 2 | Capacitor | 10u | TS06_C_Disc_P5.00mm_Back | C3, C11 |
| 1 | Capacitor | 10u 25V | TS06_C_Disc_P5.00mm_Back | C10 |
| 2 | Capacitor | 1u 50V | TS06_C_Disc_P5.00mm_Back | C9, C12 |
| 1 | Capacitor | 4u7 400V | TS06_CP_Radial_D8.0mm_P3.50mm_Back | C7 |
| 1 | JST PH connector, 6-way | PH 6 | TS06_JST_PH_S6B-PH-K-S_Back | J1 |
| 1 | Fast rectifier | HER106 | TS06_D_DO-41_P10.16mm_Back | VD1 |
| 1 | Schottky diode | 1N5822 | TS06_D_DO-201_P15.24mm_Back | VD2 |
| 1 | PTC fuse | PTC 1.1A | TS06_Fuse_Radial_MF-R_Back | F1 |
| 1 | DC jack | DC 5.5x2.1 | TS06_BarrelJack_Back | XS1 |
| 1 | Nixie decoder К155ИД1 | K155ID1 | TS06_DIP-16_Back | U2 |
| 1 | Inductor | 220u 2A | TS06_L_Radial_D10.0mm_P5.00mm_Back | L1 |
| 9 | LED, amber 3 mm | amber 3mm | TS06_LED_D3.0mm | HL1, HL2, HL3, HL4, HL5, HL6, HL7, HL8, HL9 |
| 1 | Dual comparator | LM393 | TS06_DIP-8_Back | U12 |
| 2 | Neon lamp ИНС-1 | INS-1 | TS06_INS1_Lamp | V7, V8 |
| 2 | I2C port expander | MCP23017 | TS06_DIP-28W_Back | U3, U4 |
| 1 | N-MOSFET 500 V | IRF840 | TS06_TO-220_Horizontal_Back | VT21 |
| 20 | NPN 300 V | MPSA42 | TS06_TO-92_Back | VT1, VT2, VT3, VT4, VT5, VT6, VT7, VT8, VT9, VT10, VT11, VT12, VT13, VT14, VT15, VT16, VT17, VT18, VT19, VT20 |
| 1 | Resistor | 10R | TS06_R_Axial_L6.3mm_P2.54mm_Vertical_Back | R67 |
| 21 | Resistor | 10k | TS06_R_Axial_L6.3mm_P2.54mm_Vertical_Back | R1, R2, R3, R4, R5, R6, R7, R8, R9, R10, R11, R12, R13, R14, R15, R16, R17, R18, R19, R68, R71 |
| 2 | Resistor | 10k 1% | TS06_R_Axial_L6.3mm_P2.54mm_Vertical_Back | R69, R70 |
| 2 | Resistor | 12k | TS06_R_Axial_L9.9mm_P5.08mm_Vertical_Back | R31, R32 |
| 1 | Resistor | 15k 1% | TS06_R_Axial_L6.3mm_P2.54mm_Vertical_Back | R64 |
| 1 | Resistor | 1M | TS06_R_Axial_L6.3mm_P2.54mm_Vertical_Back | R65 |
| 9 | Resistor | 220R | TS06_R_Axial_L6.3mm_P2.54mm_Vertical_Back | R45, R46, R47, R48, R49, R50, R51, R52, R53 |
| 2 | Resistor | 220k | TS06_R_Axial_L9.9mm_P5.08mm_Vertical_Back | R58, R59 |
| 1 | Resistor | 2k2 | TS06_R_Axial_L6.3mm_P2.54mm_Vertical_Back | R66 |
| 7 | Resistor | 470R | TS06_R_Axial_L6.3mm_P2.54mm_Vertical_Back | R20, R21, R22, R23, R24, R25, R26 |
| 2 | Resistor | 470k | TS06_R_Axial_L6.3mm_P2.54mm_Vertical_Back | R60, R61 |
| 2 | Resistor | 4k7 | TS06_R_Axial_L6.3mm_P2.54mm_Vertical_Back | R54, R55 |
| 4 | Resistor | 6k8 TBC | TS06_R_Axial_L9.9mm_P5.08mm_Vertical_Back | R27, R28, R29, R30 |
| 2 | Resistor | 750k 1% | TS06_R_Axial_L6.3mm_P2.54mm_Vertical_Back | R62, R63 |
| 2 | Resistor | 8k2 | TS06_R_Axial_L9.9mm_P5.08mm_Vertical_Back | R56, R57 |
| 1 | RTC module | DS3231 mini | TS06_PinHeader_1x05_Back | U13 |
| 1 | 5 V switching regulator | R-78E5.0-1.0 | TS06_R78E_SIP3_Back | U14 |
| 1 | MOSFET driver | TC4420 | TS06_DIP-8_Back | U11 |
| 6 | Optocoupler, Darlington | TLP627 | TS06_DIP-4_Back | U5, U6, U7, U8, U9, U10 |
| 1 | Trimmer | 10k | TS06_Trimmer_3296W_Back | RP1 |
| 4 | Nixie tube | IN-12A | TS06_IN12_Socket | V1, V2, V3, V4 |
| 1 | Nixie tube | IN-15A | TS06_IN12_Socket | V10 |
| 1 | Nixie tube | IN-15B | TS06_IN12_Socket | V9 |
| 2 | Nixie tube | IN-17 | TS06_IN17_Socket | V5, V6 |

## Not fitted (DNP) unless the bench asks for them

| Qty | Part | Value | Footprint | References |
|---|---|---|---|---|
| 12 | Resistor | 510k | TS06_R_Axial_L6.3mm_P2.54mm_Vertical_Back | R33, R34, R35, R36, R37, R38, R39, R40, R41, R42, R43, R44 |

## What this board adds and removes against the three it replaces

Compared with the inherited AlexGyver board + TS06-SEC + TS06-COLON, one TS06-MAIN unit needs:

* **new:** the 12 V input stage (jack, PTC, Schottky, 100 µF), an R-78E5.0-1.0 regulator, a TC4420 driver, an LM393 comparator and the rail divider with its trimmer, one anode resistor per digit tube (six), four more TLP627 (six in all instead of the inherited four plus SEC's two), two more backlight LEDs (eight), and in the SMD build a bare DS3231SN with a CR2032 holder;
* **unchanged in kind:** the Nano, the К155ИД1, the two MCP23017 and eighteen MPSA42/MMBTA42 with their base resistors, the two ИНС-1 with their own 220 kΩ ballasts, the eight tubes, the fascia connector;
* **gone:** the inherited board itself, SEC's XS1/XS2/XS3/XS4 and the colon board's connector and harnesses, the 470 kΩ bleed trimmer and the shared 10 kΩ anode resistor of the old converter.
