BobStolb/TERMINAL-06-firmware/3d/IN17.step

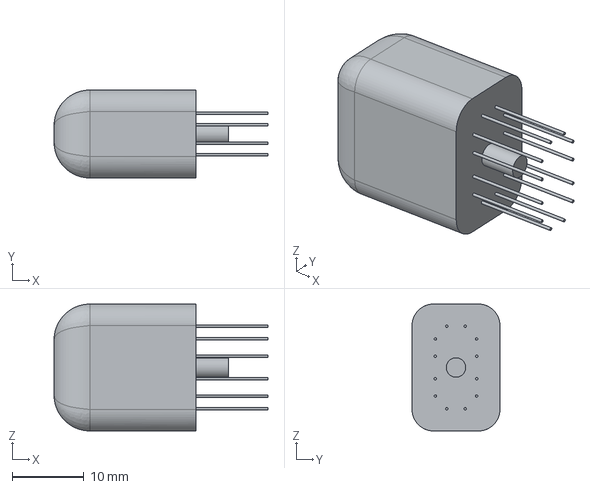
[picture p130: CAD file, 2026-09-17]
3d/IN17.step
29.8 x 12.2 x 17.7 mm
