BobStolb/TERMINAL-06-firmware/3d/jig/jig_shims.stl

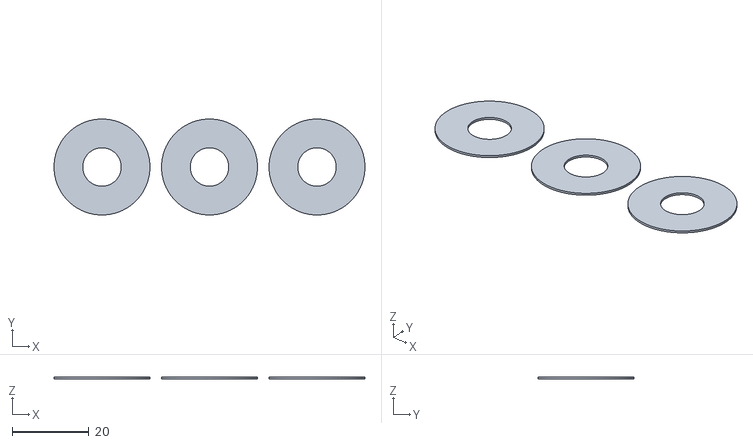
[picture p131: CAD file, 2026-10-07]
3d/jig/jig_shims.stl
81.0 x 25.0 x 0.5
