BobStolb/TERMINAL-06-firmware/3d/case-pair/out/base.stl

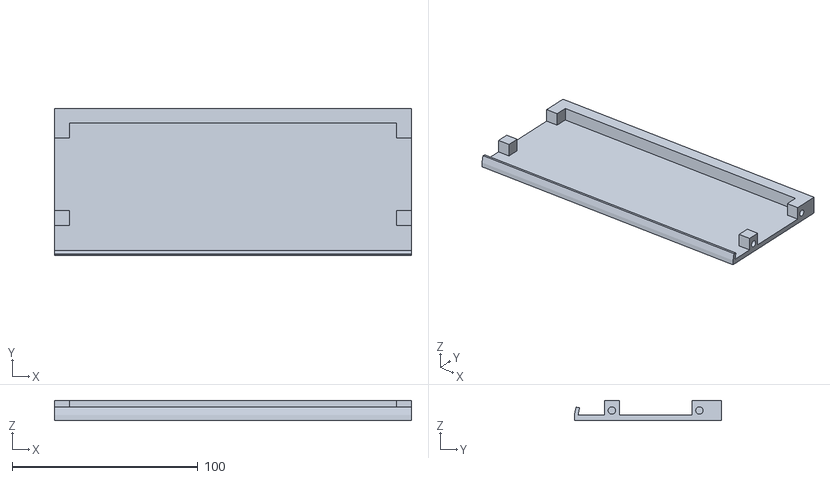
[picture p132: CAD file, 2026-10-07]
3d/case-pair/out/base.stl
192.4 x 79.4 x 11.0
