BobStolb/TERMINAL-06-firmware/3d/jig/jig_plate_flat.stl

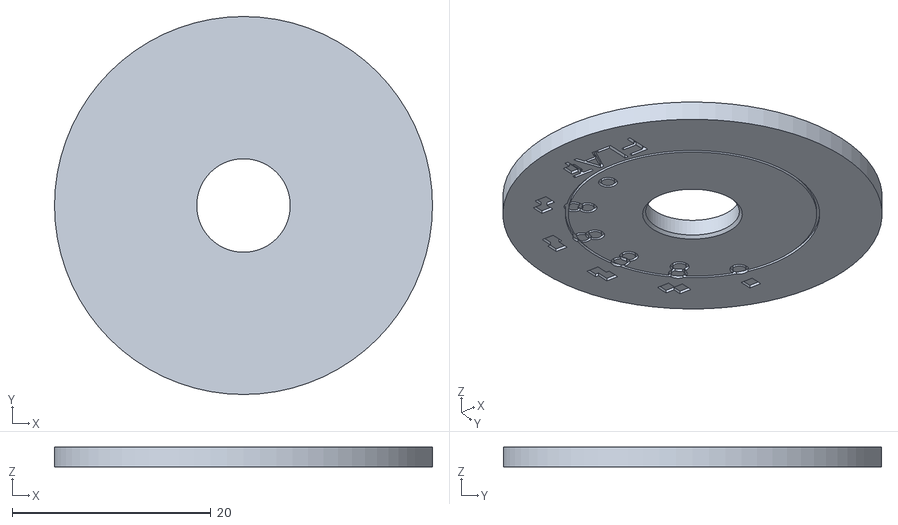
[picture p133: CAD file, 2026-10-07]
3d/jig/jig_plate_flat.stl
38.0 x 38.0 x 2.00
