BobStolb/TERMINAL-06-firmware/3d/knob/knob_A.stl

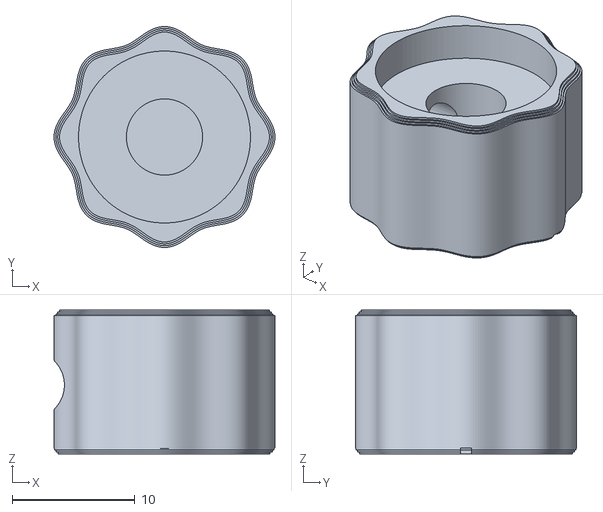
[picture p134: CAD file, 2026-10-07]
3d/knob/knob_A.stl
18.0 x 18.0 x 11.7
