BobStolb/TERMINAL-06-firmware/3d/case-pair/out/cheek_l.stl

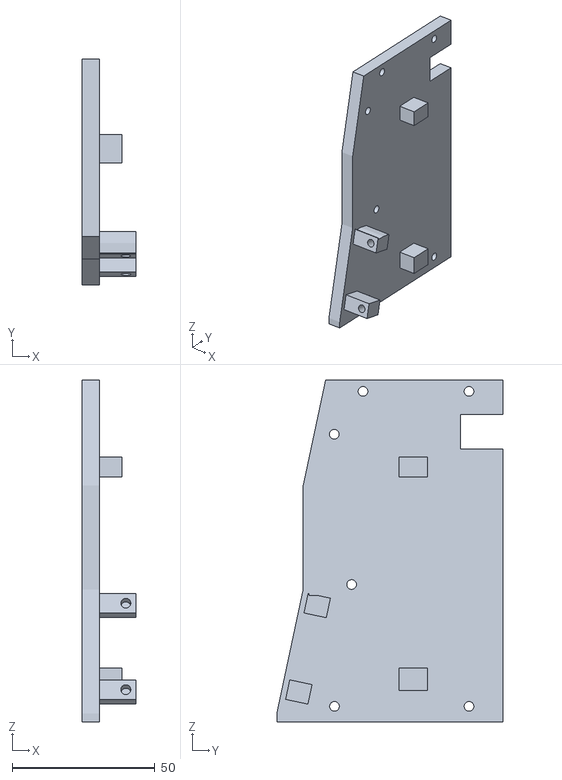
[picture p135: CAD file, 2026-10-07]
3d/case-pair/out/cheek_l.stl
18.8 x 79.4 x 120.0
