BobStolb/TERMINAL-06-firmware/3d/IN12.step

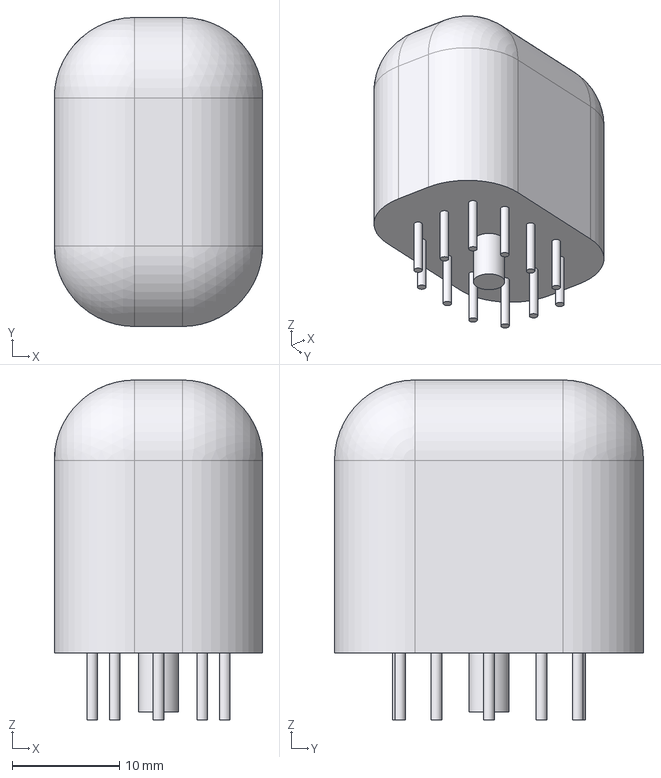
[picture p136: CAD file, 2026-09-17]
3d/IN12.step
19.5 x 28.9 x 31.8 mm
