BobStolb/TERMINAL-06-firmware/3d/knob/knob_B_uncut.stl

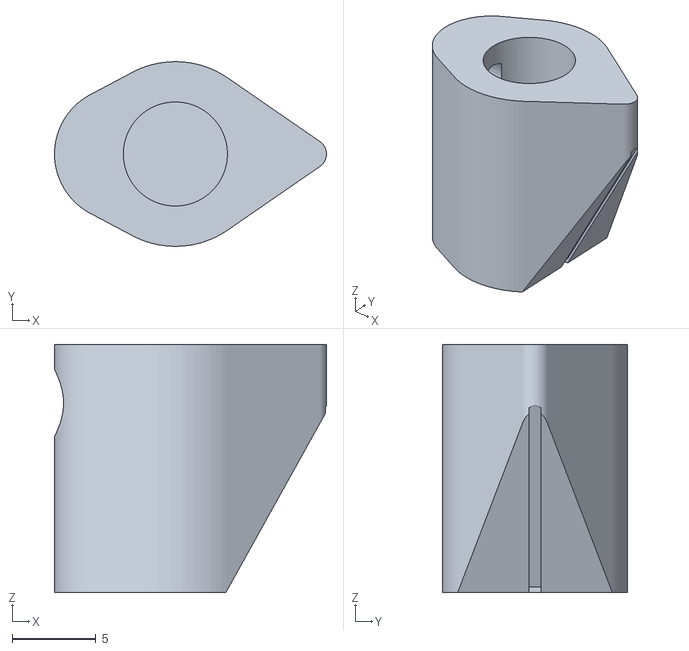
[picture p137: CAD file, 2026-10-07]
3d/knob/knob_B_uncut.stl
16.2 x 11.0 x 14.8
