BobStolb/TERMINAL-06-firmware/3d/case-pair/out/cheek_r.stl

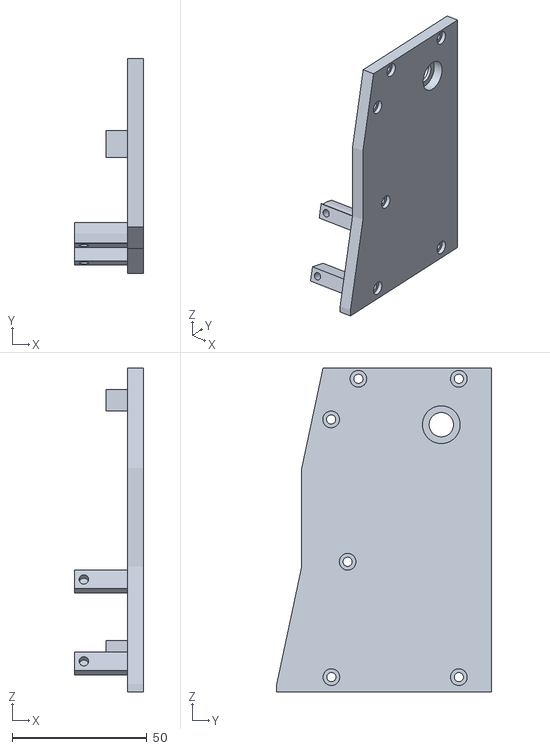
[picture p138: CAD file, 2026-10-07]
3d/case-pair/out/cheek_r.stl
25.6 x 79.4 x 120.0
