BobStolb/TERMINAL-06-firmware/3d/case-pair/out/brow.stl

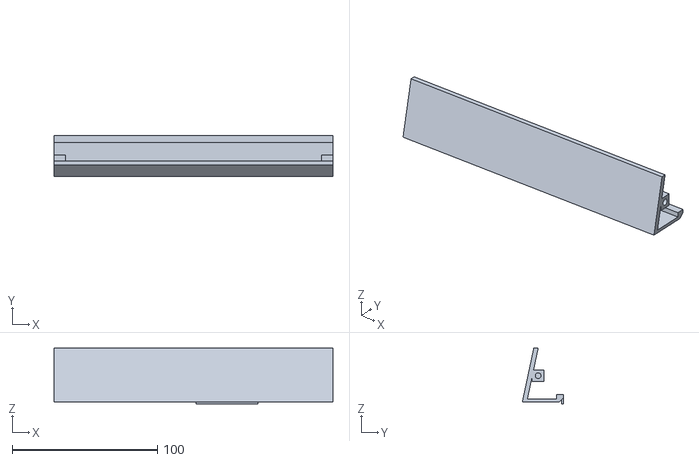
[picture p139: CAD file, 2026-10-07]
3d/case-pair/out/brow.stl
192.4 x 28.5 x 38.5
