BobStolb/TERMINAL-06-firmware/3d/KMD1.step

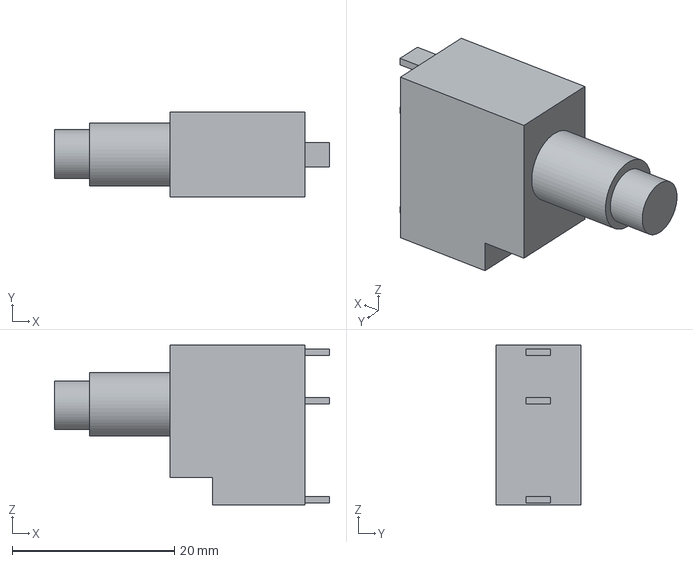
[picture p140: CAD file, 2026-09-08]
3d/KMD1.step
33.9 x 10.5 x 19.7 mm
