BobStolb/TERMINAL-06-firmware/3d/case-pair/out/fascia_blank.stl

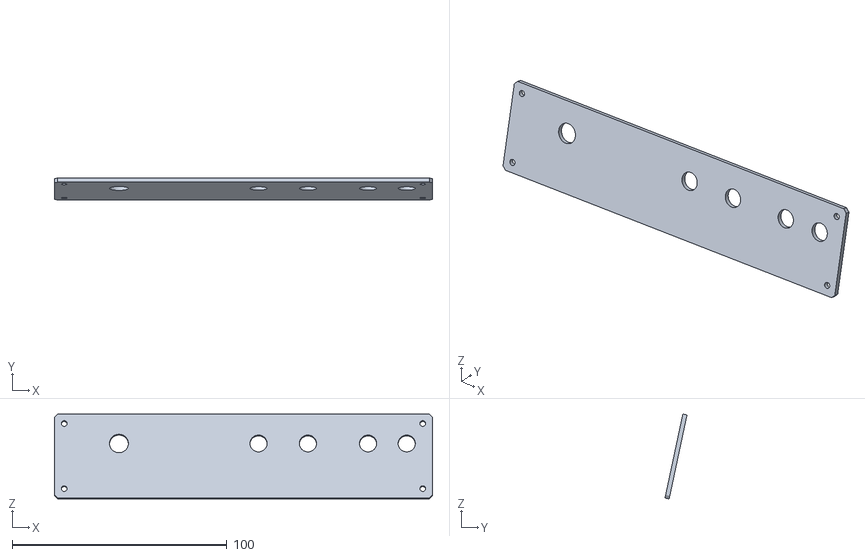
[picture p141: CAD file, 2026-10-07]
3d/case-pair/out/fascia_blank.stl
176.0 x 10.3 x 39.5
