BobStolb/TERMINAL-06-firmware/3d/SR25.step

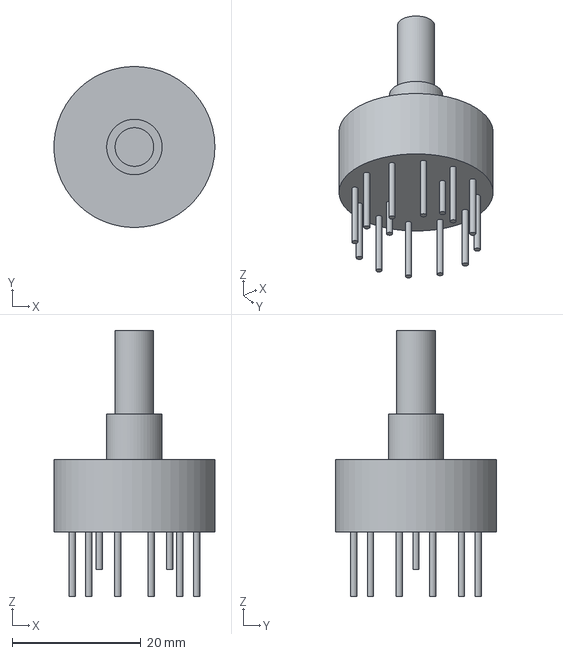
[picture p142: CAD file, 2026-09-08]
3d/SR25.step
25.0 x 25.0 x 41.3 mm
