BobStolb/TERMINAL-06-firmware/3d/INS1.step

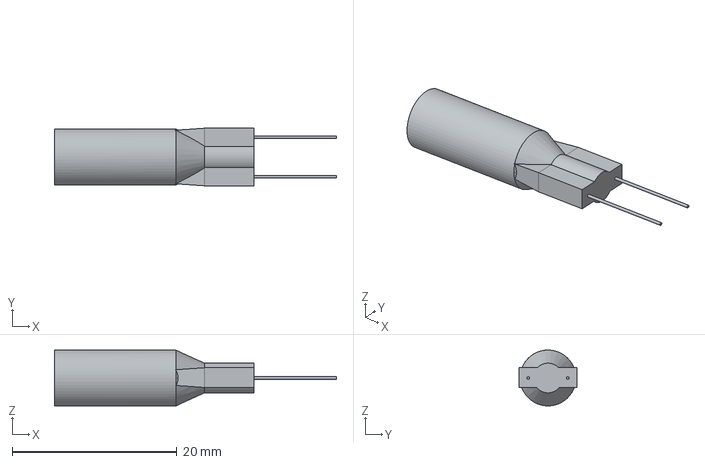
[picture p143: CAD file, 2026-09-08]
3d/INS1.step
34.2 x 7.00 x 6.79 mm
