BobStolb/TERMINAL-06-firmware/3d/MT1.step

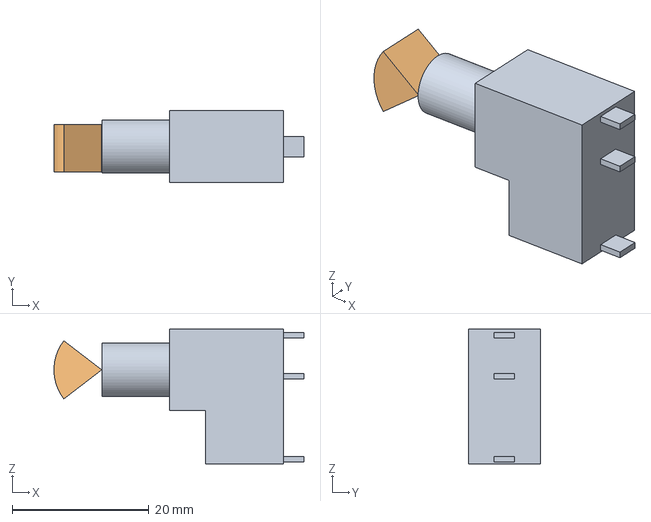
[picture p144: CAD file, 2026-09-08]
3d/MT1.step
36.6 x 10.5 x 19.7 mm
