BobStolb/TERMINAL-06-firmware/qa/page-wiring/handwire-tidy/after-dark-btn-back.png

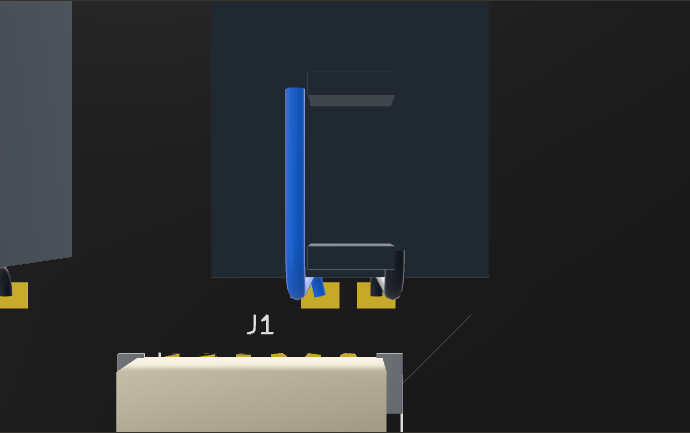
qa/page-wiring/handwire-tidy/after-dark-btn-back.png
