BobStolb/TERMINAL-06-firmware/qa/page-wiring/handwire-tidy/after-dark-btn-iso.png

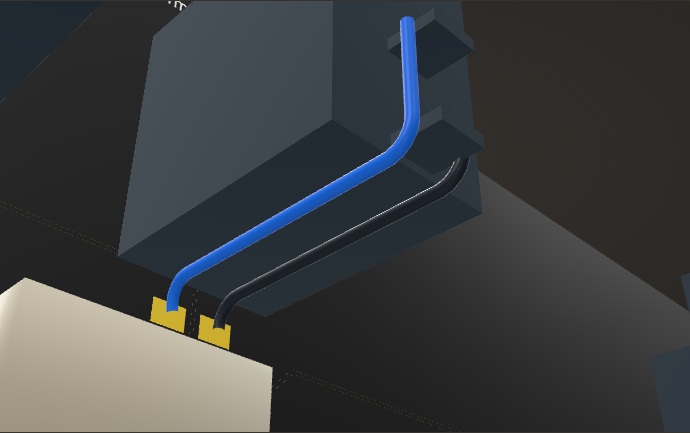
qa/page-wiring/handwire-tidy/after-dark-btn-iso.png
