BobStolb/TERMINAL-06-firmware/qa/page-wiring/handwire-tidy/after-dark-btn-side.png

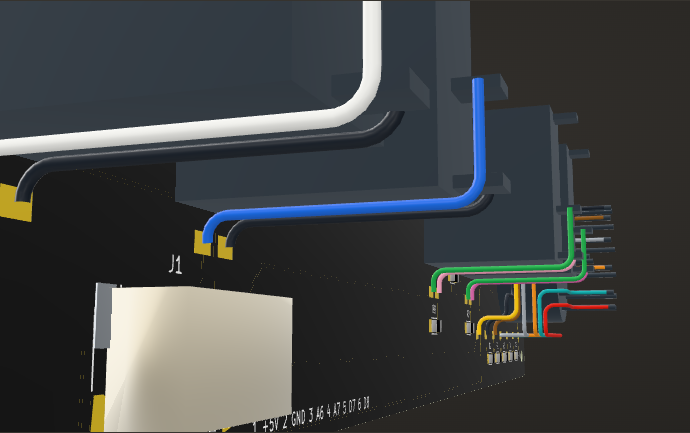
qa/page-wiring/handwire-tidy/after-dark-btn-side.png
