BobStolb/TERMINAL-06-firmware/qa/page-wiring/handwire-tidy/after-dark-lev-back.png

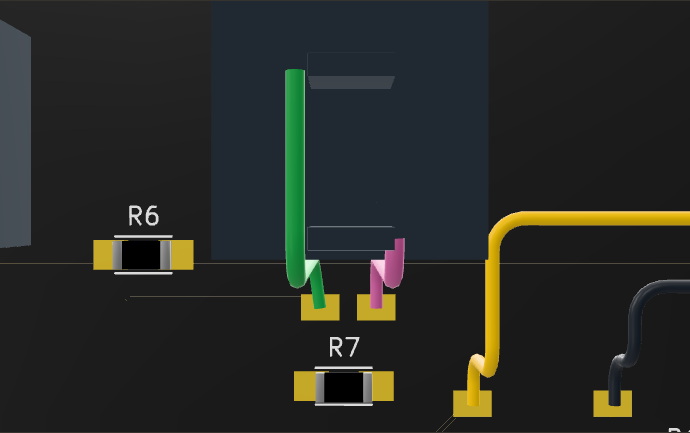
qa/page-wiring/handwire-tidy/after-dark-lev-back.png
