BobStolb/TERMINAL-06-firmware/qa/page-wiring/handwire-tidy/after-dark-lev-iso.png

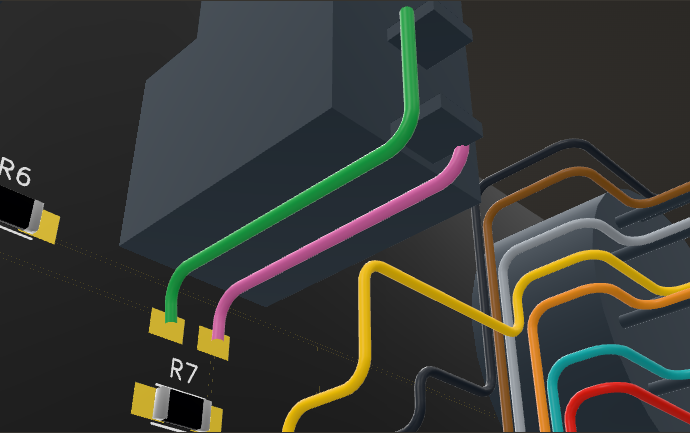
qa/page-wiring/handwire-tidy/after-dark-lev-iso.png
