BobStolb/TERMINAL-06-firmware/qa/page-wiring/handwire-tidy/after-dark-rot-back.png

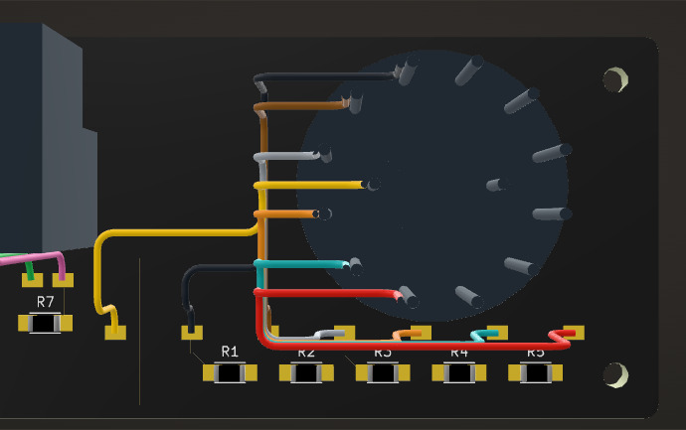
qa/page-wiring/handwire-tidy/after-dark-rot-back.png
