BobStolb/TERMINAL-06-firmware/qa/page-wiring/handwire-tidy/after-dark-rot-flank.png

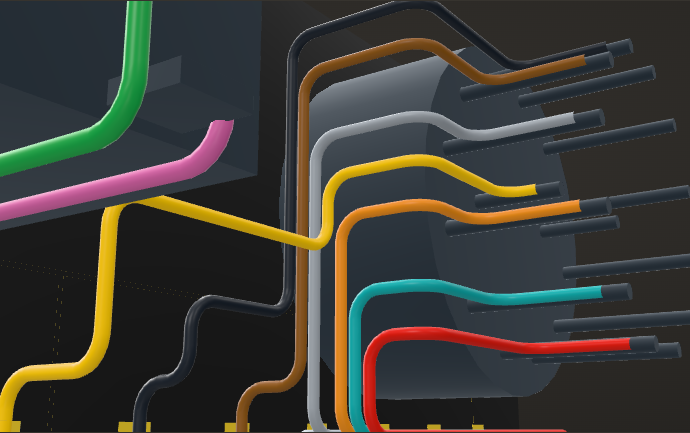
qa/page-wiring/handwire-tidy/after-dark-rot-flank.png
