BobStolb/TERMINAL-06-firmware/qa/page-wiring/handwire-tidy/after-dark-rot-owner.png

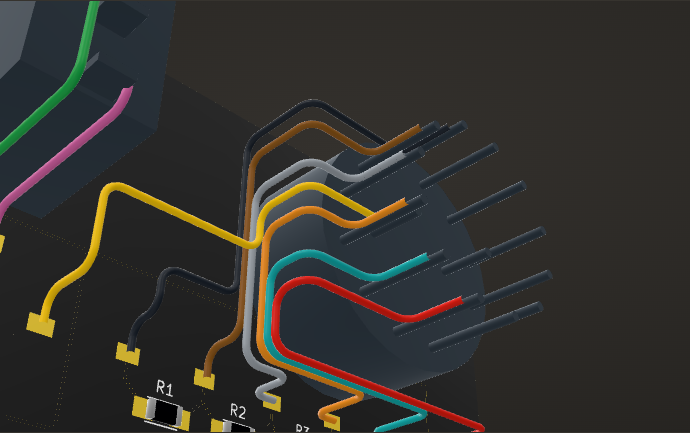
qa/page-wiring/handwire-tidy/after-dark-rot-owner.png
