BobStolb/TERMINAL-06-firmware/qa/page-wiring/handwire-tidy/after-light-btn-iso.png

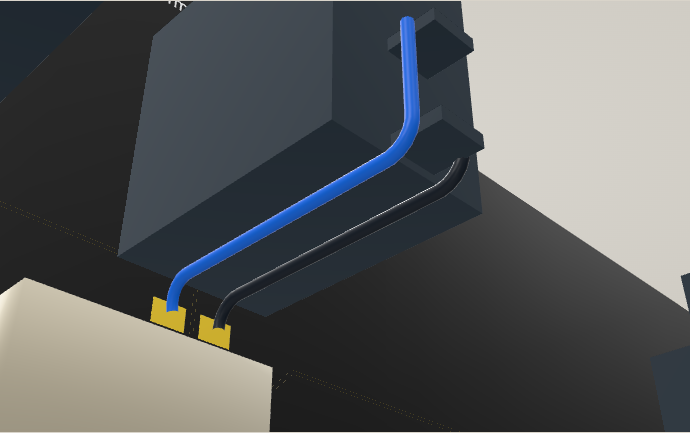
qa/page-wiring/handwire-tidy/after-light-btn-iso.png
