BobStolb/TERMINAL-06-firmware/qa/page-wiring/handwire-tidy/after-light-lev-iso.png

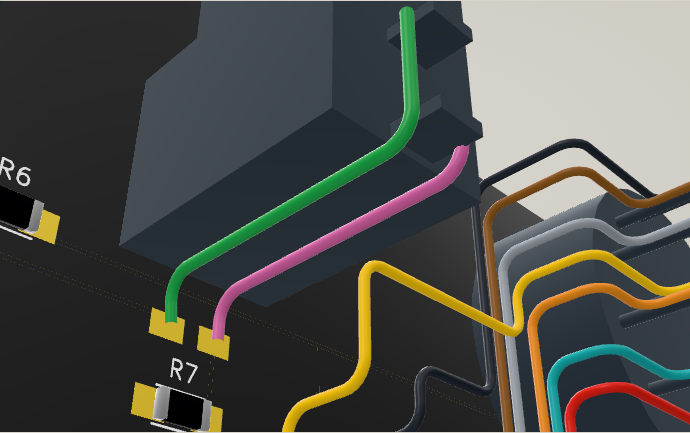
qa/page-wiring/handwire-tidy/after-light-lev-iso.png
