BobStolb/TERMINAL-06-firmware/qa/page-wiring/handwire-tidy/after-light-lev-side.png

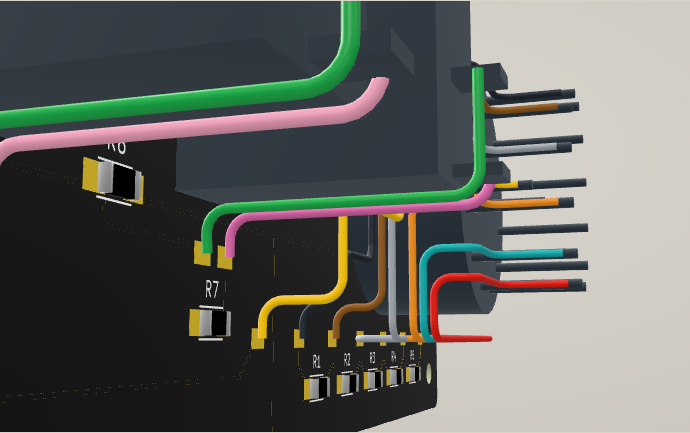
qa/page-wiring/handwire-tidy/after-light-lev-side.png
