BobStolb/TERMINAL-06-firmware/qa/page-wiring/handwire-tidy/after-light-rot-back.png

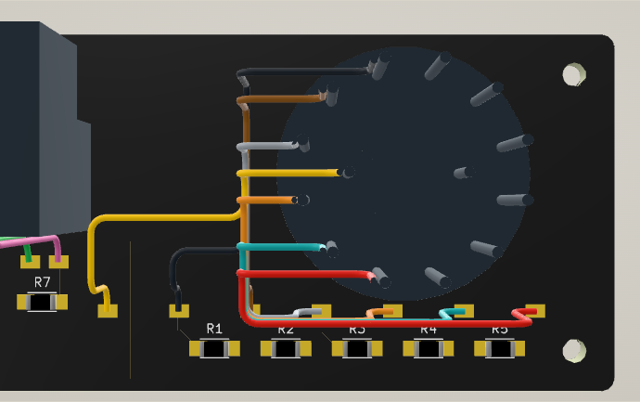
qa/page-wiring/handwire-tidy/after-light-rot-back.png
