BobStolb/TERMINAL-06-firmware/qa/page-wiring/reference/owner-rotary-handwires-messy.png

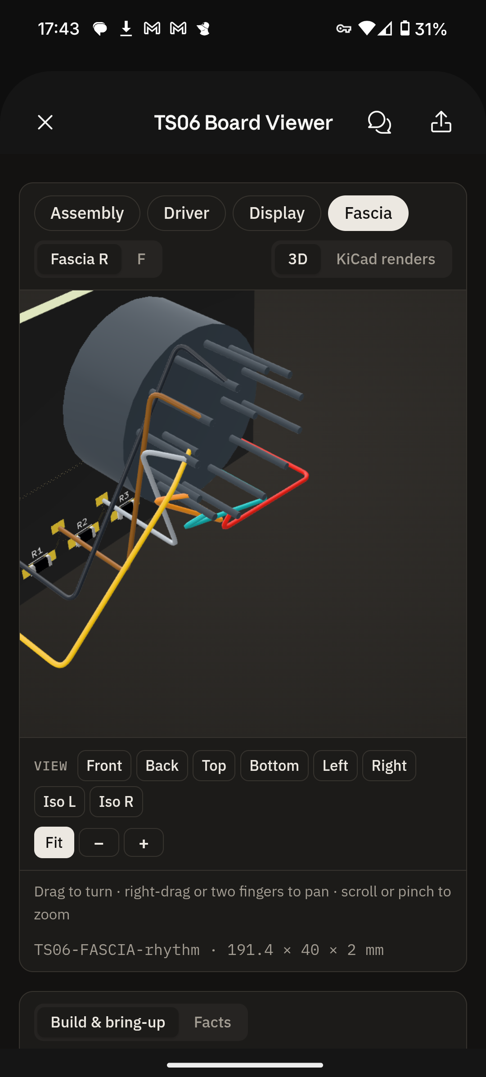
qa/page-wiring/reference/owner-rotary-handwires-messy.png
