BobStolb/TERMINAL-06-firmware/qa/knob/reference/meshok-beak-knobs.png

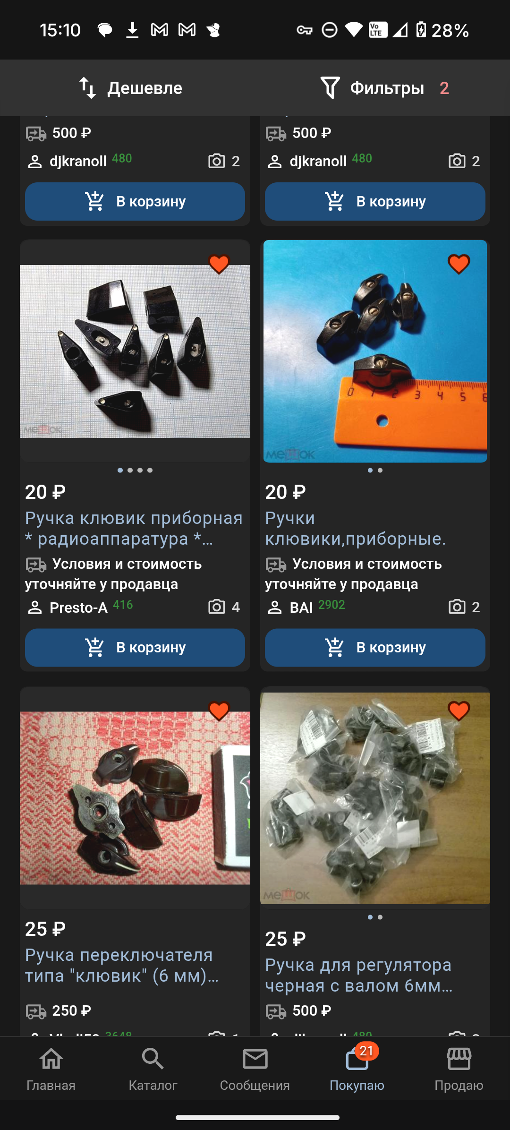
qa/knob/reference/meshok-beak-knobs.png
