BobStolb/TERMINAL-06-firmware/PCB/TS06-COLON/TS06-COLON.kicad_pcb

## KiCad design PCB/TS06-COLON/TS06-COLON.kicad_pcb (2026-09-12)

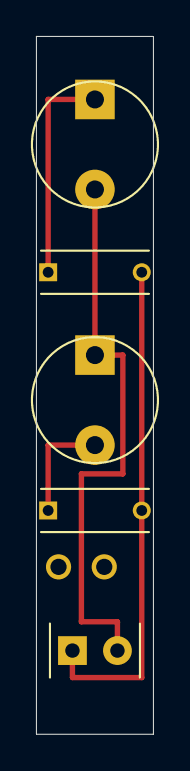
[picture p191: board TS06-COLON.kicad_pcb from above]

Board: 2 copper layers, 6.5 x 38.8 mm, 5 parts (0 on the bottom side), 4 nets.

Parts:
R1, R2: 220k; TS06_R_Axial_EdgeToEdge
V1, V2: INS1; TS06_INS1_Lamp
XS4: XS4; TS06_XS4_JST_XH_2p_RA

Connections:
COLON_RET: V1.2, V2.1, XS4.2
HV185: R1.2, R2.2, XS4.1
R1_LINK: R1.1, V1.1
R2_LINK: R2.1, V2.2
