BobStolb/TERMINAL-06-firmware/firmware/nixieClock_TS06/nixieClock_TS06.ino

/*
  TERMINAL-06 // six-digit nixie clock firmware
  --------------------------------------------------------------
  Derived from AlexGyver's NixieClock v2.5 (MIT-spirited open project,
  https://github.com/AlexGyver/NixieClock_v2) with substantial changes:

    * 4 tubes -> 6 tubes  (4x IN-12 HH:MM + 2x IN-17 SS on the SEC module)
    * anode drivers 5 and 6 on D2 (freed from the buzzer) and D13
    * multiplex ISR rewritten with direct port access (Timer2 prescaler
      stays at AlexGyver's 8) => 7812.5 Hz ISR, 50 Hz whole-display
      refresh with 640 us of optocoupler dead time - the measured
      ghost-free setting (see MULTIPLEX TIMING below and isr.ino)
    * 3 buttons -> 2 buttons + 1 PROGRAM/RUN lever on D12
    * alarm/buzzer removed (D2 reused)
    * anti-poisoning cycle and glitch effect extended over all 6 tubes

  Keep the original attribution if you redistribute the source.
  --------------------------------------------------------------

  CONTROLS
    Lever SW3 down = PROGRAM
      BTN_SET  click : switch field   HH <-> MM   (blinking pair)
      BTN_ADJ  click : +1
      BTN_ADJ  hold  : fast +1
      lever back up  : time written to RTC, seconds zeroed

    Lever SW3 up = RUN
      BTN_SET  click : backlight mode  (breathe / steady / off)
      BTN_SET  hold  : glitch effect on/off
      BTN_ADJ  click : digit transition effect (6 of them)

    Lever SW1 = mains          (hard cut, no pin)
    Lever SW2 = tube backlight (hard cut of the LED +5V rail, no pin)
*/

// ************************** SETTINGS **************************
#define BOARD_TYPE 0
// hours/minutes board type:
// 0 - IN-12 turned (tubes mounted the right way up)   <-- confirmed on this board
// 1 - IN-12 (tubes upside down)   <-- AlexGyver IN-12 board as shipped
// 2 - IN-14
// 3 - custom
// 4 - TS06-DISP + TS06-DRV, the through-hole pair (tools/ts06pair.py). IN-12 turned as
//     type 0; the digit map is the pair's own, chosen so both decoders (U2 for the IN-12
//     bus, U17 for the IN-17 pair, same A0-A3 lines) fan out without a single via.

#define DUTY 190        // boost PWM duty. Sets HV. 180 ~ 175 V, 190 ~ 185 V.
                        // Six tubes need a little more headroom than four:
                        // tune on the bench for 180-190 V no-load (see manual).

// ==================  MULTIPLEX TIMING ==================
/*
  Every number the multiplex ISR uses is derived from these two. Nothing
  else in the firmware may assume a slot length or a brightness range -
  hardcoding those is what caused the ghosting bug this timing fixes.

  WHAT WE ARE OPTIMISING FOR: ghost-free digits, not camera-clean video.
  An earlier revision chased a ~400 Hz refresh so the display would not
  band on camera for the product video, and moved Timer2 to prescaler 1
  to get it. That was the wrong trade. Ghosting is a defect every owner
  looks at every day; 60 fps video flicker is a photography problem we
  can solve with a shutter speed. The camera requirement is dropped, and
  everything it justified - the prescaler rewrite included - goes with it.

  Timer2 runs at prescaler 8, AlexGyver's original: one tick =
  1 / 7812.5 Hz = 128 us. Eight times the tick length means the dead time
  we need costs only a handful of ticks instead of eighteen, which is
  what makes a short slot and a bright display compatible. It also cuts
  the ISR from ~34 % of the CPU to ~4 %.

  SLOT_TICKS   ticks each tube owns: brightness steps plus dead time.
  DEAD_TICKS   ticks at the END of every slot with the anode off AND the
               decoder blanked. This is the ghost margin. The TLP627's
               Darlington output keeps conducting for a few hundred us
               after its drive is removed, so the next tube's digit must
               not reach the shared cathode bus until that tail has died.
               640 us is the bench-measured ghost-free figure for six
               tubes. 256 us (what stock INDI_BRIGHT 24 would give here)
               sits in the band where faint ghosting was still visible,
               which is why INDI_BRIGHT is 21 and not 24 - do not
               "restore" it.

  Derived (recompute these whenever a constant moves - the frame rate
  divides by MUX_SLOTS, the number of slots actually visited, NOT NUM_INDI):
    frame rate    = 7812.5 / SLOT_TICKS / MUX_SLOTS
    dead time     = (SLOT_TICKS - min(INDI_BRIGHT, MAX_BRIGHT)) * 128 us
    per-tube duty = min(INDI_BRIGHT, MAX_BRIGHT) / (SLOT_TICKS * MUX_SLOTS)

  At SLOT_TICKS 26 / DEAD_TICKS 5 / MUX_SLOTS 4 that is 75.1 Hz, 640 us of
  dead time and 20.2 % per-tube duty, with MAX_BRIGHT 21 so INDI_BRIGHT 21
  is exactly at the ceiling and is not being clamped. This is the
  configuration measured ghost-free on the bench.

  Refresh rate is deliberately not a target any more. It only needs to stay
  above flicker fusion; it will beat against camera shutters and that is
  the accepted cost.
*/
#define SLOT_TICKS 26       // ticks per tube slot
#define DEAD_TICKS 5        // forced-blank ticks at the end of each slot

// Highest brightness a tube may be given. The ISR clamps to this, so the
// dead-time gap can never be eaten by turning the brightness up.
#define MAX_BRIGHT (SLOT_TICKS - DEAD_TICKS)

// ================  BENCH BUILD FLAGS  ==================
/*
  Both of these deliberately light digits that are not the current time,
  which makes it impossible to tell real ghosting from intended effect
  when judging the display by eye. Set either to 0 to compile it out for a
  bench session; the code stays in the tree either way.
*/
#define GLITCH_ENABLED 0    // 0 = no random "bad contact" flicker
#define BURN_ENABLED   0    // 0 = no anti-poisoning cathode sweep

// ======================= EFFECTS =======================
byte FLIP_EFFECT = 1;   // stored in EEPROM, changed with BTN_ADJ
// 0 none / 1 crossfade / 2 count / 3 cathode scroll / 4 train / 5 elastic

// =======================  BRIGHTNESS =======================
#define NIGHT_LIGHT 1
#define NIGHT_START 23
#define NIGHT_END 7

// Brightness is measured in ISR ticks, so the usable range is
// 1 - MAX_BRIGHT (21). Values above MAX_BRIGHT are clamped by the ISR and
// behave identically to MAX_BRIGHT - they do not get brighter.
// Dimmer is always safer: dead time is SLOT_TICKS - brightness, so lowering
// a brightness value only ever widens the ghost margin.
#define INDI_BRIGHT 21      // day digit brightness   (1 - 21) - see the
                            // MULTIPLEX TIMING note before raising this
#define INDI_BRIGHT_N 6     // night digit brightness (1 - 21)

#define SEC_BRIGHT_TRIM 4   // added to the seconds tubes only.
                            // IN-17 is a small tube on the same 1/6 duty as
                            // the IN-12s; a few ticks balance them by eye.
                            // Result is clamped to MAX_BRIGHT.
                            // NOTE: with INDI_BRIGHT sitting at MAX_BRIGHT
                            // this trim has no headroom left - lower
                            // INDI_BRIGHT if the seconds need lifting.

#define DOT_BRIGHT 35
#define DOT_BRIGHT_N 15

#define BACKL_BRIGHT 250
#define BACKL_BRIGHT_N 50
#define BACKL_MIN_BRIGHT 20
#define BACKL_PAUSE 400

// =======================  GLITCHES =======================
#define GLITCH_MIN 30
#define GLITCH_MAX 120

// ======================  BLINKING =======================
#define DOT_TIME 500
#define DOT_TIMER 20

#define BACKL_STEP 2
#define BACKL_TIME 5000

// ==================  ANTI-POISONING ====================
#define BURN_TIME 10
#define BURN_LOOPS 3
#define BURN_PERIOD 15      // minutes

// *********************** INTERNALS ***********************
byte BACKL_MODE = 0;
// ms per effect step. Index 1 (crossfade) steps brightness, so its step
// COUNT is indiMaxBright and its duration scales with the brightness range.
// Retune it whenever MAX_BRIGHT changes: interval = 130 * 23 / MAX_BRIGHT,
// which holds the fade at the ~6 s it has always been (the 23-step, 130 ms
// original). At MAX_BRIGHT 21 that is 142. The other effects step digits,
// not brightness, and are unaffected by the slot length.
byte FLIP_SPEED[] = {0, 142, 50, 40, 70, 70};
byte FLIP_EFFECT_NUM = sizeof(FLIP_SPEED);
boolean GLITCH_ALLOWED = 1;

#define NUM_INDI 6          // total tubes (sizes every per-tube array)
#define NUM_HM   4          // tubes carrying hours+minutes (effects act on these)

// ================  MULTIPLEX ROTATION  =================
/*
  How many slots the ISR actually visits per rotation. Normally NUM_INDI.

  Set to 4 to keep the ISR off the two seconds slots WITHOUT resizing any
  array - the arrays stay NUM_INDI long, the rotation just stops short.

  Why this matters, and why it is the first thing to try when stock
  AlexGyver firmware is clean on a board where this one ghosts:

  Stock writes the decoder ONLY inside its changeover, in the same breath
  as switching that tube's anode on. A digit is therefore never sitting on
  the shared cathode bus without a driven anode to take the current.

  This fork rotates through 6 slots. On a board with no SEC module fitted
  there is no tube and no anode on slots 4 and 5, so for 21 of every 26
  ticks in those two slots a digit IS on the cathode bus with NO anode
  driven anywhere. Any leakage - a TLP627 still tailing off, a tube not
  fully deionised - has no preferred path to take, so it lights that digit
  on whichever real tube is still decaying. Stock cannot create this
  condition; it has no empty slots. That is a firmware difference, not a
  hardware fault, and no amount of dead time fixes it because the offending
  digit is driven in a slot that has no anode of its own to blank.

  CONFIRMED ON THE BENCH: MUX_SLOTS 4 with SLOT_TICKS 26 is ghost-free on
  this board; the same firmware at 6 slots ghosts. Empty slots were the
  cause, not the dead time - which is why three rounds of widening the gap
  changed nothing.

  The invariant to hold onto: NEVER put a digit on the shared cathode bus
  without a real anode to take the current. A slot whose tube is absent
  must either be left out of the rotation (MUX_SLOTS) or marked off
  (indiDimm 0 or anodeStates 0, both of which make the ISR skip the slot
  and leave the bus blanked). This bites again the moment the board is
  populated with fewer tubes than there are channels - which is exactly
  what happens during bring-up.
*/
#if (BOARD_TYPE == 4)
#define MUX_SLOTS 6         // the pair always carries all six tubes, so no
                            // slot is ever empty.
                            // BENCH ITEM, first pair: 6 slots at SLOT_TICKS 26
                            // is a 7812.5 / 26 / 6 = 50.1 Hz frame (4 slots:
                            // 75.1 Hz) and 21 / (26 * 6) = 13.5 % per-tube duty
                            // (4 slots: 20.2 %); the 640 us dead time does not
                            // change. Confirm ghost-free, no visible flicker,
                            // and the IN-12s still bright enough at 2/3 duty.
#else
#define MUX_SLOTS 4         // slots the ISR visits: set to the number of
                            // tubes ACTUALLY POPULATED, never more
#endif

// ---------------- pins ----------------
#define KEY4 2      // anode, seconds TENS   (was PIEZO)
#define KEY0 3      // anode, hours tens
#define KEY1 4      // anode, hours units
#define KEY2 5      // anode, minutes tens
#define KEY3 6      // anode, minutes units
#define BTN_SET 7   // button 1
#define BTN_ADJ 8   // button 2
#define GEN 9       // HV boost oscillator
#define DOT 10      // neon dot / colon
#define BACKL 11    // tube backlight PWM
#if (BOARD_TYPE == 4)
#define M_LED 12    // the "m" LED: R53 -> HL9 -> BL_K. No SW3 on this board,
                    // readLever() reads the fascia instead (ts06pair.ino)
#else
#define LEVER 12    // SW3 PROGRAM(LOW) / RUN(HIGH)
#define readLever() digitalRead(LEVER)
#endif
#define KEY5 13     // anode, seconds UNITS

// decoder K155ID1 (74141)
#define DECODER0 A0
#define DECODER1 A1
#define DECODER2 A2
#define DECODER3 A3

// ---------------- tube maps ----------------
#if (BOARD_TYPE == 0)
const byte digitMask[] = {7, 3, 6, 4, 1, 9, 8, 0, 5, 2};
const byte opts[NUM_INDI] = {KEY0, KEY1, KEY2, KEY3, KEY4, KEY5};
const byte cathodeMask[] = {1, 6, 2, 7, 5, 0, 4, 9, 8, 3};

#elif (BOARD_TYPE == 1)
const byte digitMask[] = {2, 8, 1, 9, 6, 4, 3, 5, 0, 7};
const byte opts[NUM_INDI] = {KEY3, KEY2, KEY1, KEY0, KEY4, KEY5};
const byte cathodeMask[] = {1, 6, 2, 7, 5, 0, 4, 9, 8, 3};

#elif (BOARD_TYPE == 2)
const byte digitMask[] = {9, 8, 0, 5, 4, 7, 3, 6, 2, 1};
const byte opts[NUM_INDI] = {KEY3, KEY2, KEY1, KEY0, KEY4, KEY5};
const byte cathodeMask[] = {1, 0, 2, 9, 3, 8, 4, 7, 5, 6};

#elif (BOARD_TYPE == 3)
const byte digitMask[] = {0, 1, 2, 3, 4, 5, 6, 7, 8, 9};
const byte opts[NUM_INDI] = {KEY0, KEY1, KEY2, KEY3, KEY4, KEY5};
const byte cathodeMask[] = {0, 1, 2, 3, 4, 5, 6, 7, 8, 9};

#elif (BOARD_TYPE == 4)
// digit d -> K155ID1 code; the same code on U2 and U17 lights digit d on every tube
// (tools/ts06pair.py DIGIT_MASK4). cathodeMask is the tube's, as type 0.
// The anode pins are the usual six, driving other tubes: hours on D6/D5, minutes on
// D4/D3, S10 on D2, S1 on D13 (tools/ts06pair.py TUBE_PIN4), so the Nano's digital row
// fans out on the driver board without crossing itself. The same order as types 1 and 2.
const byte digitMask[] = {1, 0, 5, 4, 6, 7, 3, 2, 9, 8};
const byte opts[NUM_INDI] = {KEY3, KEY2, KEY1, KEY0, KEY4, KEY5};
const byte cathodeMask[] = {1, 6, 2, 7, 5, 0, 4, 9, 8, 3};
// The rest of what is particular to the pair: all six slots scanned (MUX_SLOTS
// above), D12 the "m" LED rather than SW3, PROGRAM/RUN read from the fascia's
// MODE rotary on A6, the fascia's "-" (D7) and "+" (D8) as BTN_SET / BTN_ADJ,
// and the MCP23017 that sources the backlight LEDs and feeds the IN-15
// decoders. All in ts06pair.ino, with what is not written yet.
#endif

/*
  The SEC module routes each IN-17 cathode to the SAME K155ID1 output the
  IN-12s use for that digit, so one digitMask covers all six tubes.
  If you wire the IN-17s differently you will need a second mask - see the
  build manual, section "SEC module cathode routing".
*/
