BobStolb/TERMINAL-06-firmware/firmware/nixieClock_TS06/glitch.ino

/*
  Random "bad contact" flicker on one tube. Now picks from all six, and
  restores that tube to its own brightness (the seconds tubes carry the trim).
*/
void glitchTick() {
  if (!glitchFlag && secs > 7 && secs < 55) {
    if (glitchTimer.isReady()) {
      glitchFlag = true;
      indiState = 0;
      glitchCounter = 0;
      glitchMax = random(2, 6);
      glitchIndic = random(0, NUM_INDI);
      glitchTimer.setInterval(random(1, 6) * 20);
    }
  } else if (glitchFlag && glitchTimer.isReady()) {
    indiDimm[glitchIndic] = indiState * indiMaxBright;
    indiState = !indiState;
    glitchTimer.setInterval(random(1, 6) * 20);
    glitchCounter++;
    if (glitchCounter > glitchMax) {
      glitchTimer.setInterval(random(GLITCH_MIN * 1000L, GLITCH_MAX * 1000L));
      glitchFlag = false;
      applyBright();
    }
  }
}
