BobStolb/TERMINAL-06-firmware/tools/fascia_gold.py

#!/usr/bin/env python3
"""Gold-trace variations for TS06-FASCIA: one white-silk base, four different golds.

    python3 tools/fascia_gold.py VARIANT OUT.kicad_pcb [--base A|R] [--base-pcb BOARD.kicad_pcb]
    python3 tools/fascia_gold.py all OUTDIR [--base A|R]        # every variant into OUTDIR
    python3 tools/fascia_gold.py --list
    python3 tools/fascia_gold.py VARIANT OUT.kicad_pcb --preview OUT.png   # a quick flat picture
    python3 tools/fascia_gold.py all OUTDIR --drc                       # KiCad 10 DRC on each, against the base's own
    (the KiCad 3D renders come from tools/render_kicad.py; KiCad runs in Docker unless KICAD_CLI names a binary)

VARIANT is one of ladder, divider, fans, guilloche. --base picks the board: A is PCB/TS06-FASCIA
(176 x 40, controls on y 14), R is PCB/TS06-FASCIA-rhythm (191.4 x 40, controls on y 16). The
output is a scratch board. Nothing under PCB/ is written.
--base-pcb BOARD reads that board in place of the committed one (for R: the board of
`tools/mkpcb_fascia_rhythm.py --out FILE [--open-holes]`, so the fascia with its control holes opened is built the same way;
fab/HOLES-VARIANT.md). Every check below runs against it as against the committed board.

THE WHITE SILK IS CONSTANT. It is the "Plates" silk of tools/fascia_art.py, taken from
fascia_art.v_plates() item for item: the six names, the MODE / FIELD / SUB nameplates, the hairline
dial arc and the leaders. Only the gold changes, so the owner compares gold against gold. build()
asserts that the silk items of every variant are identical to Plates' own, and same_copper()
proves every non-artwork item of the board (footprints, tracks, zone, holes, edge, back silk) is
byte for byte the base's.

SAFETY. On A and R the front copper layer carries no pad, no track, no via and no zone (every part
is on the back; the front holes are NPTH with no annular ring): front_copper_free() checks this on
the base. All gold is therefore netless copper and touches no net; none of it is tied to a net.
The checker (check()) keeps:
  * gold to gold: 0.3 mm between mask openings (0.2 mm between copper, the copper is 0.05 mm larger
    each side) wherever two separate pieces of gold meet; pieces in one group are one piece;
  * gold to silk 0.3 mm; silk to silk 0.25 mm;
  * gold 6.0 mm from each lever's and button's centre (the body), 9.0 mm from the dial's shaft
    (the knob), out of each lever's swing (2 mm either side, 7 mm up, 6.3 mm down);
  * 1.4 mm from the board edge and 3.0 mm from a screw centre;
  * labels 3.0 mm tall or more (there are no gold letters; the - and + are drawn as strokes 3.2 mm long).
KiCad's project rules ask for 0.5 mm copper to the edge and 0.25 mm copper to a hole; these keep
a wide margin over both.

TRUTH. The gold draws things that are so, and the generator reads them from the board rather than
trusting a number typed here: circuit() reads the divider's chain and the lever ladder from the
nets, and asserts they are GND - R1 - TAP2 - R2 - TAP3 - R3 - TAP4 - R4 - TAP5 - R5 - +5V, five
equal resistors; SW1's tap pads carry the same six nets; the levers reach A7 through LEVA / LEVB.
READ (below) is spec section 1's control table: which screens read which control.

ON R. Only divider is laid out for R (the favourite, so the owner can see it on the tube-grid board).
R puts FIELD 39 mm from the dial, so there position 5's trace drops 45 degrees into the frame's side, as
in Plates, and takes no pad (it would touch FORMAT/DATE). The other three are laid out for A; on R
they fail their checks (ladder refuses).
--leaders STYLE (R only) picks the style of the white leaders from the dial's positions to their names, drawn by
fascia_art.v_plates (level, the owner's pick of 2026-10-02, is the default on R; slope is A's and R's first face;
dogleg, centred: see tools/fascia_art.py). The silk is still Plates' item for item, whatever the style; the gold's own
layout follows the names' rows. The level style sets the six names (2.37 mm) below the owner's 3 mm legend rule (down to
the fab's 1.0 mm): check() allows that for those six only.

THE VARIANTS (one line each; the owner's review has pictures):
  ladder    the SUB rule as a Soviet relay-logic ladder (GOST-style contacts, an OR join, FIELD's
            gap closed by the lever, SUB as the coil, earth), the dial as a curved ladder, the two
            buttons as contacts to earth.
  divider   the dial IS the divider: the six taps are pads round the arc with a resistor body
            between each pair, tails to GND and +5V, teardrops on every pad; the rule in the same
            PCB language.
  fans      every control wears the dial's own 30-degree fan; a heavy tick is a screen where the spec
            reads that control, a hairline tick a screen where it does nothing (1 and 6 are parking);
            SUB's fan is the box the rule feeds.
  guilloche a rose-engine rosette behind the dial's scale, the rule as three braided cords, SUB in a
            double engraved frame, the - and + on coin medallions.
"""
import argparse, collections, json, math, os, re, shutil, subprocess, sys, tempfile, uuid

HERE = os.path.dirname(os.path.abspath(__file__))
sys.path.insert(0, HERE)
import fascia_art as fa
from fascia_art import P, ANG, NAMES, THROW, RULES

# spec section 1 (knowledge/TERMINAL-06-spec.txt, Rev D.3): the screens (1..6) on which each control is read.
# SUB's read is conditional on FIELD being thrown down; 1 (NORMAL) and 6 (INFO) ignore everything.
READ = {"FIELD": (2, 3, 4, 5), "SUB": (3, 5), "-": (2, 3, 4, 5), "+": (2, 3, 4, 5)}
PAD_R = 1.1            # radius of FIELD's contact pad: its top edge is the throw point (6.6 mm below centre)
EDGE_MM = 1.4          # gold this far inside the edge (KiCad's rule is 0.5)
HOLE_GAP = 0.1         # a gold line that joins a ring stops with its round end this far short of the ring's hole


# ============================================================================ geometry helpers
def sub(a, b):
    return (a[0] - b[0], a[1] - b[1])


def add(a, b, k=1.0):
    return (a[0] + k * b[0], a[1] + k * b[1])


def unit(v):
    n = math.hypot(v[0], v[1])
    return (v[0] / n, v[1] / n)


def dist2(a, b):
    return math.hypot(a[0] - b[0], a[1] - b[1])


def fillet(pts, r):
    """A polyline with round corners: [('line', a, b) | ('arc', c, r, a0, a1)]. A corner whose
    tangent length would pass the middle of a neighbouring segment gets a smaller radius."""
    out, cur, n = [], pts[0], len(pts)
    for i in range(1, n - 1):
        p0, p, p1 = pts[i - 1], pts[i], pts[i + 1]
        d1, d2 = unit(sub(p, p0)), unit(sub(p1, p))
        cr = d1[0] * d2[1] - d1[1] * d2[0]
        phi = math.acos(max(-1.0, min(1.0, d1[0] * d2[0] + d1[1] * d2[1])))
        if phi < 1e-6 or r <= 0:
            continue
        t = r * math.tan(phi / 2)
        tmax = min(dist2(p0, p) if i == 1 else dist2(p0, p) / 2, dist2(p, p1) if i == n - 2 else dist2(p, p1) / 2)
        rr = r
        if t > tmax:
            t, rr = tmax, tmax / math.tan(phi / 2)
        t1, t2 = add(p, d1, -t), add(p, d2, t)
        if dist2(cur, t1) > 1e-6:
            out.append(("line", cur, t1))
        s = 1.0 if cr > 0 else -1.0
        c = add(t1, (-d1[1] * s, d1[0] * s), rr)
        a1 = math.degrees(math.atan2(t1[1] - c[1], t1[0] - c[0]))
        ph = math.degrees(phi)
        out.append(("arc", c, rr, a1, a1 + ph) if s > 0 else ("arc", c, rr, a1 - ph, a1))
        cur = t2
    if dist2(cur, pts[-1]) > 1e-6:
        out.append(("line", cur, pts[-1]))
    return out


def sample(prims, step=0.3):
    """The centre-line of fillet() output as a dense list of points (for braiding)."""
    pts = []
    for pr in prims:
        if pr[0] == "line":
            a, b = pr[1], pr[2]
            n = max(1, int(dist2(a, b) / step))
            seg = [(a[0] + (b[0] - a[0]) * i / n, a[1] + (b[1] - a[1]) * i / n) for i in range(n + 1)]
        else:
            _, c, r, a0, a1 = pr
            # the arc runs from the corner's entry to its exit; entry is the end nearer the previous point
            n = max(2, int(abs(a1 - a0) * math.pi / 180 * r / step))
            seg = [P(c, r, a0 + (a1 - a0) * i / n) for i in range(n + 1)]
            if pts and dist2(pts[-1], seg[0]) > dist2(pts[-1], seg[-1]):
                seg.reverse()
        if pts and dist2(pts[-1], seg[0]) < 1e-6:
            seg = seg[1:]
        pts.extend(seg)
    return pts


class GArt(fa.Art):
    def route(self, pts, w, r, grp, ink="gold"):
        for pr in fillet(pts, r):
            if pr[0] == "line":
                self.line(ink, pr[1], pr[2], w, grp)
            else:
                self.arc(ink, pr[1], pr[2], pr[3], pr[4], w, grp)

    def dot(self, c, r, grp):
        self.circle("gold", c, r, 0.0, grp, fill=True)

    def ring(self, c, r, w, grp):
        self.circle("gold", c, r, w, grp)

    def polyline(self, pts, w, grp, ink="gold"):
        for a, b in zip(pts, pts[1:]):
            if dist2(a, b) > 1e-6:
                self.line(ink, a, b, w, grp)

    def teardrop(self, c, rp, d, w, length, grp):
        """A tapered fillet that blends a trace of width w, leaving the pad of radius rp at c in the
        direction d, into the pad: two tangent lines from the trace's edges, length mm along d."""
        d = unit(d)
        n = (-d[1], d[0])
        pts = []
        for s in (1.0, -1.0):
            a = add(add(c, d, length), n, s * w / 2)
            v = sub(a, c)
            al, dd = math.atan2(v[1], v[0]), math.hypot(v[0], v[1])
            be = math.acos(min(1.0, rp / dd))
            t = P(c, rp, math.degrees(al + s * be))
            pts.append((a, t))
        (a1, t1), (a2, t2) = pts
        self.poly("gold", [a1, a2, t2, t1], grp)

    def pad(self, c, rp, grp, d=None, w=None, tear=None):
        self.dot(c, rp, grp)
        if d is not None and tear:
            self.teardrop(c, rp, d, w, tear, grp)

    def ground(self, c, direction, w, grp, stem=1.4, gap=1.0, halves=(2.2, 1.4, 0.6), start=0.0):
        """A GOST earth: a stem, then three bars, each shorter, across the stem. The stem runs from start mm
        along direction (from a ring's rim, say) to stem mm; the bars stand at its end."""
        d = unit(direction)
        n = (-d[1], d[0])
        e = add(c, d, stem)
        self.line("gold", add(c, d, start) if start else c, e, w, grp)
        for k, h in enumerate(halves):
            m = add(e, d, gap * k)
            self.line("gold", add(m, n, h), add(m, n, -h), w, grp)

    def rect(self, c, u, length, width, w, grp):
        """An outlined rectangle centred on c, its long side along u."""
        u = unit(u)
        n = (-u[1], u[0])
        h, k = length / 2, width / 2
        q = [add(add(c, u, sx * h), n, sy * k) for sx, sy in ((-1, -1), (1, -1), (1, 1), (-1, 1))]
        self.polyline(q + [q[0]], w, grp)


# ============================================================================ the constant silk and the layout
def silk_base(G, leaders=None):
    """Plates' silk, item for item (tools/fascia_art.py v_plates), and nothing else. leaders: its leader style
    (fascia_art.LEADER_STYLES; default fascia_art.LEADERS, and that empty: level on R, slope on A)."""
    A = GArt()
    P0 = fa.v_plates(G, leaders)
    A.name_min = P0.name_min
    for it in P0.items:
        if it["ink"] == "silk":
            A.items.append(it)
    return A


def layout(G, A):
    ctrl = G["ctrl"]
    txt = {it["s"]: it for it in A.items if it["kind"] == "text"}
    L = dict(D=ctrl["SW1"], F=ctrl["SW2"], S=ctrl["SW3"], M=ctrl["SW4"], Pl=ctrl["SW5"], W=G["W"], H=G["H"])
    L["rows"] = [txt[n]["y"] for n in NAMES]
    L["nbox"] = [fa.text_box(txt[n]) for n in NAMES]
    L["plate"] = {n: fa.text_box(txt[n]) for n in ("MODE", "FIELD", "SUB")}
    L["ny"] = txt["MODE"]["y"]
    L["e3"], L["e5"] = L["nbox"][2][2] + 2.2, L["nbox"][4][2] + 2.2       # where DISPLAY's and FORMAT/DATE's traces start
    L["compact"] = (L["F"][0] - L["D"][0]) < 50                            # R: FIELD is close to the dial (Plates' own test)
    if L["compact"]:                                                       # and Plates starts the traces a little sooner there
        L["e3"] -= 1.0
        L["e5"] -= 1.4
    L["throw_y"] = L["F"][1] + THROW + PAD_R                                # centre of FIELD's contact pad
    return L


# ============================================================================ the four golds
def key_glyph(A, c, sign, size, w, grp):
    h = size / 2.0
    A.line("gold", (c[0] - h, c[1]), (c[0] + h, c[1]), w, grp)
    if sign == "+":
        A.line("gold", (c[0], c[1] - h), (c[0], c[1] + h), w, grp)
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
